ve2cuy/breadboard-PC/ROM.md

## Vue d'ensemble

Voici un schéma de principe des connexions :

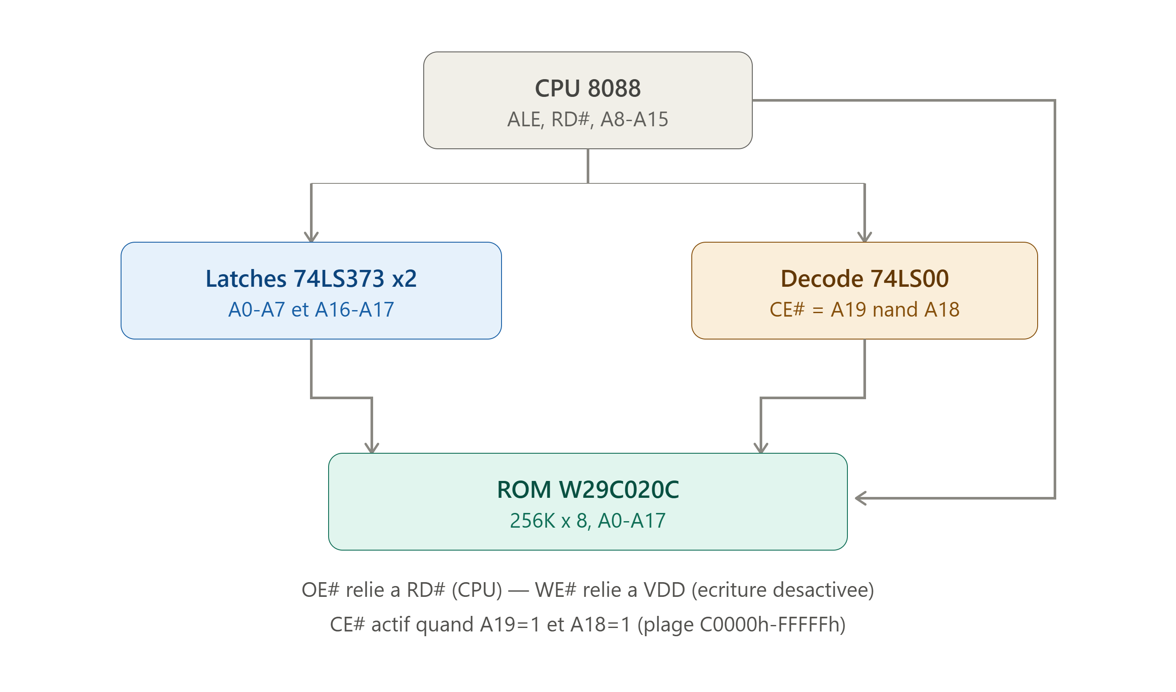
[picture p3: medias/interfacage_8088_w29c020c.png]
w29c020


Le 8088 multiplexe une partie de son bus d'adresses avec les données et les status, donc il faut du matériel de démultiplexage entre le CPU et la ROM.

## Détail du câblage

**Bus d'adresses multiplexé (AD0-AD7)**
Ces 8 broches du CPU (pins 9-16 en boîtier DIP) portent l'adresse en début de cycle bus, puis les données ensuite. Il faut les **latcher** avec un `74LS373` (ou `74LS573`) déclenché par **ALE** (Address Latch Enable, pin 25) pour récupérer A0-A7 de façon stable → connecté à **A0-A7 de la ROM** (pins 12, 11, 10, 9, 8, 7, 6, 5).

**Bus d'adresses/status multiplexé (A16-A19/S3-S6)**
Pareil : ces 4 broches (pins 35-38) sont multiplexées avec des bits de status en mode max. Un second `74LS373` latché par ALE isole **A16 et A17** → connectés à **A16 (pin 2) et A17 (pin 30) de la ROM**. (A18-A19 latchés servent uniquement au décodage, pas à la ROM qui n'a que 18 lignes d'adresse.)

**Bus d'adresses direct (A8-A15)**
Ces broches (pins 22-24, 17-21 en DIP) sont **déjà stables** pendant tout le cycle bus — pas besoin de latch. Connecter **directement** aux entrées **A8-A15 de la ROM** (pins 4, 27, 26, 23, 25, 28, 29, 3 — l'ordre n'est pas séquentiel sur le boîtier, vérifie bien le brochage).

**Décodage du CE# (Chip Enable)**
Ta ROM occupe C0000h-FFFFFh, soit le quart supérieur du méga-octet adressable : cela correspond exactement à **A19=1 ET A18=1**. Une simple porte **NAND 74LS00** (2 entrées : A19 latché, A18 latché) donne directement un signal actif bas quand les deux sont hauts → branche sa sortie sur **CE# (pin 22)** de la ROM.

**OE# et WE#**
- **OE#** (pin 24) ← **RD#** du CPU (pin 32 en min mode) : la ROM ne sort ses données que pendant une vraie lecture.
- **WE#** (pin 31) ← **VDD** (+5V) en permanence : désactive toute écriture accidentelle pendant le fonctionnement normal. Pour reprogrammer la puce, il faudra soit la retirer et utiliser un programmateur externe, soit prévoir un jumper qui reconnecte WE# au WR# du CPU en mode "programmation".

## Point de vigilance

Vérifie que **IO/M#** (pin 28 du 8088) ne doit **pas** activer la ROM pendant les cycles d'E/S — dans ce montage, comme le décodage se fait uniquement sur A18/A19 (qui n'existent pas dans l'espace I/O 16 bits séparé du 8088), il n'y a normalement pas de conflit. Mais si ton design utilise des cycles d'E/S 20 bits étendus ou une autre topologie de bus, ajoute **IO/M#** comme troisième entrée du NAND (via porte NAND 3 entrées type `74LS10`) pour garantir CE# actif uniquement en cycle mémoire.

---

Déboguage

```asm
0C0000 -> 11000000000000000000
080000 -> 10000000000000000000

Adresse   Code obj.      Ligne   Source
-------   ---------      -----   ------------------------------
                            1    ORG     0000h          ; = physique C0000h (début de la ROM)
                            2
                            3    START:
0000      B0 AA             4     MOV     AL, 0AAh       ; AL = 10101010b
0002      E6 10             5     OUT     10h, AL        ; envoie AL sur le port 10h
0004      BB 00             6     MOV     BX, 0000h      ; compteur de délai
                            7    DELAI1:
0007      4B                8     DEC     BX
0008      75 FD             9     JNZ     DELAI1
000A      B0 00            10     MOV     AL, 00h        ; AL = 00000000b
000C      E6 10            11     OUT     10h, AL
000E      BB 00            12     MOV     BX, 0000h
                           13    DELAI2:
0011      4B               14     DEC     BX
0012      75 FD            15     JNZ     DELAI2
0014      EB EA            16     JMP     START          ; boucle infinie

Taille totale du programme : 0016h (22) octets
```

---

# Calcul de la fréquence de clignotement

Compte tenu du programme précédent, avec une fréquence d'horloge du 8088 à 4,77mhz, à quelle fréquence clignote les LED sur le port 10h?

Pour cela, il faut calculer le nombre de cycles d'horloge (clocks) que prend chaque instruction sur un 8088, puis convertir en temps réel avec la fréquence de 4,77 MHz.

# Calcul du clignotement à 4,77 MHz

## Nombre total de cycles CPU par cycle complet (ON + OFF)

| Instruction | Cycles |
|---|---|
| MOV AL,0AAh | 4 |
| OUT 10h,AL | 10 |
| MOV BX,0000h | 4 |
| DELAI1 (boucle complète, 65536 itérations) | 1 179 636 |
| MOV AL,00h | 4 |
| OUT 10h,AL | 10 |
| MOV BX,0000h | 4 |
| DELAI2 (boucle complète) | 1 179 636 |
| JMP START (saut court) | 15 |
| **Total** | **2 359 323 cycles** |

## Fréquence d'horloge

$$T_{clock} = \frac{1}{4{,}77 \text{ MHz}} \approx 209{,}6 \text{ ns}$$

## Durée d'un cycle complet (période)

$$T = \frac{2\,359\,323}{4\,770\,000} \approx 0{,}49466 \text{ s} \approx 494{,}66 \text{ ms}$$

- LED allumée ≈ 247,33 ms
- LED éteinte ≈ 247,33 ms

## Fréquence de clignotement

$$f = \frac{1}{0{,}49466 \text{ s}} \approx \boxed{2{,}022 \text{ Hz}}$$

## Résumé comparatif complet

| Horloge | Période | Fréquence |
|---|---|---|
| 5,33 MHz | 442,6 ms | 2,26 Hz |
| **4,77 MHz** | **494,66 ms** | **2,022 Hz** |
| 10 kHz | ≈ 236 s | 0,00424 Hz |

**À 4,77 MHz, avec le programme original (boucle infinie), la LED clignote en continu à environ 2,02 Hz**, soit un peu plus de 2 fois par seconde — un rythme perceptible et régulier, typique de ce que produirait ce code sur un véritable PC IBM 5150/5160 d'époque.

---

A.B.
