ve2cuy/breadboard-PC/Solution-01/Directives.md

J'ai déplacé la solution-01.asm dans le dossier Solution-01

À partir du dossier Solution-01, voici les tâches à réaliser:

* Sortir les procédures d'affichage du LCD, de transmissions UART ainsi que toutes les procédures associées et les déplacer dans lcd.asm ou uart.asm et sauvegader dans le dossier ./lib
* Rédiger une lib pour delay_ms ainsi qu'une macro 'delay ms' pour son utilisation 
* Rédiger un Make file
* Avec le Make file, produire un fichier .bin pour chacune des procédures (LCD et UART), et enregister sous ./lib/bin.  Enregister delay_ms dans ./lib/utils.bin
* Enregister le fichier .bin du ROM sous Z:\Partage\Alain\rom.bin 

* Dans un nouveau fichier, programmer un accès I2C, en bit banging, sur PA5 et PA0, pour un LCD. L'adresse I2C du LCD est 0x27.
* Incorporer un test de cette nouvelle fonctionnalité dans l'application, par exemple, en affichant Hello World sur le LCD-I2C au démarrage. 

Suite à discussion avec Claude Code (session du 14 septembre 2026), voici les tâches demandées et réalisées:

* Vérifier l'accès local aux outils nécessaires au projet (nasm, make, git, python3) depuis le dossier Solution-01.
* Corriger le Makefile pour qu'il fonctionne correctement sous une session Bash (le check-modules écrivait vers /tmp de façon peu fiable quand make natif Windows invoque le shell MSYS de Git) - "Recadrage pour WSL Bash".
* Committer les changements en attente dans le dépôt (réorganisation du dossier breadboard: fichiers historiques déplacés vers etapes/, solution modularisée dans Solution-01/).
* Rédiger un Makefile.md qui explique le fonctionnement du Makefile (variables, cibles, prérequis/recettes).
* Au démarrage, afficher sur le LCD l'écran suivant pendant 3 secondes:

      Breadboard 8088
      Version 1.0
      --------------------
      (c) VE2CUY 2026

* Diminuer les délais des routines LCD (lcd_short_delai, lcd_delay, lcd_delay_long, lcd_powerup_delay), tout en gardant une légère marge de sécurité, pour un LCD qui répond le plus vite possible.
* Rédiger, dans le dossier Solution-01, un README.md qui explique l'ensemble du projet, décrit la structure des dossiers/fichiers, présente les fonctions d'accès au LCD et à l'UART, énumère les outils nécessaires à la production du .bin final, et explique qu'il faut ouvrir une session WSL sous VS Code pour travailler.
* Dessiner un diagramme de bloc du circuit électronique et l'ajouter au README.md. Note: ROM select sur A19, RAM select sur NOT A19, 8255 select sur A7+IO.
* Réaliser les tâches des lignes 11-12 (accès I2C bit banging au LCD-I2C 0x27, test "Hello World" au démarrage) - implémenté dans lib/lcd_i2c.asm, initialement avec SCL=PA6 (partagée avec E du LCD parallèle).
* Déplacer SCL de PA6 vers PA0 (partagée avec D4 du LCD parallèle plutôt qu'avec E) - élimine tout risque de corruption du LCD parallèle par le trafic I2C, puisque le HD44780 ne capture les lignes de données que sur un front descendant de E, jamais touchée par ce module. i2c_lcd_* est donc utilisable n'importe où dans le projet, sans devoir être suivi d'un lcd_init.
* Affichage sur le LCD-I2C rapporté comme très lent (chaque caractère visible apparaître un par un) - cause: l'implémentation initiale faisait 6 transactions I2C complètes (START+adresse+donnée+STOP) séparées par octet envoyé (une par état EN=0/1/0 de chaque quartet). Corrigé en regroupant les écritures PCF8574 dans une seule transaction par quartet (i2c_lcd_strobe) ou par octet complet (nouveau i2c_lcd_send_byte, utilisé par i2c_lcd_command/i2c_lcd_data) - l'overhead START/adresse/STOP n'est plus payé qu'une fois au lieu de 3x ou 6x.
* Test plus rigoureux du temps de réponse du LCD-I2C: afficher la valeur hex des 16 octets du dump ROM sur le LCD-I2C (4x20), une mise à jour complète par ligne du dump (257 au total). Compilé de façon conditionnelle via la directive `%define TEST_I2C_DUMP` (commentée par défaut) en haut de solution-01.asm - voir README.md.
* Testé sur le matériel réel avec TEST_I2C_DUMP actif: le dump des 16 octets (48 caractères/commandes envoyés au LCD-I2C) prenait au moins 2,5 secondes - beaucoup trop lent. Cause identifiée: ce n'était PAS les délais volontaires (i2c_delay), mais la surcharge d'appels de procédure - chaque bit passait par i2c_set, qui relisait la copie fantôme du Port A via porta_write (lecture-modification-écriture complète, 5 push/pop) à CHAQUE bit (~27 fois par octet PCF8574, ~189 fois par transaction). Corrigé: i2c_start/i2c_stop/i2c_write_byte lisent maintenant la copie fantôme une seule fois par appel (pas par bit) et écrivent directement sur le port (out) pour chaque transition SDA/SCL - i2c_set supprimé (devenu inutile). Vitesse d'horloge I2C (i2c_delay) inchangée.
* Confirmé sur le matériel réel: beaucoup plus rapide après le correctif ci-dessus.
* Publication d'une release GitHub v1.0 (checkpoint stable avant la modification suivante): https://github.com/ve2cuy/i86/releases/tag/v1.0
* Montage confirmé avec une vraie puce 8255A (pas un clone) - remplacer la copie fantôme RAM par une lecture matérielle directe IN AL,PORTA dans i2c_start/i2c_stop/i2c_write_byte (fiable sur un 8255A authentique: un port en sortie renvoie le contenu du verrou de sortie a la lecture). Elimine le passage par VAR_SEG/ES/DI dans ces 3 routines. Sans impact sur porta_write (LCD parallele/UART): aucun de leurs masques ne couvre PA0(SCL)/PA5(SDA), sauf le LCD parallele qui ecrit toujours explicitement son propre bit D4/PA0.
* Testé sur le matériel réel: fonctionne, mais gain non perceptible par rapport à la version précédente - attendu, ce changement n'économise que quelques instructions par APPEL (pas par bit), contrairement à l'optimisation precedente. Question posée: est-ce que la copie fantôme a aussi été éliminée du traitement LCD parallèle? Réponse: non, lcd.asm/uart.asm passent toujours par porta_write (copie fantôme inchangée) - volontairement pas touché, car porta_write est partagé avec l'UART dont le timing bit-à-bit a été calibré a la main (UART_BIT_COUNT, "ne pas modifier sans re-mesurer" dans uart.asm) - un changement de porta_write changerait son nombre de cycles et risquerait de decaler la periode de bit UART.
* Réduction de i2c_delay (bx=2 -> bx=1, ~44,4kHz -> ~88,5kHz) - reduit le plancher impose par les ~189 appels a i2c_delay par transaction, le facteur dominant restant une fois la surcharge d'appels eliminee. Marge sous le plafond I2C 100kHz ramenee de ~125% a ~13% - premier candidat a assouplir (revenir a bx=2) si le LCD I2C devient instable.
* Confirmé sur le matériel réel: les 4 lignes s'affichent presque instantanément, aucune instabilité malgré la marge plus serrée sur i2c_delay.
* Il reste de la place sur les lignes du LCD-I2C (11/20 colonnes utilisées par le hexa) - afficher aussi les caracteres ASCII du dump, comme pour le dump UART (caracteres non imprimables remplaces par '.'). Ajouté à i2c_dump_hex_line (TEST_I2C_DUMP): "XX XX XX XX ASCI" = 16/20 colonnes.
* Petite modification: afficher 8 caractères ASCII sur les lignes 1 et 3 (couvrant aussi les octets de leur ligne suivante), rien sur les lignes 2 et 4. i2c_dump_hex_line scindée en i2c_dump_hex_only_line (hexa seul, lignes 2/4) et i2c_dump_hex_ascii8_line (hexa + 8 ASCII, lignes 1/3 - "XX XX XX XX ASCIIIII" = 20/20 colonnes, pleine largeur).
* Éliminer les redondances du code en utilisant des macros (ex: lcd_goto LINE1 au lieu de la procédure lcd_line1 complète), optimiser tout le code du projet par des techniques de refactoring. Réalisé:
  - Nouveau include/lcd_macros.inc (inclus avant start:, comme delay.inc): macros lcd_goto/lcd_show/i2c_lcd_goto/i2c_lcd_show, remplacent les 16 procédures lcd_line1..4/lcd_show_line1..4/i2c_lcd_line1..4/i2c_lcd_show_line1..4 (lib/lcd.asm, lib/lcd_i2c.asm) - ~20 sites d'appel mis à jour dans solution-01.asm.
  - lib/common.asm: macros génératrices def_tx_hex_nibble/byte/word (remplacent 8 procédures dupliquées - LCD parallèle/UART/LCD-I2C, même logique, seule la procédure d'émission change) et def_busy_delay (remplacent 5 procédures dupliquées: lcd_short_delai/lcd_delay/lcd_delay_long/i2c_delay/uart_bit_delay, même motif dec bx/jnz).
  - solution-01.asm: macro lcd_text pour les ~15 blocs de texte LCD à largeur fixe (db+times+db 0), macro ascii_or_dot (logique dupliquée dump UART/i2c_dump_hex_ascii8_line), macro i2c_dump_hex4 (boucle hexa dupliquée entre i2c_dump_hex_only_line/i2c_dump_hex_ascii8_line, TEST_I2C_DUMP).
  - Aucun changement fonctionnel voulu: vérifié via listing d'assemblage (nasm -l) que les macros génératrices (def_tx_hex_*, def_busy_delay, lcd_text) produisent des octets identiques à l'original; les macros inline (lcd_goto/lcd_show, ascii_or_dot) remplacent un "call" partagé par du code répété à chaque site - légère augmentation du binaire (2983 octets sur 262144, marge de ~0x3F38C octets avant le vecteur de reset), sans risque de dépassement. make all/check/check-modules + build TEST_I2C_DUMP tous validés.
* Confirmé sur le matériel réel: le refactoring par macros fonctionne comme avant (UART et LCD, puis TEST_I2C_DUMP également confirmé).
* Ajouter un 8259 (PIC) au projet - discussion démarrée (décodage d'adresse type 8255, IVT à 0000h:0000h protégée par cli pendant test_ram, séquence ICW1-4, convention PC: IRQ->INT08h+). Mise de côté pour d'abord faire le clavier PS/2 (voir ci-dessous) - lien naturel: CLOCK du PS/2 sur une ligne IRQ serait un cas d'usage plus motivant qu'un bouton-poussoir artificiel pour valider le 8259. À reprendre plus tard.
* Ajouter un clavier PS/2 au projet. Approche retenue après discussion: polling pur pour un premier jalon (pas de 8259 pour l'instant - risque de bits perdus si le programme est occupé ailleurs plus d'une periode de bit, ~60-100us, ex. pendant test_ram - accepté pour ce jalon), Port B du 8255 confirmé libre (PB0=CLOCK, PB1=DATA). Réalisé:
  - Nouveau lib/ps2.asm: ps2_read_byte (lit une trame PS/2 complete - start/8 donnees LSB/parite impaire/stop - bloque jusqu'a reception, verifie la parite et le bit de stop, CF=1 si trame invalide) + ps2_wait_falling_edge (helper: attend un front descendant de CLOCK).
  - include/hardware.inc: MASQUE_PIO conditionnel a TEST_PS2 (Port B en entree seulement si actif - sinon comportement par defaut inchange, verifie octet pour octet: MASQUE_PIO reste 80h).
  - Nouvelle directive %define TEST_PS2 (commentee par defaut, meme convention que TEST_I2C_DUMP): remplace tout le POST par une boucle infinie qui affiche sur l'UART le scan code brut (Set 2) de chaque trame recue - sert a valider le cablage/protocole avant d'ecrire un vrai pilote (traduction scan code -> caractere, pas encore fait).
  - Verifié via listing d'assemblage (nasm -l): MASQUE_PIO=80h par defaut / 82h avec TEST_PS2, logique de ps2_read_byte (boucle de bits, parite, stop, CF) conforme a la conception. make all/check/check-modules + build TEST_PS2 (solution-01.asm ET lib/ps2.asm standalone) tous validés. Pas encore testé sur le matériel réel (nouveau périphérique, jamais branché).
* Confirmé sur le matériel réel: le clavier PS/2 fonctionne, les scan codes s'affichent sur l'UART (TEST_PS2).
* Ajout d'une note README.md sur le câblage USB->PS/2 (VBUS->+5V, D-->Data, D+->Clock, GND->GND) - pour un clavier/câble USB adapté en PS/2.
* Question: utiliser un clavier USB à la place du PS/2 natif? Confirmé fonctionnel avec un clavier USB à repli PS/2 (le clavier lui-même parle le vrai protocole PS/2 via l'adaptateur passif - aucun changement de code). Discussion sur le support USB "pur" (sans repli): pas faisable en bit-banging logiciel sur un 8088 (timing ~100x plus serré que le PS/2) - nécessiterait soit un contrôleur hôte USB dédié (MAX3421E, CH375/376, gros chantier comparable au 8259), soit un micro-contrôleur compagnon qui re-émet en PS/2 (aucun changement de code cote 8088). Mis de côté - clavier USB à repli PS/2 suffisant pour l'instant.
* Publication d'une release GitHub v2.0 (checkpoint stable avant le menu interactif): https://github.com/ve2cuy/i86/releases/tag/v2.0
* Ajouter un menu interactif au clavier PS/2, remplaçant le POST automatique comme comportement PAR DEFAUT (clavier PS/2 desormais requis), affiché sur UART ET LCD parallele. Menu principal (apres le splash): "1) Test RAM / 2) Dump memory / 3) LED Show on PC / 4) Edit RAM". Sous-menu Dump memory: "1) Dump ROM / 2) Dump first 4k RAM / 3) Edit RAM / 9) Home menu". Edit RAM: saisie "Address: 0x0000" puis "Value:   0x00" (hexadecimal, echo clavier), ecrit l'octet en RAM. Réalisé:
  - include/hardware.inc: MASQUE_PIO n'est plus conditionnel a TEST_PS2 - Port B TOUJOURS en entree desormais (le menu en depend des la sortie du splash).
  - lib/ps2.asm: ajout de ps2_keymap (table scan code Set 2 -> ASCII: chiffres 0-9, lettres A-F, Entree, Retour arriere, Echap) + ps2_scancode_to_char (recherche dans la table) + ps2_get_char (bloque jusqu'a une touche reconnue, gere correctement les prefixes 0F0h/relachement et 0E0h/etendue) + ps2_hex_digit_value (caractere -> valeur 0-15) + ps2_read_hex (lit N chiffres hexa avec echo UART+LCD, pas de retour arriere pour ce premier jalon). Le fichier inclut maintenant lib/lcd.asm et lib/uart.asm (reutilise uart_tx_hex_nibble/lcd_tx_hex_nibble pour l'echo) - verifie que ps2.asm reste assemblable seul (check-modules).
  - solution-01.asm: la boucle POST automatique .ici:/.temp: est retiree, remplacee par .main_menu:/.dump_menu: (dispatch sur ps2_get_char). Nouvelles procedures ram_dump_4k (reutilise dump_line telle quelle, pointee sur RAM segment 0000h au lieu de ROM) et edit_ram_action (2 appels a ps2_read_hex, ecrit l'octet en RAM). TEST_PS2 devient un diagnostic BAS NIVEAU optionnel (remplace le menu par l'echo de scan codes bruts) plutot que le seul moyen de tester le clavier, puisque MASQUE_PIO n'est plus conditionnel a cette directive.
  - Anciens textes LCD numerotes (lcd_txt_step1/2/3_l1/l2/l4, "1/3 - Test 8255" etc.) retires (n'avaient plus de sens hors sequence automatique) - remplaces par des textes de menu (lcd_txt_menu_main_l1-4, lcd_txt_menu_dump_l1-4) et des bandeaux "en cours" (lcd_txt_run_*) affiches avant chaque action lancee depuis un menu.
  - Limitation connue: pas de gestion du retour arriere pendant la saisie hexadecimale (ps2_read_hex) - en cas d'erreur, recommencer l'operation depuis le menu. La ligne 4 du LCD pendant "Dump first 4k RAM" affiche encore "/257" (denominateur du dump ROM a 257 lignes) meme si le dump RAM n'en a que 256 - cosmetique seulement, pas corrige.
  - Verifié via listing d'assemblage (nasm -l): dispatch des menus (cmp/jne/jmp), ps2_get_char (gestion E0/F0), ps2_hex_digit_value, ps2_read_hex, edit_ram_action - tout conforme a la conception, registres correctement preserves. make all/check/check-modules + build TEST_PS2 + build TEST_I2C_DUMP tous validés. Menu interactif pas encore testé sur le materiel reel (fonctionnalite neuve).
* Confirmé sur le matériel réel: menu interactif 100% fonctionnel - menu principal, sous-menu Dump memory, Test RAM, Dump ROM, Dump first 4k RAM, LED Show on PC, Edit RAM (saisie hexadecimale + ecriture en RAM), navigation clavier PS/2 - toutes les fonctionnalités testées avec succès.
* Pour l'édition de la RAM: afficher le plus d'octets possible a partir de l'adresse saisie et deplacement, avec les fleches du clavier, dans les octets pour edition. Possibilite de corriger les entrees au clavier. La valeur saisie est enregistree avec la touche Enter. L'edition est terminee lorsque la touche 'q'/'Q' est appuyee. Réalisé - edit_ram_action entierement refaite:
  - lib/ps2.asm: ps2_get_char reconnait maintenant les fleches (scan codes etendus 0E0h+75h/72h/6Bh/74h -> PS2_KEY_UP/DOWN/LEFT/RIGHT, nouvelle table ps2_ext_keymap + ps2_extended_to_char, factorises avec ps2_scancode_to_char via ps2_table_lookup). L'ancienne ps2_read_hex (sans retour arriere) est remplacee par ps2_read_hex_editable (retour arriere: efface visuellement UART ET LCD via repositionnement DDRAM) et un nouveau ps2_edit_byte_value (0-2 chiffres, termine sur Entree plutot qu'a largeur fixe, permet de ne taper qu'1 chiffre).
  - include/hardware.inc: 3 nouvelles variables d'etat dans VAR_SEG (EDIT_BASE_OFF mot + EDIT_ROW_OFF + EDIT_COL_OFF octets), meme zone que PORTA_SHADOW/compteurs du test RAM.
  - solution-01.asm: edit_ram_action affiche maintenant une grille de 24 octets (6 colonnes x 4 lignes - maximise ce qui tient sur le LCD 4x20) a partir de l'adresse saisie, sur UART ET LCD, avec le CURSEUR MATERIEL du LCD (actif, clignotant) indiquant la case selectionnee - plus fiable qu'une emulation logicielle. Nouvelles procedures: edit_ram_draw_grid (redessine tout a chaque deplacement/edition - simple et robuste, mais un peu "bruyant" sur l'UART, ameliorable plus tard), edit_ram_cell_ddram (calcule l'adresse DDRAM de la case courante), edit_ram_place_cursor, edit_ram_write_current, edit_ram_move_left/right/up/down (fixes aux bords de la grille - pas de defilement vers d'autres pages pour ce premier jalon).
  - Bug trouve et corrige AVANT deploiement (revue du listing d'assemblage): dans le dispatch, edit_ram_cell_ddram detruit AL (calcul interne) - la touche deja lue par ps2_get_char devait etre sauvegardee (DL) avant cet appel et restauree apres, sinon ps2_edit_byte_value recevait une valeur erronee comme "premier caractere".
  - Limitation connue: navigation aux fleches limitee a la grille de 24 octets initialement affichee (pas de defilement vers d'autres pages) - quitter avec Q et rouvrir Edit RAM avec une autre adresse pour editer ailleurs.
  - Verifié via listing d'assemblage (nasm -l), en detail, apres correction du bug ci-dessus: dispatch complet, edit_ram_cell_ddram/write_current/move_*, registres correctement preserves partout. make all/check/check-modules + build TEST_PS2 + build TEST_I2C_DUMP tous validés. Pas encore testé sur le materiel reel (fonctionnalite neuve).
* Bug rapporté sur le matériel réel: la touche 'q' ne fonctionne pas, impossible de quitter l'édition de la RAM. Cause: Q (scan code Set 2 015h) avait tout simplement été oublié dans ps2_keymap (lib/ps2.asm) - ps2_get_char l'ignorait silencieusement comme n'importe quelle touche non reconnue, donc edit_ram_action ne recevait jamais 'Q'. Corrigé: ajout de `db 015h, 'Q'` à ps2_keymap. make all/check/check-modules revalidés.
* Lors de l'édition, la touche Enter devrait passer à l'octet suivant et non pas revenir sur l'octet courant. Réalisé: nouvelle procédure edit_ram_advance (solution-01.asm) - déplace le curseur logique à la case suivante en ordre de lecture (gauche à droite, puis ligne suivante, fixe à la dernière case de la grille - pas de défilement), appelée après edit_ram_write_current dans le dispatch de edit_ram_action, uniquement quand Entrée a effectivement écrit une valeur (pas si Entrée est pressée sans saisie). Vérifié via listing d'assemblage. make all/check/check-modules revalidés.
* Pour le DUMP de mémoire, consolider RAM et ROM sous une seule option et au lieu de fixer la taille du bloc, il faut saisir l'adresse de départ, sous la forme 0x0000:0x0000, et l'adresse de fin. Réalisé:
  - solution-01.asm: rom_dump et ram_dump_4k sont retirées, remplacées par une seule dump_memory_action. Demande une adresse de DEPART puis une adresse de FIN, chacune saisie au clavier sous la forme SEGMENT:OFFSET (4+4 chiffres hexa, retour arrière via ps2_read_hex_editable, même mécanique que edit_ram_action) - "Start: 0xSSSS:0xOOOO" sur la ligne 1 du LCD, "End:   0xSSSS:0xOOOO" sur la ligne 2. Fonctionne indifféremment pour la ROM, la RAM ou n'importe quelle plage intermédiaire, y compris à cheval sur une frontière de segment (ex: 0000:FFF0 à 1000:0010) - le segment ES est avancé de 1000h chaque fois que l'offset DI déborde en ajoutant 16. Nouvelle procédure mem_calc_physical (segment:offset -> adresse physique 32 bits DX:AX) utilisée pour calculer le nombre total de lignes à afficher ET pour rejeter une plage invalide (fin < départ - message d'erreur UART, rien n'est dumpé).
  - include/hardware.inc: 5 nouvelles variables VAR_SEG (DUMP_START_SEG_OFF/DUMP_START_OFF_OFF/DUMP_END_SEG_OFF/DUMP_END_OFF_OFF pour les 4 valeurs saisies, DUMP_LINES_LEFT_OFF pour le compteur de lignes restantes).
  - Menu Dump memory renuméroté: "1) Dump memory / 2) Edit RAM / 9) Home menu" (retire "Dump ROM"/"Dump first 4k RAM" séparés).
  - dump_line: la ligne 4 du LCD affiche maintenant "Ligne: NNN" sans dénominateur ("/257" retiré - n'avait plus de sens pour une plage de taille variable). Limitation documentée: lcd_tx_dec3 n'affiche que 3 chiffres, incorrect au-delà de 999 lignes (cosmétique, le dump UART reste toujours exact).
  - Bug trouvé et corrigé AVANT déploiement (revue du listing d'assemblage): dump_line détruit CX en interne (boucles de prévisualisation LCD/hexa/ASCII, jamais préservé - son propre en-tête ne garantit que BX/ES/le fait que DI avance de 16). La première version de la boucle de dump_memory_action utilisait une instruction `loop` classique sur CX autour des appels à dump_line, ce qui aurait cassé le compteur dès la première ligne. Corrigé: le compteur de lignes restantes est maintenant stocké en RAM (DUMP_LINES_LEFT_OFF, VAR_SEG) et décrémenté explicitement après chaque appel, avec sauvegarde/restauration de ES (segment du dump en cours) autour du court aller-retour vers VAR_SEG.
  - Vérifié via listing d'assemblage (nasm -l), en détail: dispatch du menu, mem_calc_physical, comparaison/soustraction 32 bits, décompte du nombre de lignes, gestion du débordement de segment, registres correctement préservés partout. make all/check/check-modules + build TEST_PS2 + build TEST_I2C_DUMP tous validés. Pas encore testé sur le matériel réel (fonctionnalité neuve).
* La touche ESC doit permettre d'interrompre un DUMP et retourner au menu. Réalisé: dans la boucle de dump_memory_action, avant chaque ligne, une vérification NON BLOQUANTE ("IN AL,PORTB" - CLOCK/PB0 est haut au repos, voir lib/ps2.asm) détecte si une trame PS/2 est en cours; si oui, ps2_get_char la lit entièrement (bloquant, bref) et si le caractère est Echap (27, déjà mappé dans ps2_keymap), le dump s'arrête immédiatement (message UART "*** Dump interrompu (Echap) ***", jaune) et retourne au menu Dump memory - sans ralentir le dump quand aucune touche n'est pressée (cas normal). Bug trouvé et corrigé AVANT déploiement (revue du listing): ps2_get_char détruit BX (utilisé ici comme numéro de ligne courant, doit survivre) - ajout d'un push bx/pop bx autour de l'appel. Limitation documentée (best-effort, pas une garantie): une touche pressée et relâchée très brièvement pendant l'impression d'une ligne (plusieurs dizaines de ms sur l'UART logiciel à 9600 bauds) peut échapper à la vérification suivante. Vérifié via listing d'assemblage. make all/check/check-modules + build TEST_PS2 + build TEST_I2C_DUMP tous validés. Pas encore testé sur le matériel réel.
* Question: pour dumper les 16 derniers octets de la ROM, est-ce bien "FFFF:FFF0 à FFFF:FFFF"? Réponse: non - le 8088 n'a que 20 lignes d'adresse (pas de ligne A20), l'adresse physique réelle (segment×16+offset) boucle au-delà de FFFFFh, donc FFFF:FFF0 calcule 10FFE0h qui boucle à 0FFE0h (RAM basse, pas la ROM). La bonne plage est F000:FFF0 à F000:FFFF (F000h×16+FFF0h = FFFF0h, même segment que le vecteur de reset matériel). Aucun changement de code requis (dump_memory_action calcule déjà correctement les adresses physiques dans les 20 bits utiles pour tout segment/offset raisonnable - seul ce cas limite "wraparound" au sommet de l'espace d'adressage 8088 prête à confusion). Ajouté un exemple explicite dans README.md pour prévenir ce piège classique.
* 1) Retirer le Hello World du LCD_I2C, remplacé par la version de l'application et par les paramètres de la connexion UART. 2) Réduire le temps d'affichage de l'écran de démarrage à 1 seconde. Réalisé:
  - solution-01.asm (start:): l'ancien test i2c_lcd_init + "Hello World" (une seule ligne) est remplacé par 4 lignes sur le LCD I2C via i2c_lcd_show: lignes 1/2/4 réutilisent directement lcd_txt_splash_l1/l2/l4 ("Breadboard 8088" / "Version 1.0" / "(c) VE2CUY 2026" - déjà définis pour le splash du LCD parallèle, aucune duplication), ligne 3 = nouveau texte i2c_txt_uart_params ("UART: 9600 8N1", sans padding, même convention que l'ancien i2c_txt_hello).
  - delay_ms (3*SECONDE) -> delay_ms (1*SECONDE) pour l'écran de démarrage du LCD parallèle.
  - Ancien label i2c_txt_hello retiré (plus référencé nulle part - vérifié par grep avant suppression).
  - Vérifié: make all/check/check-modules + build TEST_PS2 + build TEST_I2C_DUMP tous validés. Pas encore testé sur le matériel réel.
* Confirmé sur le matériel réel: bonne disposition sur le LCD I2C, tout est parfait et fonctionnel (version app + paramètres UART sur les 4 lignes, splash à 1 seconde).
* Publication d'une release GitHub v3.0 (checkpoint stable avant l'ajout des interruptions logicielles type BIOS): https://github.com/ve2cuy/i86/releases/tag/v3.0
* Pour les routines d'affichage et de saisie via le clavier, implémenter l'utilisation d'interruptions logicielles en utilisant les standards du BIOS de l'IBM PC. Discussion: INT n/IRET sont purement logiciels sur le 8088 (contrairement au 8259/IRQ, toujours mis de côté) - aucun composant supplémentaire requis, seulement peupler l'IVT (segment 0000h, deja reserve/protege pendant test_ram). Portée retenue avec l'utilisateur: INT 10h AH=02h (Set cursor position: DH=Row, DL=Column) et AH=09h (Write character: AL=Character, BH=device number [1=LCD, 2=LCD_I2C], BL=Color [N/A pour l'instant, reserve UART], CX=nombre de repetitions); INT 16h AH=01h (Read Character non bloquant: AH=scan code, ZF=0 si touche pressee, AL=caractere ASCII, AX=0 si aucune touche). Réalisé:
  - lib/ps2.asm: ps2_get_char expose maintenant aussi BH = scan code PS/2 Set 2 brut de la touche reconnue (en plus de AL) - ps2_scancode_to_char/ps2_extended_to_char preservent BX (push/pop), donc le sauvegarder avant leur appel suffit. Aucun appelant existant affecte (BH etait deja "detruit", verifie par grep sur tous les sites d'appel).
  - include/hardware.inc: 2 nouvelles variables VAR_SEG (BIOS_CURSOR_ROW_OFF/BIOS_CURSOR_COL_OFF) pour le curseur logique partage entre les 2 afficheurs.
  - solution-01.asm: nouvelles procedures setup_bios_interrupts (peuple l'IVT segment 0000h pour INT 10h/16h, initialise le curseur a (0,0) - appelee une seule fois au demarrage, juste apres l'init de la copie fantome du port A), bios_cursor_ddram (DH=ligne/DL=colonne -> AH=adresse DDRAM, meme logique que edit_ram_cell_ddram), int10h_handler (dispatch AH=02h/09h, AH=09h remplit CX cellules consecutives sans deplacer le curseur logique - meme convention que le vrai BIOS), int16h_handler (AH=01h, non bloquant via la meme technique que l'interruption Echap de dump_memory_action: IN AL,PORTB puisque CLOCK/PB0 est haut au repos).
  - Point delicat verifie en detail via listing d'assemblage (nasm -l), octet par octet: IRET restitue les FLAGS TELS QU'EMPILES PAR L'INSTRUCTION INT (pas l'etat courant du CPU) - int16h_handler doit donc ecraser directement ce mot sur la pile pour que le ZF soit visible a l'appelant. Technique: mov bp,sp AVANT pushf (bp fige la position, insensible au deplacement de SP par pushf - le 8086 ne permet pas [SP+depl] directement), puis "pop word [bp+18]" ecrase le mot FLAGS original (18 = 14 octets deja empiles + 4 pour IP/CS empiles par INT avant FLAGS). Confirme dans le listing: "8F4612" = pop word [bp+12h] = [bp+18] exactement comme prevu. AX n'est PAS preserve dans int16h_handler (c'est la sortie voulue), contrairement a int10h_handler ou rien n'est documente comme sortie.
  - Verifié via listing d'assemblage en detail (setup_bios_interrupts: adresses IVT 0040h/0058h correctes, pointeurs FAR vers int10h_handler/int16h_handler confirmes octet pour octet; int10h_handler: push/pop symetriques, dispatch AH, boucle CX pour AH=09h). make all/check/check-modules + build TEST_PS2 + build TEST_I2C_DUMP tous validés. Pas encore testé sur le matériel réel (fonctionnalité neuve et delicate - manipulation manuelle de la pile).
* Question: as-tu fait des appels a ces INT dans le code? Réponse: non, aucun (verifie par grep) - seuls les gestionnaires etaient installes (IVT peuplee), rien ne les invoquait encore.
* Convertir l'écran de démarrage (pour utiliser INT 10h). Réalisé: nouvelle procedure splash_print_line (solution-01.asm) - affiche une ligne (jusqu'a 20 caracteres) caractere par caractere via INT 10h (AH=02h pour repositionner, puis AH=09h pour ecrire - AH=09h ne deplace pas le curseur logique, meme convention que le vrai BIOS, donc AH=02h doit etre repete avant CHAQUE caractere), cible le LCD PARALLELE (BH=1). Repose sur le fait qu'int10h_handler preserve integralement AX pour AH=02h/09h (aucune sortie documentee dans AX) - AL (le caractere) survit donc a l'appel AH=02h sans sauvegarde explicite. L'ecran de demarrage (start:, LCD parallele, 1 seconde) appelle maintenant splash_print_line x4 (une fois par ligne) au lieu de lcd_show directement - premier usage reel de l'interface "esprit BIOS". L'ecran LCD I2C (version app + parametres UART) et le reste du menu ne sont PAS touches (toujours des appels directs) - portee volontairement limitee a "l'ecran de demarrage" (terme deja utilise dans les commentaires du code pour designer specifiquement cet ecran). Vérifié via listing d'assemblage (nasm -l): les 2 "int 10h" (CD10) generes correctement, ordre setup_bios_interrupts (avant tout usage) / lcd_init (avant le premier appel) confirme. make all/check/check-modules + build TEST_PS2 + build TEST_I2C_DUMP tous validés. Pas encore testé sur le matériel réel.
* Questions de compréhension sur setup_bios_interrupts (pourquoi *4 dans "mov word [es:10h*4], int10h_handler", est-ce que le programme calcule une adresse physique pour la placer dans l'IVT). Réponses données puis ajoutées au README.md (nouvelle sous-section "Initialisation de l'IVT: calcul d'adresse", sous "Interruptions logicielles type BIOS"): chaque entree IVT fait 4 octets car c'est un pointeur FAR (2 octets offset + 2 octets segment, PAS une adresse 20 bits stockee d'un bloc) - 256 numeros d'interruption x 4 octets = 1024 octets = exactement le segment 0000h:0000h-0000h:03FFh deja reserve. L'offset (int10h_handler) est resolu par NASM A L'ASSEMBLAGE (constante connue d'avance, -f bin a plat, ORG 0000h) - PAS calcule par le programme a l'execution; le segment (cs) est lu a l'execution (vaut C000h, fixe par le vecteur de reset materiel). Le CPU combine les deux (segment*16+offset) seulement au moment d'executer INT 10h/16h - meme formule que le piege FFFF:FFF0.
* Confirmé sur le matériel réel: l'affichage via INT 10h fonctionne (écran de démarrage, splash_print_line - AH=02h/09h).
* Ajouter 2 macros pour l'affichage: 1) gotoxy ligne colonne device (constantes LCD/LCDI2C/UART), 2) print texte device (memes constantes) - remplacent les blocs "mov si,X / mov dh,N / call splash_print_line" et "mov si,X / i2c_lcd_show LCD_LINEn". 3) Remplacer tous les affichages de texte par la macro print. Affichage via INT 10h. Discussion (AskUserQuestion): ~71 sites trouves (37 UART, 19 LCD, 4 LCD-I2C, 11 lcd_print directs) - certains simples, d'autres composes (bandeaux avec valeurs hexa inserees entre plusieurs fragments). Portee choisie: "Tout sauf les bandeaux composés" - tous les affichages de chaine simple convertis (~40 sites), les bandeaux composes (dump_memory_action, dump_line, msg_bloc_progression lignes 2/4, msg_defaut_detail, effet1) gardent les appels directs. Réalisé:
  - include/hardware.inc: BIOS_CURSOR_ROW_OFF/COL_OFF renommes et dedoubles en BIOS_CURSOR_LCD_ROW_OFF/COL_OFF + BIOS_CURSOR_LCDI2C_ROW_OFF/COL_OFF - UN JEU DE CURSEUR PAR DEVICE desormais (auparavant partage entre LCD parallele et LCD I2C), pour que gotoxy+device soit reellement significatif et pas juste decoratif.
  - solution-01.asm (int10h_handler): AH=02h lit maintenant BH pour choisir quel curseur mettre a jour (1=LCD, 2=LCD I2C, UART/autre=no-op, pas de curseur pour un flux serie). AH=09h etendu: BH=3 (UART) transmet directement AL, CX fois, via uart_tx_byte en boucle (pas de positionnement DDRAM, juste une repetition comme le "remplissage" du vrai BIOS).
  - solution-01.asm: splash_print_line generalisee en int10h_print_string (BH=device en entree au lieu de BH=1 fige, relit le curseur DU DEVICE CONCERNE avant de boucler caractere par caractere pour LCD/LCD I2C, ou transmet directement pour UART sans aucun positionnement).
  - include/lcd_macros.inc: constantes LCD=1/LCDI2C=2/UART=3, macros gotoxy (3 parametres: ligne, colonne, device -> AH=02h) et print (2 parametres: texte, device -> appelle int10h_print_string). N'affectent aucun registre de l'appelant (tout est preserve en interne, meme discipline que lcd_goto/lcd_show deja existantes).
  - ~40 sites convertis dans tout le fichier: cls (macro), splash LCD+LCD-I2C, bandeau d'identification, menu principal + sous-actions (Test RAM/LED Show/Edit RAM), menu Dump memory, TEST_PS2 (attente/erreur/crlf - mais PAS le scan code brut, compose avec uart_tx_hex_byte), messages de fin (msg_dump_fin, msg_ram_ok, msg_ram_defectueuse, msg_banniere), messages d'erreur de dump_memory_action (interrompu/plage invalide - simples malgre leur emplacement dans une fonction par ailleurs composee), aide edit_ram_action (txt_edit_help), etat OK/DEFAUT de msg_bloc_progression (ligne 3 seule, contrairement aux lignes 2/4 qui restent composees).
  - Vérifié en detail via listing d'assemblage (nasm -l): int10h_handler (dispatch BH pour AH=02h ET AH=09h, boucle UART), int10h_print_string (push/pop symetriques, relecture du curseur par device), expansion des macros gotoxy/print (registres corrects, aucun octet superflu). make all/check/check-modules + build TEST_PS2 + build TEST_I2C_DUMP tous validés. Pas encore testé sur le matériel réel (changement de grande ampleur).
* Bug rapporté sur le matériel réel (test de Dump memory pour examiner l'IVT): 1) en saisissant "0000" pour le segment, "5000" est traité à la place. 2) la touche 'q' ne fonctionne plus dans le DUMP. Diagnostic du bug #1: régression introduite lors de l'ajout de INT 16h - ps2_get_char expose maintenant le scan code PS/2 brut via BH à CHAQUE appel (voir ce commit plus haut), ce qui corrompt tout accumulateur multi-chiffres logé dans BX à travers plusieurs appels. ps2_read_hex_editable ET ps2_edit_byte_value utilisaient justement BX comme accumulateur persistant. Trace confirmant exactement le symptôme: scan code Set 2 de '0' = 045h. Après le 1er '0', BX=0x4500 (BH=scan code, BL=0 du xor initial). Au 2e chiffre, "shl bx,4" donne 0x45000, tronqué à 16 bits = 0x5000 - correspond exactement à "0000" -> "5000" rapporté. Corrigé:
  - lib/ps2.asm: ps2_read_hex_editable ET ps2_edit_byte_value utilisent maintenant SI comme accumulateur interne (jamais touché par ps2_get_char - voir son en-tête "Jamais SI/DI/ES/BP") au lieu de BX. SI de l'appelant sauvegardé/restauré (push/pop) en entrée/sortie de chaque procédure - BX reste la sortie documentée (transféré depuis SI juste avant chaque retour réussi). Fusion d'un chiffre dans l'accumulateur adaptée: "shl si,cl" puis un ADD via DX temporairement mis à 0 en DH (puisque SI n'a pas de sous-registre 8 bits accessible comme BL, contrairement à BX - "or bl,dl" n'a pas d'équivalent direct "or si-bas,dl"; DH/DL sont sauvegardés ensemble via push/pop autour de ce court calcul pour ne pas perdre le compteur de chiffres DH).
  - Bug #2 ('q' dans le DUMP): pas encore reproduit/isolé avec certitude - clarification demandée à l'utilisateur (saisie d'adresse du dump? dump actif à interrompre? Edit RAM?) pour déterminer si c'était un symptôme du même bug #1 (maintenant corrigé) ou un problème distinct.
  - Vérifié en détail via listing d'assemblage (nasm -l) + trace manuelle des deux procédures corrigées (ex: "00AB" -> accumulation correcte 0x00AB). make all/check/check-modules + build TEST_PS2 + build TEST_I2C_DUMP tous validés. Correction déployée, pas encore reconfirmée sur le matériel réel.
* Pour le DUMP, pouvoir couvrir plus de 64K - ex: 0x0000:0000 à 0xf000:ffff devrait fonctionner. Analyse: l'implémentation existante précalculait un "nombre total de lignes" (32 bits: diff/16+1) puis le stockait dans un mot de 16 bits pour le décompte - MAIS pour la plage maximale de ce matériel (0000:0000 à F000:FFFF), ce total vaut EXACTEMENT 65536, qui ne tient pas dans un mot 16 bits (déborde silencieusement à 0). Trace: par coïncidence mathématique (arithmétique modulo 65536), le décompte fonctionnait quand même correctement pour CE cas précis (0 - 65536 décréments = 0 à nouveau) - mais c'était fragile et non robuste par conception, pas garanti pour d'autres cas limites. Redesign complet pour une correction PAR CONCEPTION plutôt que par coïncidence:
  - include/hardware.inc: DUMP_LINES_LEFT_OFF (compteur de lignes, mot 16 bits) retiré, remplacé par DUMP_END_PHYS_LO_OFF/DUMP_END_PHYS_HI_OFF (adresse physique de fin, 32 bits) - décalage des offsets BIOS_CURSOR_* qui suivaient.
  - solution-01.asm (dump_memory_action): au lieu de précalculer un total de lignes, l'adresse physique de fin (32 bits) est mémorisée une fois validée, puis COMPARÉE À L'ADRESSE PHYSIQUE COURANTE (recalculée via mem_calc_physical a partir de ES:DI) à CHAQUE ligne - continue tant que courante <= fin. Élimine complètement le risque de débordement 16 bits (les adresses physiques comparées tiennent confortablement dans les 20 bits utiles de ce matériel).
  - Cas limite additionnel identifié et corrigé AVANT déploiement (pas rapporté par l'utilisateur - trouvé en analysant le nouveau design): quand le DÉBORDEMENT DE SEGMENT lui-même déborde 16 bits (ES déjà à F000h-FFFFh, "add ax,1000h" donnerait 10000h), le segment reviendrait FAUSSEMENT à 0000h - la comparaison d'adresse physique suivante utiliserait alors une adresse ERRONÉE (physique 0 au lieu du "vrai" FFFFFh+1, un 21e bit que ce matériel ne peut pas représenter), concluant à tort qu'il faut continuer et provoquant une boucle infinie qui redump tout l'espace d'adressage en continu. Corrigé: le flag CF (retenue) de "add ax,1000h" est vérifié directement - s'il est posé, la plage maximale du matériel vient d'être entièrement couverte, le dump s'arrête immédiatement (avant même de faire le "mov es,ax" avec la valeur erronée).
  - Optimisation découverte en cours de route: BP peut adresser VAR_SEG DIRECTEMENT sans passer par ES, car SS = VAR_SEG (=STACK_SEG=1000h) EN PERMANENCE depuis l'initialisation de la pile au tout début de start: (jamais réassigné ensuite) - et l'adressage [BP+déplacement] utilise SS par défaut sur le 8086 (pas besoin de prefixe "ss:" explicite). Évite d'avoir à sauvegarder/restaurer ES (segment du dump en cours) autour de l'accès a la RAM partagée dans la boucle.
  - Vérifié en détail via listing d'assemblage (nasm -l), octet par octet: "add ax,1000h" + "jc" confirmé correct, "cmp dx,[bp]"/"cmp ax,[bp]" confirmés sans préfixe de segment (adressage SS implicite via BP). Trace manuelle complète du cas 0000:0000-F000:FFFF (65536 lignes, arrêt correct via le CF de l'avance de segment) ET d'un petit cas normal (0000:0000-0000:001F, 2 lignes, arrêt correct via la comparaison d'adresse physique). make all/check/check-modules + build TEST_PS2 + build TEST_I2C_DUMP tous validés. Pas encore testé sur le matériel réel.
* Confirmé sur le matériel réel: le bug "0000" -> "5000" est corrigé (accumulateur SI dans ps2_read_hex_editable/ps2_edit_byte_value), et l'IVT est correctement initialisé (INT 10h/16h aux bonnes entrées, reste de l'IVT en RAM résiduelle comme attendu). Bug #2 ('q' ne fonctionne plus dans le DUMP) toujours non clarifié/non reproduit - en attente de précisions de l'utilisateur.
* Il y a beaucoup de garbage dans la mémoire. Au démarrage: 1) initialiser toute la RAM à 0. 2) initialiser tous les vecteurs de l'IVT avec un appel à une fonction qui affiche sur l'UART que l'interruption n'est pas implémentée. 3) Après, vient l'initialisation de nos vecteurs (INT 10h/16h). Réalisé:
  - solution-01.asm (start:): nouveau bloc EN LIGNE (pas de CALL) juste après l'init de SS/SP - efface les 128K de RAM (segments 0000h et 1000h) via "rep stosw" (AX=0 comme valeur de remplissage tout du long, CX sert de registre de transfert pour charger ES du 2e segment sans toucher à AX). Doit être en ligne (pas une procédure appelée): le segment 1000h contient la pile déjà active (SS/SP), et un retour d'appel qui s'y trouverait serait effacé par erreur - sans risque ici puisque rien n'a encore été empilé à ce stade du démarrage.
  - Nouvelles procédures init_ivt_not_implemented (peuple les 256 entrées de l'IVT avec int_not_implemented) et int_not_implemented (affiche "*** Interruption non implementee ***" sur l'UART via un appel DIRECT à uart_tx_string - pas la macro "print", qui passe par INT 10h - pour rester indépendant de ce qui pourrait être en cause si une interruption inattendue survient - puis IRET).
  - Ordre au démarrage confirmé: efface RAM -> init_8255/copie fantôme port A -> init_ivt_not_implemented (256 entrées) -> setup_bios_interrupts (remplace ENSUITE seulement les entrées INT 10h/16h par nos gestionnaires reels).
  - Vérifié en détail via listing d'assemblage (nasm -l), octet par octet: "rep stosw" (F3AB) confirmé aux 2 bons endroits, AX jamais modifié entre les deux, boucle de 256 itérations (CX=100h) confirmée dans init_ivt_not_implemented, adresse de int_not_implemented (0AA6h) confirmée correcte dans le pointeur FAR ecrit a chaque entree. make all/check/check-modules + build TEST_PS2 + build TEST_I2C_DUMP tous validés.
* Confirmé sur le matériel réel: le Dump du premier 1 Ko (l'IVT) confirme la mise à zéro de la RAM (segment 0000h effacé avant d'être repeuplé) ainsi que la mise en place correcte de l'IVT (int_not_implemented partout sauf 0040h/0058h).
* Pour l'édition de la RAM: pouvoir spécifier une plage (taille en octets, discussion préalable via AskUserQuestion) et se déplacer avec les flèches haut/bas même si la plage déborde des 4 lignes d'affichage (défilement). Si Échap est appuyé, aucune modification n'est enregistrée; si 'q' est appuyé, les changements sont enregistrés. Limiter la taille de la plage à 1024 octets. Ne pas permettre de modifier l'IVT - proposer (en pratique: valider et rejeter, discussion préalable) une adresse de départ supérieure à l'IVT. Correction de l'adresse possible pendant la saisie (déjà le cas via ps2_read_hex_editable). Réalisé - refonte complète de edit_ram_action:
  - include/hardware.inc: zone réservée de VAR_SEG agrandie de 1 à 2 Ko pour loger un TAMPON DE TRAVAIL de 1024 octets (EDIT_BUFFER_OFF) - toute l'édition s'y fait, jamais directement en RAM réelle. Nouvel état: EDIT_SIZE_OFF (taille saisie), EDIT_CURSOR_OFF (position linéaire du curseur dans le tampon/la plage, remplace EDIT_ROW_OFF/EDIT_COL_OFF), EDIT_WINDOW_ROW_OFF (ligne logique affichée en haut, pour le défilement).
  - solution-01.asm (test_ram): nombre d'octets testés réduit de 130048 à 129024 (127→126 blocs) en conséquence de l'agrandissement de la zone réservée - tous les messages/textes concernés mis à jour (txt_ram_ok, txt_banniere2, lcd_txt_bloc_mid).
  - solution-01.asm (edit_ram_action): demande adresse de départ (rejetée si < 0x0400, message d'erreur) PUIS taille en octets (rejetée si 0, >1024, ou si depart+taille-1 déborde 0xFFFF) - reprend le pattern de validation déjà établi par dump_memory_action. edit_ram_load_buffer copie la plage réelle vers le tampon au démarrage; edit_ram_commit_buffer fait l'inverse, appelée UNIQUEMENT sur Q/q (jamais sur Échap - qui saute directement à la sortie sans rien recopier).
  - Nouvelles procédures: edit_ram_scroll_to_cursor (ajuste la fenêtre visible pour garder le curseur logique visible, réutilisée par move_up/move_down/advance), edit_ram_draw_grid (réécrite: lit le TAMPON au lieu de la RAM réelle, calcule la ligne logique de chaque ligne visible via fenêtre+déplacement, gère les lignes/colonnes au-delà de la plage réelle avec des espaces de remplissage), edit_ram_cell_ddram (réécrite: position DDRAM dérivée du curseur linéaire ramené à sa position VISIBLE via la fenêtre).
  - Astuce découverte: BP adresse VAR_SEG directement via SS (= VAR_SEG en PERMANENCE depuis l'init de la pile, jamais réassigné ensuite) - [BP] utilise SS par défaut sur le 8086, évite de jongler avec ES pour les nombreux accès aux nouvelles variables partagées.
  - DEUX bugs trouvés et corrigés AVANT déploiement par relecture attentive du listing ET trace manuelle (méthodologie renforcée pour cette fonctionnalité, la plus complexe de la session): 1) edit_ram_draw_grid réutilisait BX (fenêtre visible) ET CX (taille totale) d'une itération de ligne à l'autre SANS les relire depuis la RAM - BX se faisait écraser par le nombre de colonnes valides de la ligne précédente, corrompant le calcul de la ligne suivante. Corrigé: BX/CX sont relus depuis EDIT_WINDOW_ROW_OFF/EDIT_SIZE_OFF au début de CHAQUE ligne. 2) edit_ram_move_down, pour une plage tenant sur une seule ligne partielle (taille < 6), sautait du début à la fin de CETTE MÊME ligne au lieu de ne rien faire (aucune ligne existe en dessous) - corrigé en vérifiant D'ABORD qu'une ligne suivante existe réellement (même partielle) avant de calculer la nouvelle position.
  - Vérifié en détail via listing d'assemblage (nasm -l), octet par octet, PUIS trace manuelle complète de plusieurs scénarios (édition simple sans défilement, défilement vers le bas puis vers le haut à travers plusieurs lignes, dernière ligne partielle avec colonne dépassant sa largeur réelle - clampée correctement, plage d'un seul octet). make all/check/check-modules + build TEST_PS2 + build TEST_I2C_DUMP tous validés. Pas encore testé sur le matériel réel (fonctionnalité la plus ambitieuse et la plus à risque de la session).
* Bug rapporté sur le matériel réel: dans Edit RAM, lors du déplacement, le premier caractère de l'adresse des deux premières lignes n'est pas affiché. Diagnostic: chaque ligne du LCD affichait une étiquette d'adresse ("SSSS: ", 6 caractères, ajoutée lors de la refonte précédente pour aider à s'orienter pendant le défilement) + la grille compacte (6 cases "XX " = 18 caractères) = 24 caractères au total, DÉPASSANT LA LARGEUR DE 20 CARACTÈRES DU LCD DE 4. Sur cet afficheur 4x20 "type A", LCD_LINE1<->LCD_LINE3 et LCD_LINE2<->LCD_LINE4 partagent chacun un même bloc de 40 octets de DDRAM (l'auto-incrémentation boucle à l'intérieur de CE bloc) - le débordement de 4 caractères d'une ligne (ex: LCD_LINE1) se retrouve donc au DÉBUT de sa ligne pairée (LCD_LINE3), et puisque LCD_LINE3 est dessinée JUSTE APRÈS dans la boucle de edit_ram_draw_grid, SON PROPRE débordement de 4 caractères boucle à son tour et écrase le DÉBUT de LCD_LINE1 (l'étiquette d'adresse qu'on venait de dessiner correctement) - même mécanique pour LCD_LINE2/LCD_LINE4. Corrigé: l'étiquette d'adresse par ligne est retirée du LCD (gardée sur l'UART uniquement, où la largeur n'est pas contrainte) - la grille LCD retrouve son format compact d'origine (18 caractères, tient dans les 20 disponibles). edit_ram_cell_ddram (qui avait été modifiée en même temps pour tenir compte de cette étiquette, +6 au décalage colonne) est revenue à sa formule d'origine (col*3, sans décalage). Cette omission (compter la largeur totale d'une ligne LCD avant de l'écrire) est exactement le genre de vérification que le reste du projet fait déjà systématiquement (dump_line, msg_bloc_progression: toutes les lignes LCD sont délibérément complétées à EXACTEMENT 20 caractères, jamais plus) - à appliquer plus rigoureusement pour toute future modification touchant l'affichage LCD par ligne. Vérifié via listing d'assemblage. make all/check/check-modules + build TEST_PS2 + build TEST_I2C_DUMP tous validés.
* Confirmé sur le matériel réel: Edit RAM fonctionne correctement (adresse/taille, grille, défilement, édition, Q/Échap) - le correctif de l'étiquette d'adresse LCD est validé.
* Dans le sous-menu Dump memory, ajouter une option qui affiche le contenu des registres du 8088, sur le LCD et l'UART. Pour l'UART, produire un affichage ergonomique, incluant la valeur des Flags. La touche ESC permet de revenir au menu précédent. Réalisé - registers_dump_action (option 3 du menu Dump memory):
  - Capture immédiate à l'entrée (avant tout usage des registres généraux comme espace de travail): AX/BX/CX/DX/SI/DI empilés, plus CS/DS/ES/SS/FLAGS (empilés seulement pour lecture, jamais restaurés dans un registre - ils ne sont jamais modifiés par cette routine). BP fixé juste après "push bp"/"mov bp,sp" (même "prologue de trame de pile" qu'un compilateur C) - les valeurs empilées AVANT ce point (BP original, adresse de retour empilée par le CALL) restent à des décalages POSITIFS malgré tous les push qui suivent, puisque BP lui-même ne bouge plus. IP affiché = l'adresse de retour déjà empilée par le CALL qui a mené ici (équivalent exact de ce qu'un débogueur montrerait à un point d'arrêt juste après ce CALL). SP affiché = celui vu par l'appelant AVANT ce CALL (BP+4, simple calcul, jamais relu depuis la pile).
  - UART: tout d'un coup, format inspiré de DEBUG.COM (le débogueur DOS classique) - nouvelle macro uart_flag_bit (3 paramètres: masque, étiquette si bit=1, étiquette si bit=0) invoquée 8 fois pour décoder FLAGS en mnémoniques classiques (OV/NV DN/UP EI/DI NG/PL ZR/NZ AC/NA PE/PO CY/NC, ordre OF DF IF SF ZF AF PF CF) - le mnémonique "actif" (bit=1) coloré en jaune pour ressortir à l'oeil.
  - LCD: 14 valeurs à afficher, trop pour les 4x20 caractères disponibles d'un coup - PAGINE sur 2 écrans (Gauche/Droite pour basculer, comme edit_ram_action). Page 1: AX/BX/CX/DX/SI/DI/SP/BP. Page 2: CS/IP/DS/ES/SS/FL, puis ligne 4 = les 8 FLAGS décodés en UNE LETTRE chacun (O D I S Z A P C), MAJUSCULE si le bit est actif, minuscule sinon (+20h, motif standard ASCII maj->min) - complétée à exactement 20 caractères (5 espaces de remplissage) pour écraser tout résidu de la page précédente. Numéro de page vivant dans SI (jamais touché par gotoxy/print/lcd_tx_hex_word/lcd_data/ps2_get_char, tous le préservent - la valeur ORIGINALE de SI, elle, a déjà été affichée via UART et relue depuis la pile avant que SI ne serve de numéro de page).
  - Chaque ligne du LCD (page 1 ET 2) vérifiée pour NE PAS dépasser 20 caractères (leçon retenue du bug d'Edit RAM: étiquette d'adresse qui débordait et corrompait la ligne pairée) - ex. ligne1 page1: "AX=XXXX" (0-6) + "BX=XXXX" (9-15) + "1/2" (17-19) = exactement 20, aucun débordement.
  - Menu Dump memory renuméroté: "1) Dump memory / 2) Edit RAM / 3) Registres CPU / 9) Home menu".
  - Vérifié en détail via listing d'assemblage (nasm -l), octet par octet: tous les décalages [bp-N]/[bp+N] confirmés corrects (ex: "8B46F4" = mov ax,[bp-12]), séquence de restauration finale confirmée (pop di/si/dx/cx/bx/ax puis "add sp,10" pour libérer FLAGS/SS/ES/DS/CS SANS les repop-er dans un registre, puis pop bp, ret). make all/check/check-modules + build TEST_PS2 + build TEST_I2C_DUMP tous validés. Pas encore testé sur le matériel réel.
* Question: quelle touche pour changer de page LCD dans Registres CPU? Réponse: Flèche gauche OU droite (les deux basculent, peu importe la direction) - voir registers_dump_action, .toggle_page.
* Pour l'affichage des registres sur UART, afficher aussi les valeurs en binaire et afficher les flags sur une ligne individuelle. Réalisé:
  - lib/uart.asm: nouvelle procédure uart_tx_bin_word (affiche AX en binaire, 16 caractères '0'/'1', MSB en premier - même discipline de préservation de registres que uart_tx_hex_*).
  - solution-01.asm: nouvelle procédure print_reg_hex_bin_uart (affiche AX en hexa PUIS en binaire, séparés par 2 espaces - le libellé "AX=" etc. est affiché séparément par l'appelant via la macro "print", avant l'appel).
  - registers_dump_action (section UART) entièrement réorganisée: 2 registres par ligne (AX/BX, CX/DX, SI/DI, SP/BP, DS/ES, SS/CS, IP seul), chacun en hexa+binaire, au lieu de l'ancien format "tout sur 2 lignes, hexa seulement". FLAGS déplacé sur SA PROPRE ligne (après une ligne vide de séparation), avec hexa+binaire+mnémoniques (au lieu d'être accolé à la fin de la ligne IP/segments comme avant). Textes txt_reg_* simplifiés (retrait des espaces de tête qui géraient l'ancien alignement sur 1 ligne, remplacés par un nouveau séparateur explicite txt_reg_pair_sep entre les 2 registres d'une même ligne).
  - Vérifié via listing d'assemblage (nasm -l), octet par octet (uart_tx_bin_word, print_reg_hex_bin_uart). make all/check/check-modules + build TEST_PS2 + build TEST_I2C_DUMP tous validés. Pas encore testé sur le matériel réel.* Dans le menu Dump memory, ajouter une option qui permet d'éditer la RAM à partir du deuxième bloc de 64K (1000:0000) et d'exécuter, via la touche 'r', le code qui y a été saisi (routine se terminant par RET/RETF), affichant les registres sur l'UART après exécution. Remplacer l'option "9) Home menu" par un simple appui sur Échap (non affichée à l'écran). Réalisé - edit_run_action (option 4 du menu Dump memory):
  - Réutilise TOUT l'appareil de edit_ram_action (edit_ram_draw_grid/cell_ddram/place_cursor/write_current/scroll_to_cursor/move_left/right/up/down/advance) sans aucune modification: ces routines sont agnostiques du segment, elles ne touchent jamais à la "vraie" RAM, seulement au tampon EDIT_BUFFER_OFF partagé. Seules deux nouvelles routines, edit_run_load_buffer/edit_run_commit_buffer, sont des copies strictement identiques de edit_ram_load_buffer/commit_buffer sauf que le côté "RAM réelle" vise le segment 1000h (VAR_SEG) au lieu de 0000h.
  - Pas de saisie d'adresse (contrairement à Edit RAM): l'adresse de départ est TOUJOURS 0000h (donc 1000:0000), fixée directement dans EDIT_BASE_OFF - seule la taille est demandée (1-1024 octets, mêmes limites qu'Edit RAM via EDIT_MAX_SIZE), largement sous la zone réservée (0F800h-0FFFFh) et sous la pile active (SS=1000h), donc sans risque de chevauchement.
  - Touches: Échap annule (comme Edit RAM); Q/q enregistre le tampon dans la RAM réelle SANS exécuter; R/r enregistre PUIS exécute (edit_run_execute_and_show) et affiche les registres.
  - edit_run_execute_and_show: exécute le code injecté via un CALL FAR IMMÉDIAT ("call 1000h:0000h", opcode 9A encodé directement par NASM) - le code injecté DOIT se terminer par RETF (jamais un RET proche, qui laisserait CS empilé et planterait la carte au retour, puisqu'un CALL FAR empile IP ET CS). CALL/RETF ne modifient jamais un registre général ni FLAGS: immédiatement après le retour, chaque registre empilé (AVANT tout autre usage) reflète exactement ce que le code injecté a laissé - même technique de capture par trame de pile que registers_dump_action ("push bp"/"mov bp,sp" puis pushf/push ss/es/ds/cs/ax/bx/cx/dx/si/di, relecture via [bp±N]), mais avec un seul mot de décalage avant l'ancrage (pas de "CALL qui a mené ici" à comptabiliser ici, contrairement à registers_dump_action): SP tel que laissé par le code injecté = bp+2 (au lieu de bp+4). Affichage UNIQUEMENT sur l'UART (demande explicite - pas de LCD), même format hexa+binaire+FLAGS sur sa propre ligne que registers_dump_action (réutilise print_reg_hex_bin_uart/txt_reg_*/uart_flag_bit). IP non affiché (aucune signification utile ici).
  - Risque documenté (comme la commande "G" de DEBUG.COM): si le code injecté modifie SS sans le restaurer, l'affichage des registres qui suit ciblerait une pile invalide - inhérent à l'exécution de code arbitraire, non protégeable côté firmware.
  - Menu Dump memory: "9) Home menu" retiré (LCD ET UART) - Échap fait maintenant office de retour au menu principal sans être affiché à l'écran. Nouvelle option "4) Edit+Run RAM" affichée à sa place.
  - Vérifié en détail via listing d'assemblage (nasm -l), octet par octet: "call 1000h:0000h" confirmé encodé en CALL FAR immédiat (9A 0000 0010), tous les décalages [bp±N] de edit_run_execute_and_show confirmés corrects (ex: "8B46F4" = mov ax,[bp-12], "83C002" = add ax,2 pour SP), edit_run_load_buffer/commit_buffer confirmées identiques aux originales sauf ES=VAR_SEG au lieu de 0, dispatch .dump_4/.dump_esc confirmé. make all/check/check-modules + build TEST_PS2 + build TEST_I2C_DUMP tous validés. Pas encore testé sur le matériel réel.
* Pour Edit+Run RAM: 1) pouvoir appuyer sur 'r' PENDANT la saisie d'un octet (pas seulement entre deux cases); 2) éliminer la nécessité d'appuyer sur Entrée pour valider la saisie d'un octet; 3) ne plus demander le nombre d'octets à saisir, fixer à 255. Réalisé:
  - Diagnostic du point 1: ps2_edit_byte_value (lib/ps2.asm, PARTAGÉE avec edit_ram_action - inchangée) boucle INTERNEMENT sur ps2_get_char jusqu'à Entrée, touche par touche, sans jamais rendre la main à l'appelant avant - ce qui avalait silencieusement 'r'/'R' s'il était tapé APRÈS un premier chiffre (la boucle .wait_key extérieure d'edit_run_action, qui le reconnaît, elle, n'était jamais re-atteinte).
  - Nouvelle procédure edit_run_byte_value (solution-01.asm, DÉDIÉE à edit_run_action - ps2_edit_byte_value n'est pas touchée, edit_ram_action garde son comportement inchangé): même structure que ps2_edit_byte_value, avec deux ajouts - 'r'/'R' vérifiée EN PREMIER à chaque touche lue (retour immédiat via une 3e valeur de sortie DL=1, chiffre(s) partiel(s) ABANDONNÉS - rien n'est écrit pour la case en cours), et validation AUTOMATIQUE dès le 2e chiffre hexa (Entrée reste disponible pour valider un octet d'UN SEUL chiffre, mais n'est plus nécessaire pour un octet complet).
  - edit_run_action (.not_down): appelle edit_run_byte_value au lieu de ps2_edit_byte_value, teste DL=1 EN PREMIER (avant le test CF de "rien tapé") pour aiguiller vers .commit_and_run si 'r'/'R' a interrompu la saisie.
  - Point 3: suppression complète du prompt "Size:" (ps2_read_hex_editable, lcd_show, validation/rejet) - EDIT_SIZE_OFF fixé directement à EDIT_RUN_SIZE (255, nouvelle constante) en même temps que EDIT_BASE_OFF=0, sans aucune saisie: la grille s'affiche immédiatement après lcd_init. Le texte LCD "Run: 1000:0000" (devenu inutile, la grille prenant l'écran immédiatement) et son étiquette lcd_txt_run_addr ont été retirés (code mort).
  - Vérifié en détail via listing d'assemblage (nasm -l), octet par octet: la nouvelle procédure edit_run_byte_value confirmée byte-à-byte fidèle à ps2_edit_byte_value sauf les deux ajouts documentés, ordre des tests DL=1 puis CF dans edit_run_action confirmé correct, "mov word [es:di], EDIT_RUN_SIZE" confirmé écrire 255 (FF 00). make all/check/check-modules + build TEST_PS2 + build TEST_I2C_DUMP tous validés. Pas encore testé sur le matériel réel.
* Bug rapporté sur le matériel réel: dans Edit+Run RAM, en tapant "B8" à l'adresse de départ, le 'B' s'affiche mais dès que '8' est tapé, l'écran se réinitialise et l'octet reste à 00. Diagnostic: dans edit_run_action (.not_down), la séquence "call edit_run_byte_value / cmp dl,1 / je .commit_and_run / jc .redraw" testait CF (jc) APRÈS avoir exécuté "cmp dl,1" - qui ÉCRASE le carry flag que edit_run_byte_value venait de positionner comme signal de sortie ("CF=0" = valeur prête). Puisque DL=0 dans ce cas (valeur composée avec succès), "cmp dl,1" calcule 0-1 (emprunt), mettant CF=1 par accident - donc "jc .redraw" se déclenchait à tort, jetant systématiquement la valeur composée dès le 2e chiffre auto-validé, sans jamais écrire le tampon. Corrigé: le test "jc .redraw" est déplacé AVANT "cmp dl,1" (l'ordre inverse ne pose pas ce problème, puisqu'on n'a plus besoin du CF original une fois qu'on a décidé de ne PAS aller à .redraw). Vérifié via listing d'assemblage (nasm -l): jc .redraw confirmé immédiatement après le call, avant cmp dl,1. make all/check/check-modules + build TEST_PS2 + build TEST_I2C_DUMP tous validés.
* Ajout demandé: afficher l'adresse en tête de chaque ligne de la grille d'édition (Edit RAM ET Edit+Run RAM, code de rendu partagé) pour ne pas se perdre en défilant. Réalisé - EDIT_COLS réduit de 6 à 5 (nouvelle constante EDIT_ADDR_LABEL_WIDTH=5) pour degager EXACTEMENT la place d'une étiquette "SSSS:" (5 caractères, sans espace) en tête de chaque ligne LCD sans dépasser les 20 caractères disponibles (5 + 5 colonnes × 3 caractères "XX " = 20 EXACTEMENT) - reprend la leçon du bug précédent (ancien format 6 colonnes + étiquette = 24 caractères, débordait dans la ligne DDRAM pairée):
  - edit_ram_draw_grid: le calcul de décalage de ligne logique utilise maintenant EDIT_COLS (au lieu du littéral 6); l'adresse réelle de chaque ligne (déjà calculée pour l'UART) est maintenant AUSSI affichée sur le LCD (lcd_tx_hex_word + ':' via lcd_data) AVANT l'affichage UART - AX préservé entre les deux via push/pop, puisque les deux détruisent AX.
  - edit_ram_cell_ddram: le diviseur (ligne logique/colonne) utilise EDIT_COLS au lieu de 6; le calcul final de l'adresse DDRAM ajoute maintenant EDIT_ADDR_LABEL_WIDTH (5) en plus du décalage de colonne, pour pointer la case après l'étiquette.
  - Toutes les autres routines partagées (place_cursor, write_current, move_left/right/up/down, advance, ps2_edit_byte_value, edit_run_byte_value) restent INCHANGÉES - elles utilisent déjà EDIT_COLS symboliquement ou l'adresse DDRAM absolue (AH) sans jamais recalculer la largeur elles-mêmes.
  - Vérifié en détail via listing d'assemblage (nasm -l), octet par octet: EDIT_COLS=5 confirmé partout (B90500/BA0500 = mov cx/dx,5), "add al, EDIT_ADDR_LABEL_WIDTH" confirmé (0405 = add al,5), séquence push ax/lcd_tx_hex_word/lcd_data(':')/pop ax/uart_tx_hex_word confirmée avant le calcul des colonnes valides. make all/check/check-modules + build TEST_PS2 + build TEST_I2C_DUMP tous validés. Pas encore testé sur le matériel réel.
* Bug rapporté sur le matériel réel: après le correctif précédent (édition confirmée fonctionnelle), la touche 'R'/'r' pour exécuter (edit_run_action) ne faisait toujours rien. Diagnostic: ps2_keymap (lib/ps2.asm) est une LISTE BLANCHE de scan codes reconnus (chiffres, A-F, Q, Entrée, Retour arrière, Échap) - toute touche absente de cette table est silencieusement ignorée par ps2_get_char (ps2_scancode_to_char retourne CF=1, .loop reboucle) AVANT même d'atteindre le code qui teste 'r'/'R' dans solution-01.asm. La touche R (scan code Set 2 = 02Dh) n'y avait jamais été ajoutée, en dépit de toutes les vérifications "cmp al,'r'/'R'" ajoutées côté solution-01.asm - celles-ci ne pouvaient donc jamais se déclencher. Corrigé: ajout de "db 02Dh, 'R'" à ps2_keymap (comme 'Q'). Vérifié via listing d'assemblage (nasm -l): "2D 52" confirmé dans la table. make all/check/check-modules + build TEST_PS2 + build TEST_I2C_DUMP tous validés.
* A l'entree dans "4) Edit+Run RAM", initialiser 1000:0000 avec B8 34 12 CB (mov ax,1234h / retf) - UNIQUEMENT a l'appel de l'option, pas a chaque retour de RETF. Realise: nouvelle table edit_run_default_code (4 octets, ROM) copiee dans la RAM reelle a 1000:0000 tout au debut d'edit_run_action (avant edit_run_load_buffer, pour que la grille affiche ces octets des l'entree) - place explicitement AVANT .redraw et jamais rejouee par le chemin .commit_and_run (qui saute directement a .redraw apres l'execution, sans repasser par ce bloc), donc les modifications de l'utilisateur survivent a chaque 'r'. Vérifié via listing d'assemblage (nasm -l): boucle de 4 iterations (edit_run_default_code_len=4) confirmee, octets B8 34 12 CB confirmes en ROM. make all/check/check-modules + build TEST_PS2 + build TEST_I2C_DUMP tous valides.
* Remplacer le texte "Dump memory" par "Memory functions" et supprimer l'option "Edit RAM" du menu principal (deja disponible via l'option "2" du sous-menu). Realise:
  - Menu principal: "2) Dump memory" -> "2) Memory functions" (UART+LCD); "4) Edit RAM" retiree completement (texte ET dispatch .main_4) - le menu principal n'offre plus que 3 options (1,2,3), toute autre touche redessine le menu.
  - Sous-menu (banniere): "--- Menu Dump memory ---" -> "--- Menu Memory functions ---" - son PREMIER item reste "1) Dump memory" (nom de l'action specifique, distinct du nom du sous-menu qui l'englobe).
  - Tous les commentaires de code faisant reference au "sous-menu Dump memory" mis a jour en "sous-menu Memory functions" pour rester coherents (registers_dump_action, edit_run_action, dump_memory_action, etc.) - les commentaires parlant de l'ACTION "Dump memory" elle-meme (pas du sous-menu) sont restes inchanges.
  - Vérifié via listing d'assemblage (nasm -l): dispatch .main_4 confirme disparu, .main_3 redessine correctement le menu sur toute touche non '3'. make all/check/check-modules + build TEST_PS2 + build TEST_I2C_DUMP tous valides.
* Bug rapporte: en testant "add ax,2 / retf" a repetition (touche R), AX reste toujours a la meme valeur au lieu de s'incrementer. Diagnostic (explique a l'utilisateur, pas un bug d'assemblage): AX/BX/CX/DX/SI/DI ne sont PAS preserves entre deux appuis sur 'r' - le code de menu/clavier qui s'execute entre-temps (ps2_get_char pour lire 'r' lui-meme, edit_ram_draw_grid, etc.) les ecrase, donc chaque execution repart d'une valeur fixe (deterministe, pas la precedente). Ajout demande et confirme par l'utilisateur: rendre ces 6 registres PERSISTANTS d'une execution a l'autre. Realise:
  - include/hardware.inc: 6 nouveaux mots reserves (RUN_REG_AX/BX/CX/DX/SI/DI_OFF, 0FC1Bh-0FC26h) dans la zone VAR_SEG deja reservee.
  - edit_run_action: remet ces 6 mots a 0 UNE SEULE FOIS, a l'entree dans une NOUVELLE session d'edition (juste apres EDIT_BASE_OFF/EDIT_SIZE_OFF) - pas a chaque execution.
  - edit_run_execute_and_show: restaure AX/BX/CX/DX/SI/DI depuis RUN_REG_*_OFF JUSTE AVANT "call 1000h:0000h" (BP libre a ce moment, [bp] adresse SS=VAR_SEG par defaut), puis les RE-persiste JUSTE APRES le retour (dans les push AX..DI, avant tout usage d'AX comme registre de travail d'affichage) via "[ss:bx]" (prefixe de segment explicite: BX seul adresse DS par defaut sur le 8086, pas SS - le prefixe force SS sans sacrifier BP, qui reste l'ancre de la trame de pile pour le reste de la routine). BX lui-meme est repersiste en dernier, relu depuis la pile ([bp-14]) puisqu'il vient de servir de pointeur pour les 5 autres.
  - Vérifié en détail via listing d'assemblage (nasm -l), octet par octet: prefixe 36h (override SS) confirme sur chaque "mov [ss:bx],reg", tous les offsets RUN_REG_*_OFF confirmes corrects, "mov ax,[bp-14]" confirme pour relire BX avant sa propre persistance. make all/check/check-modules + build TEST_PS2 + build TEST_I2C_DUMP tous valides. Pas encore testé sur le matériel réel.
* Avant d'implémenter le 8259 (discussion architecture: 8259 réel + Arduino pour UART/clavier, dans l'optique d'un vrai MS-DOS), déplacer TOUT l'affichage LCD du parallèle vers le LCD I2C - libère les broches PA1-PA4/PA6 du 8255 pour une réaffectation matérielle. Réalisé:
  - lib/lcd_i2c.asm: ajout de i2c_lcd_tx_hex_word (def_tx_hex_word, manquait) et i2c_lcd_tx_dec3 (copie exacte de lcd_tx_dec3/lib/lcd.asm, seule i2c_lcd_data change) - complète la bibliothèque I2C pour qu'elle offre TOUS les equivalents utilisés par solution-01.asm.
  - Renommage global (sed, protégé contre le double-préfixage des "i2c_lcd_" déjà présents): tous les appels directs lcd_init/command/data/print/tx_dec3/tx_hex_word/tx_hex_byte/tx_hex_nibble/goto/show -> i2c_lcd_*, et tous les usages ", LCD" (device des macros gotoxy/print) -> ", LCDI2C" (~92 appels directs + 68 usages macro) - vérifié précisément (grep) qu'aucun des deux motifs n'apparaissait dans un commentaire/texte français avant de lancer le remplacement, et qu'aucun double-préfixe (i2c_i2c_lcd_) n'a été introduit après.
  - dump_line: l'ancien format LCD parallèle (3 lignes: adresse/aperçu 7 octets/numéro de ligne) est retiré; le format I2C détaillé (16 octets complets, 4/ligne, ASCII sur les lignes 1/3), auparavant conditionnel derrière TEST_I2C_DUMP (test de stress du LCD I2C), devient l'affichage PERMANENT et UNIQUE - la directive TEST_I2C_DUMP (et ses %ifdef/%endif dans i2c_dump_hex4/i2c_dump_hex_only_line/i2c_dump_hex_ascii8_line) est retirée entièrement. Textes devenus inutiles (lcd_txt_dump_pad, lcd_txt_ligne_prefix/suffix) supprimés.
  - Écran de démarrage: le renommage créait DEUX blocs consécutifs écrivant sur le MÊME LCD I2C (l'un préexistant, version+paramètres UART; l'autre, ex-parallèle, splash officiel avec tirets) - le second écrasait immédiatement le premier avant même le délai d'affichage, rendant le premier bloc invisible depuis toujours après le renommage. Le premier bloc (et sa donnée i2c_txt_uart_params, devenue inutilisée) a été retiré - AUCUN changement de comportement visible (son contenu n'était déjà jamais vu).
  - README.md mis à jour (intro, Menu interactif, Dump memory, section TEST_I2C_DUMP réécrite comme comportement permanent, activation TEST_PS2 réécrite sans référencer TEST_I2C_DUMP comme exemple).
  - lib/lcd.asm N'EST PAS supprimé: ses délais (lcd_powerup_delay/lcd_delay/lcd_delay_long) restent réutilisés par lib/lcd_i2c.asm. Le dispatch générique d'int10h_handler (BH=1 pour LCD parallèle) reste aussi en place (infrastructure inoffensive, plus jamais invoquée avec BH=1 par le firmware).
  - Vérifié en détail via listing d'assemblage (nasm -l) + relecture ciblée (edit_ram_draw_grid, registers_dump_action, edit_run_byte_value, écran de démarrage) confirmant l'absence totale d'appel lcd_* parallèle résiduel. make all/check/check-modules + build TEST_PS2 (TEST_I2C_DUMP n'existe plus) tous validés. Pas encore testé sur le matériel réel (changement de grande ampleur, ~160 sites modifiés).
* Le 8259 est cablé (CS# via IO.A6./A7, ports 20h/21h comme le PC/XT reel) et un interrupteur (bouton-poussoir) est branché sur IR0. Première interruption MATÉRIELLE réelle du projet (jusqu'ici, seulement des interruptions LOGICIELLES "esprit BIOS" - INT 10h/16h, qui n'ont jamais eu besoin du 8259). Réalisé:
  - include/hardware.inc: PIC_CMD/PIC_DATA (20h/21h, même style que PORTA/PORTB/PORTC/PIO pour le 8255).
  - solution-01.asm: nouvelle procédure init_8259 - séquence ICW standard PC/XT (ICW1=13h: déclenchement par front, 8259 unique donc ICW3 omise; ICW2=08h: IR0-IR7 -> INT 08h-0Fh; ICW4=01h: mode 8086/8088, EOI MANUEL - pas d'auto-EOI, plus fiable si plusieurs IRQ en attente), puis OCW1=FEh (démasque IR0 SEULEMENT - IR1-IR7 pas encore câblées, potentiellement flottantes). Installe aussi irq0_test_handler au vecteur INT 08h (IVT), même motif que setup_bios_interrupts pour INT 10h/16h.
  - Nouvelle procédure irq0_test_handler: affiche un message UART (appel DIRECT à uart_tx_string, comme int_not_implemented - indépendant de toute cause potentielle de dysfonctionnement), envoie un EOI NON SPÉCIFIQUE (OCW2=20h au port de commande - obligatoire en EOI manuel, sinon le 8259 ne représente plus jamais IR0 ni les priorités inférieures), puis IRET (restaure FLAGS/IF automatiquement, pas de STI explicite nécessaire). Pas de anti-rebond volontairement: plusieurs interruptions par appui sont attendues et confirment même que le mécanisme réagit à chaque front.
  - start:: appelle init_8259 juste après setup_bios_interrupts, PUIS "sti" explicite (première fois qu'IF compte réellement pour ce projet) - une fois le 8259 configuré ET le vecteur installé.
  - Limitation connue documentée (pas encore résolue): les protocoles bit-bangés existants (lecture PS/2, UART logiciel, I2C LCD) sont sensibles au timing - si IR0 se déclenche PENDANT une de ces sections critiques, l'ISR pourrait perturber l'échantillonnage. Acceptable pour ce premier test (bouton pressé délibérément, rarement en même temps qu'une opération bit-bangée) - à reconsidérer sérieusement une fois l'UART/clavier réellement déplacés vers l'Arduino.
  - Vérifié en détail via listing d'assemblage (nasm -l), octet par octet: ICW1=13h/ICW2=08h/ICW4=01h/OCW1=FEh confirmés (B013/B008/B001/B0FE avant chaque "out"), vecteur INT 08h confirmé pointer vers irq0_test_handler, EOI (B020/E620) et IRET (CF) confirmés en fin de gestionnaire. make all/check/check-modules + build TEST_PS2 tous validés. Pas encore testé sur le matériel réel (fonctionnalité neuve et delicate - première vraie interruption matérielle).
* Confirmé sur le matériel réel: le message "*** IRQ0 declenchee (bouton-poussoir, 8259) ***" s'affiche correctement sur l'UART à l'appui du bouton-poussoir - première interruption MATÉRIELLE réelle du projet validée de bout en bout (décodage CS# du 8259, séquence ICW1-4, vecteur IR0->INT 08h installé dans l'IVT, IF activé au bon moment, EOI permettant au 8259 de re-signaler IR0 sans se bloquer).
* Bug rapporté sur le matériel réel: après le passage complet du LCD au I2C et l'ajout du 8259, toutes les fonctions du menu sont OK SAUF Dump memory - impossible de saisir une adresse complète (et donc impossible de voir le contenu de l'IVT). Diagnostic: le renommage global lcd_*->i2c_lcd_* (voir plus haut, migration LCD parallele->I2C) n'avait porté que sur solution-01.asm - lib/ps2.asm avait été OUBLIÉ. Ses deux routines de saisie clavier avec echo LCD, ps2_read_hex_editable (utilisée par dump_memory_action ET par le prompt adresse/taille de edit_ram_action/edit_run_action) et ps2_edit_byte_value (edit_ram_action, saisie d'un octet), appelaient donc toujours lcd_tx_hex_nibble/lcd_command/lcd_data - les fonctions PARALLÈLES. Comme PA0 est partagé entre D4 (LCD parallèle) ET SCL (LCD I2C), chaque frappe déclenchait un cycle du protocole PARALLÈLE sur une broche que le protocole I2C considère comme son horloge - de quoi dérégler le bus I2C et corrompre l'affichage à chaque caractère tapé, donnant l'impression que la saisie ne fonctionne pas. Corrigé: lib/ps2.asm inclut maintenant lib/lcd_i2c.asm (au lieu de lib/lcd.asm directement - toujours inclus transitivement pour les délais) et les 8 appels concernés (lcd_tx_hex_nibble x2, lcd_command x4, lcd_data x2) sont renommés vers leurs équivalents i2c_lcd_*. En profité pour mettre à jour l'en-tête du fichier (mention périmée "le projet n'utilise pas encore les interruptions" - documente maintenant le risque théorique d'un IRQ survenant pendant une trame PS/2, laissé pour plus tard avec le passage réel de l'UART/clavier vers l'Arduino). Vérifié via listing d'assemblage (nasm -l, solution-01.asm ET lib/ps2.asm séparément): tous les appels confirmés i2c_lcd_*. make all/check/check-modules + build TEST_PS2 tous validés. Pas encore reconfirmé sur le matériel réel.
* Ajouter au menu une option affichant le contenu de l'IVT, avec description du handler (ex: "INT 10h -> C000:1234 : int10h_handler -> Gestion de l'affichage"), les vecteurs implémentés en vert. Réalisé - ivt_dump_action (option "5) IVT" du sous-menu Memory functions, non affichée sur le LCD - seulement 4 lignes disponibles, meme convention que l'ancien "9) Home menu"):
  - UART: TOUTE la table (256 vecteurs) d'un coup, une seule fois à l'entrée - "INT xxh -> SSSS:OOOO : nom -> description" par ligne. Identification implémenté/pas: compare l'OFFSET lu dans chaque entrée de l'IVT (le segment n'est pas vérifié séparément - tous les gestionnaires vivent dans la même ROM=CS) aux adresses des 3 gestionnaires réels connus (int10h_handler/int16h_handler/irq0_test_handler, comparaison directe contre l'adresse assemblée de chaque label) - implémentés affichés en VERT, tout le reste (en pratique toujours int_not_implemented) sans couleur.
  - LCD I2C: grille DÉFILANTE (256 vecteurs, 4 visibles à la fois), "xxh  SSSS:OOOO" par ligne (14 caractères) - un seul vecteur par ligne (pas de colonnes, vue seule sans édition) - même principe de fenêtre défilante que edit_ram_draw_grid (nouvelle IVT_WINDOW_OFF, include/hardware.inc), fleches HAUT/BAS pour défiler d'un vecteur, Echap pour revenir au menu.
  - Registres CX (segment)/DX (offset) tenus à travers les appels i2c_lcd_goto/i2c_lcd_tx_hex_byte/i2c_lcd_data/i2c_lcd_tx_hex_word - vérifié au préalable (lecture de i2c_lcd_send_byte) qu'aucun ne touche CX/DX (seuls AX/BX détruits, comme la convention établie ailleurs dans le projet).
  - Vérifié en détail via listing d'assemblage (nasm -l), octet par octet: les 3 comparaisons "cmp dx,int10h_handler/int16h_handler/irq0_test_handler" confirmées cibler les bonnes adresses assemblées, "cmp bx,256"/"cmp ax,252" confirmés corrects pour les bornes de la table/fenêtre. make all/check/check-modules + build TEST_PS2 tous validés. Pas encore testé sur le matériel réel.
* Deux ajustements demandés: 1) l'option "5) IVT" n'était pas visible sur le LCD (seulement 4 lignes, "5" restait un raccourci non affiché comme l'ancien "9) Home menu") - revoir l'organisation du sous-menu; 2) limiter l'affichage de l'IVT aux 40 premières entrées. Réalisés:
  - .dump_menu (Memory functions): PAGINE sur 2 écrans LCD depuis l'ajout de "5) IVT" - Gauche/Droite pour basculer, réutilise DIRECTEMENT txt_lcd_page1/page2 (déjà génériques, utilisées par registers_dump_action). Page 1 = options 1-4 (inchangée), page 2 = option 5 seule. SI = page courante, remise à 0 à CHAQUE (ré)entrée dans .dump_menu (pas de persistance entre deux passages - plus simple/prévisible qu'un état qui "survivrait" à une action). L'UART affiche TOUJOURS les 5 options d'un coup, imprimé UNE SEULE FOIS à l'entrée (pas à chaque bascule de page LCD, pour ne pas spammer). Touche non reconnue: reste sur la même page (redessine via .dump_redraw) au lieu de tout réinitialiser comme avant.
  - ivt_dump_action: nouvelle constante IVT_DUMP_COUNT=40 (et IVT_WINDOW_MAX=36=40-4, dernière fenêtre LCD valide) remplacent les bornes 256/252 codées en dur - limite volontaire aux vecteurs 00h-27h (les seuls avec un intérêt dans ce projet: 00h-1Fh réservés Intel, 08h IR0/8259, 10h/16h "esprit BIOS" - le reste jusqu'à FFh n'étant que des répétitions de int_not_implemented). Bannière UART mise à jour ("INT 00h-27h").
  - Vérifié en détail via listing d'assemblage (nasm -l): pagination .dump_menu confirmée octet par octet (page1/page2/toggle_page/wait_key), "cmp bx,IVT_DUMP_COUNT"=83FB28 (40) et "cmp ax,IVT_WINDOW_MAX"=83F824 (36) confirmés. make all/check/check-modules + build TEST_PS2 tous validés. Pas encore testé sur le matériel réel.
* Pendant le dump UART de ivt_dump_action (40 lignes), le LCD reste vide (i2c_lcd_init efface l'ecran avant le dump UART, la grille reelle ne s'affiche qu'apres, via .redraw) - risque de laisser croire que la carte est figee. Ajouté: message "Chargement IVT..." affiché sur le LCD (ligne 2) dès l'entrée dans l'action, effacé automatiquement par le premier .redraw une fois le dump UART terminé. make all/check/check-modules + build TEST_PS2 tous validés.
* Passons a la version avec Arduino UNO R3 (UART/clavier). Decisions prises pour demarrer: interface de donnees = nouveau port 8255 dedie (a implementer plus tard); lignes IRQ = IRQ1 clavier + IRQ4 UART (convention PC/XT, coherent avec l'objectif MS-DOS); premiere etape = test de branchement minimal (comme IRQ0), AVANT le vrai protocole de donnees. Realise:
  - init_8259: demasque maintenant IR0 (inchange)/IR1/IR4 (PIC_MASK_TEST=0xEC, remplace PIC_MASK_ONLY_IR0) - IR2/IR3/IR5/IR6/IR7 restent masquees (non cablees). Installe irq1_test_handler (INT 09h) et irq4_test_handler (INT 0Ch), memes principes qu'irq0_test_handler (message UART direct, EOI non specifique, IRET, pas d'anti-rebond volontairement).
  - ivt_dump_action: le tableau de gestionnaires connus (affiches en vert) inclut maintenant irq1_test_handler/irq4_test_handler en plus des 3 precedents.
  - Nouveau croquis Arduino (arduino/irq_test/irq_test.ino, racine du depot, hors Solution-01): 2 boutons-poussoirs cotes Arduino (anti-rebond logiciel simple) pulsent chacun une broche de sortie reliee a IR1/IR4 du 8259 - teste la chaine complete bouton->Arduino->8259->8088 SANS encore le port de donnees 8255 (qui viendra avec le vrai protocole clavier/UART). Hypothese de polarite documentee dans le croquis (idle bas, impulsion haute, a ajuster si le cablage reel de IR0 est different) - PAS verifiable par moi (pas d'arduino-cli disponible sur ce poste pour compiler).
  - Vérifié en détail via listing d'assemblage (nasm -l), octet par octet: PIC_MASK_TEST=0xEC confirme, vecteurs INT 09h/0Ch installes aux bonnes adresses (irq1/irq4_test_handler), chaine de comparaison ivt_dump_action mise a jour et verifiee. make all/check/check-modules + build TEST_PS2 tous valides (cote 8088). Croquis Arduino NON verifie (pas d'outil de compilation disponible) - a tester par l'utilisateur, tant au niveau compilation Arduino IDE que cablage/polarite reelle.
* arduino-cli installe (sous WSL, via snap - /snap/bin/arduino-cli, version 1.3.0) - le croquis arduino/irq_test/irq_test.ino a ete compile avec succes pour l'Arduino Uno (arduino:avr:uno, coeur AVR 1.8.8 installe): 2672 octets programme (8%), 218 octets memoire globale (10%). Aucune erreur de compilation - reste a verifier le cablage/polarite reel sur le materiel.
* Bug rapporté sur le matériel réel: les messages IRQ1/IRQ4 apparaissent en continu sans appuyer sur les boutons - ceux-ci sont câblés en pull-down externe vers GND (repos=BAS, appui=HAUT), mais le croquis irq_test.ino configurait les broches en INPUT_PULLUP (pull-up interne Arduino) et vérifiait "== LOW" pour détecter un appui - l'inverse du câblage réel. Le pull-up interne se battait avec le pull-down externe, bloquant la broche à un niveau erroné (lu comme "bouton pressé en continu"). Corrigé: pinMode(...) en INPUT simple (pas INPUT_PULLUP - le pull-down est déjà externe), détection d'appui via "== HIGH" au lieu de "== LOW". Polarité des lignes IRn elle-même (repos bas, impulsion haute) CONFIRMÉE correcte sur le matériel réel - aucun changement de ce côté. Recompilé avec succès (arduino-cli, arduino:avr:uno) - à retester sur le matériel réel.
* Objectif exprimé: reproduire l'architecture clavier/UART de l'IBM PC/XT avec l'Arduino, en réaffectant le 8255 existant (pas de second 8255). Décisions prises: Port A = ENTRÉE (octet Arduino->8088, clavier OU UART reçu, IR1/IR4 selon la source choisie par l'Arduino lui-même - pas de 8255 mode 1: l'Arduino sait déjà quelle ligne pulser); Port B = SORTIE (LCD I2C, déplacé du Port A + PB_RX_ACK/PB_TX_STROBE, poignée de main logicielle); Port C = SORTIE (octet 8088->Arduino à transmettre, remplace le chenillard). Aucun contrôle de flux dans le sens 8088->Arduino pour l'instant (même limitation que l'ancien UART bit-bangé). Réalisé - changement majeur touchant le cœur du firmware:
  - include/hardware.inc: MASQUE_PIO inversé (10010000b: Port A entrée, B/C sortie). Nouveaux PB_SCL/PB_SDA/PB_RX_ACK/PB_TX_STROBE. Nouvelles zones VAR_SEG: PORTB_SHADOW_OFF (copie fantôme Port B) + deux tampons circulaires 16 octets (PS2_RX_*/UART_RX_*, tête=queue->vide).
  - lib/common.asm: nouvelle portb_write (même principe que porta_write) - PROTÉGÉE par pushf/cli/.../popf (pas juste cli/sti): sa séquence lecture-modification-écriture n'est PAS atomique face à une IRQ qui l'interromprait pile entre lecture et écriture (le Port B est maintenant partagé entre la boucle principale - I2C, TX strobe - ET les ISR - RX ack), risque de "lost update" classique. popf (pas sti inconditionnel) pour ne jamais réactiver IF prématurément si appelée depuis l'intérieur d'une ISR. Nouvelle portb_pulse (met un bit à 1 puis 0).
  - lib/lcd_i2c.asm: SDA/SCL déplacés du Port A (PA5/PA0) au Port B (PB_SDA/PB_SCL) - la lecture matérielle directe "IN AL,PORTx" (optimisation de performance déjà en place) reste utilisée, mais i2c_lcd_send_byte encadre maintenant TOUTE la transaction (START..STOP) d'un cli/sti: sans ça, une IRQ1/IRQ4 pourrait s'intercaler entre deux écritures Port B de la transaction et faire perdre/décaler des bits SCL/SDA en vol.
  - lib/uart.asm: REMPLACE entièrement (pas juste déplacé) - uart_tx_byte pose l'octet sur le Port C puis pulse PB_TX_STROBE (uart_tx_pulse_delay, PLACEHOLDER non calibré) au lieu du bit-bang PA7 9600 8N1 (UART_MASK/UART_BIT_COUNT retirés, obsolètes). Nouvelle capacité RX: uart_rx_push (appelée par irq4_uart_rx_handler)/uart_rx_available/uart_rx_byte (tampon circulaire, rien ne la consomme encore ailleurs).
  - lib/ps2.asm: ps2_wait_falling_edge/le bit-bang CLOCK/DATA du Port B sont RETIRÉS - ps2_read_byte garde EXACTEMENT le même contrat (AL=octet, CF=erreur, toujours 0 maintenant) mais pioche dans PS2_RX_BUF_OFF (rempli par irq1_ps2_handler) au lieu de bit-banger - ps2_get_char et tout ce qui en dépend (ps2_read_hex_editable, ps2_edit_byte_value, etc.) INCHANGÉS. Nouvelle ps2_rx_available (non bloquante) remplace les "IN AL,PORTB/TEST AL,PS2_CLOCK" de dump_memory_action et int16h_handler (vérification Échap/AH=01h non bloquante - Port B n'est plus le clavier direct).
  - solution-01.asm: irq1_test_handler/irq4_test_handler renommés et transformés en irq1_ps2_handler/irq4_uart_rx_handler (lisent Port A, enfilent dans le tampon, pulsent PB_RX_ACK, EOI, IRET - PLUS de message UART de test: appeler uart_tx_string depuis l'ISR risquerait de corrompre une transmission Port C déjà en cours ailleurs). BX explicitement sauvegardé/restauré dans ces ISR (utilisé directement pour PB_RX_ACK, pas via un appel auto-préservant). init_8259 installe les 3 vecteurs réels. ivt_dump_action reconnaît les 2 nouveaux gestionnaires (verts). Retiré: effet1/clear_8255A/proc1/delay2 (chenillard, incompatible avec le nouvel usage du Port C) et l'option "3) LED Show on PC" du menu principal (2 options restantes). Retiré aussi l'init au démarrage de PORTA_SHADOW_OFF/UART_MASK (Port A n'est plus piloté par le 8088).
  - Bug trouvé et corrigé AVANT tout essai (make all): deux symboles indéfinis (UART_MASK, PS2_CLOCK) oubliés dans du code non touché directement par le renommage (init au démarrage, dump_memory_action, int16h_handler) - causaient une cascade de ~150 avertissements "label changed during code generation" (NASM tente plusieurs passes avec une valeur indéfinie instable) avant même d'atteindre l'erreur reelle. Corrigés en adaptant ce code au nouveau mécanisme (ps2_rx_available notamment, nouvelle fonction non bloquante).
  - Vérifié en détail via listing d'assemblage (nasm -l): irq1_ps2_handler/irq4_uart_rx_handler confirmés byte-à-byte (E480=IN AL,PORTA; B304=PB_RX_ACK), portb_write confirmée avec pushf(9C)/cli(FA)/.../popf(9D), i2c_lcd_send_byte confirmée avec cli(FA)/.../sti(FB) autour de toute la transaction, i2c_start/stop/write_byte confirmés utiliser PORTB (E481/E681) au lieu de PORTA. make all/check/check-modules + build TEST_PS2 tous validés. AUCUN test sur le matériel réel pour l'instant (changement le plus large et le plus risqué du projet à ce jour - touche le clavier, l'UART, le LCD I2C ET la logique 8259 simultanément) - le câblage matériel (Arduino réel décodant PS/2 + relayant son UART, protocole exact des octets envoyés) reste aussi à faire/valider du côté Arduino, qui n'implémente pas encore ce protocole (le croquis irq_test.ino ne fait toujours QUE le test de branchement IR1/IR4 brut).
* Nouvelle simplification demandée: le décodage I2C passera par l'Arduino (pas par le 8255) - le 8255 se limite à donner à l'Arduino l'octet clavier (Port A) ainsi qu'un canal générique de sortie (Port C) que l'Arduino relaie soit à l'UART matériel, soit au LCD via SON PROPRE bus I2C matériel (ex: broches A4/A5 câblées directement au module LCD, hors 8255). Décisions prises pour distinguer les 2 usages du Port C: deux bits de strobe séparés (PB_LCD_STROBE pour un octet LCD, PB_TX_STROBE pour un octet UART, inchangé) plutôt qu'un octet de type devant chaque transaction; le UART RX (IR4) reste comme avant, partagé avec le clavier (IR1) sur le Port A. Réalisé:
  - include/hardware.inc: PB_SCL/PB_SDA renommés/repositionnés en PB_LCD_STROBE (bit0, impulsion "octet LCD prêt sur le Port C")/PB_LCD_RS (bit1, niveau "commande ou donnée", positionné AVANT le strobe) - mêmes valeurs de bits qu'avant (0000_0001b/0000_0010b), seule leur SÉMANTIQUE change (ce ne sont plus des lignes I2C physiques). PB_RX_ACK/PB_TX_STROBE inchangés (bits 2/3). En-têtes de MASQUE_PIO et du bloc Port B réécrits.
  - lib/lcd_i2c.asm: RÉÉCRIT EN GRANDE PARTIE - tout le bit-bang I2C (i2c_start/i2c_stop/i2c_write_byte/i2c_lcd_strobe/i2c_delay/I2C_SDA/I2C_SCL/I2C_MASK/I2C_BASE_MASK/I2C_LCD_ADDR/I2C_LCD_RW/I2C_LCD_EN/I2C_LCD_BL) est RETIRÉ - i2c_lcd_send_byte se limite maintenant à poser l'octet sur le Port C, positionner PB_LCD_RS (0=commande/1=donnée) puis pulser PB_LCD_STROBE (3 écritures de port au lieu d'une transaction I2C complète de plusieurs centaines de µs) - AUCUN cli/sti requis (uart_tx_byte et i2c_lcd_send_byte sont tous deux du code de premier plan, jamais appelés depuis une ISR, donc jamais imbriqués). i2c_lcd_init n'exécute plus la séquence de démarrage 4 bits du HD44780 (déplacée dans le setup() de l'Arduino, qui possède maintenant tout le protocole PCF8574/I2C via une bibliothèque standard) - se contente de renvoyer Function Set/Display ON/Entry Mode/Clear par le nouveau canal, au cas où l'Arduino voudrait resynchroniser son état. API PUBLIQUE (i2c_lcd_command/i2c_lcd_data/i2c_lcd_print/i2c_lcd_tx_hex_*/i2c_lcd_tx_dec3/i2c_lcd_init) INCHANGÉE - aucun des ~90 sites d'appel dans solution-01.asm n'a eu besoin d'être modifié.
  - lib/common.asm: commentaire de portb_write/portb_pulse mis à jour (ne mentionne plus SCL/SDA).
  - Vérifié via listing d'assemblage (nasm -l): i2c_lcd_send_byte confirmée byte-à-byte (F6C301=test bl,I2C_LCD_RS; B002/B302=PB_LCD_RS; E682=OUT PORTC; B301=PB_LCD_STROBE). make all/check/check-modules + build TEST_PS2 tous validés. Pas encore testé sur le matériel réel - le croquis Arduino réel (décodage PS/2, relais UART matériel, pilotage LCD via I2C natif, protocole Port A/B/C complet) reste entièrement à écrire (irq_test.ino ne fait toujours que le test de branchement IR1/IR4 brut). Câblage à revoir en conséquence: le LCD I2C n'a plus besoin de passer par le 8255 (2 broches Port B libérées de leur ancien rôle SCL/SDA, mais l'Arduino a maintenant besoin de ses propres broches I2C matérielles - pas un gain net de broches Arduino, plutôt un déplacement du bus I2C du 8255 vers l'Arduino).
* Contrainte: aucune puce supplementaire (pas de registres a decalage) sur l'Arduino UNO (18 broches libres D2-D13/A0-A5, D0/D1 reserves a l'USB). Decision: implementer la solution "8255 en MODE 2" sur 18 broches - un SEUL bus de 8 bits (Port A) bidirectionnel, poignee de main materielle du 8255 sur le Port C, INTR du 8255 cable sur IR1. Realise (8088 + croquis Arduino reel):
  - include/hardware.inc: MASQUE_PIO = 11000001b (Port A mode 2, Port B mode 0 sortie, PC0-PC2 entrees), mots bit set/reset PIO_INTE2_SET (PC4=1, INTR sur octet recu) / PIO_INTE1_RESET (PC6=0), bits d'etat PC_OBF_N/PC_IBF/PC_TAG_UART, canaux Port B PB_CHAN_UART/LCD_CMD/LCD_DATA (0/1/2), etats ARD_UNKNOWN/ALIVE/ABSENT. Retires: PB_LCD_STROBE/PB_LCD_RS/PB_RX_ACK/PB_TX_STROBE (la poignee de main est maintenant materielle), PORTB_SHADOW_OFF (remplace par ARD_TX_STATE_OFF, meme adresse).
  - lib/common.asm: portb_write/portb_pulse REMPLACES par arduino_send (AL=octet, BL=canal): pose le canal sur le Port B puis ecrit le Port A (OBF# passe a 0). CONTROLE DE FLUX materiel gratuit: attend OBF#=1 avant d'ecrire (l'ancien "uart_tx_pulse_delay" placeholder disparait). Ne bloque jamais le boot sans Arduino: ARD_UNKNOWN attend jusqu'a ~3 s (l'UNO met 1-2 s a demarrer), ARD_ALIVE ~0,5 s puis declare ARD_ABSENT (n'attend plus, ecrase) jusqu'a revoir OBF#=1. Les 2 OUT sont sous pushf/cli/popf (arduino_send peut etre appelee depuis irq0_test_handler/int_not_implemented via uart_tx_string).
  - lib/uart.asm: uart_tx_byte = arduino_send canal UART. lib/lcd_i2c.asm: i2c_lcd_send_byte = arduino_send canal LCD_CMD/LCD_DATA; SUPPRIME tous les delais cote 8088 (lcd_delay/lcd_delay_long/lcd_powerup_delay) - l'Arduino gere les temps HD44780 et OBF# retient le 8088 s'il prend du retard. API publique inchangee.
  - solution-01.asm: init_8255 (mode 2, PB=0, INTE1=0, INTE2=1; SANS OUT PORTA - en mode 2 il placerait un octet parasite dans le tampon de sortie). irq1_ps2_handler/irq4_uart_rx_handler FUSIONNES en irq1_arduino_handler: lit Port C (IBF pour ignorer une interruption parasite, PC0 = etiquette: 0 scan code -> ps2_rx_push, 1 UART -> uart_rx_push), lit Port A (efface IBF/INTR), EOI, IRET. IR4 n'est plus cablee: PIC_MASK_TEST = 11111100b (IR0+IR1), vecteur INT 0Ch retire; ivt_dump_action/textes mis a jour. Lecture "in al,PORTA" juste avant le sti de start: INTR reste a 1 tant que le Port A n'est pas lu et le 8259 est declenche par FRONT - un octet arrive avant l'init du 8259 bloquerait sinon toute interruption future.
  - BUG LATENT corrige au passage (introduit avec le tampon circulaire de la version precedente): ps2_rx_push/ps2_read_byte/uart_rx_push/uart_rx_byte utilisaient BX comme index (add bp,bx) SANS mettre BH a 0 - dans une ISR, BH est arbitraire, l'octet aurait ete ecrit/lu a une adresse aleatoire. Ajout de "xor bh,bh" dans les 4 routines.
  - NOUVEAU croquis breadboard/arduino/ve2cuy_bridge/ve2cuy_bridge.ino (irq_test.ino, ancien test de branchement IR1/IR4 par boutons, est obsolete): decodage PS/2 par interruption INT0 (start/8 bits/parite impaire/stop verifies, resynchronisation apres 2 ms sans front), Serial materiel 9600 8N1 (UART_BAUD), LCD PCF8574 sur Wire (init 4 bits complete, 1 transaction de 4 octets par octet HD44780, attente 2 ms pour Clear/Home), file 8088->peripheriques de 255 entrees (retient le 8088 via OBF# quand pleine), espace minimal de 500 us entre deux octets Arduino->8088 (pas de broche pour IBF). Compile sans erreur/avertissement pour arduino:avr:uno (5192 octets, 972 octets de RAM).
  - Cablage (18 broches): D2 CLK PS/2, D3 DATA PS/2, D4 ACK#(PC6), D5 STB#(PC4), D6 OBF#(PC7), D7 TAG(PC0), D8/D9 CH0/CH1 (PB0/PB1), D10-D13+A0-A3 = PA0-PA7, A4/A5 = SDA/SCL du LCD; INTR (PC3) -> IR1 du 8259. Pull-up 10k conseille sur STB#/ACK# (flottants pendant le demarrage de l'Arduino). Ouvrir le moniteur serie reinitialise l'UNO (DTR): la sortie 8088 se perd ~2 s pendant ce redemarrage.
  - Verifie: make all/check/check-modules + build TEST_PS2, listing nasm -l octet par octet (arduino_send, irq1_arduino_handler, init_8255: C1/0C/09, i2c_lcd_send_byte). AUCUN test sur le materiel reel - hypotheses 8255 mode 2 a valider (etat initial OBF#=1 apres le mot de mode; INTR efface par la lecture du Port A; 8255 pilotant le bus uniquement pendant ACK# bas). README non mis a jour (toujours decrit l'ancien UART/PS2 bit-bangues).
* Confirmé sur le matériel réel: l'architecture Arduino + 8255 en mode 2 (18 broches) fonctionne de bout en bout. Premier essai: sortie UART corrompue (bits 5/6 et 4/7 permutés) - cause: A0..A3 câblées sur PA7..PA4 (les broches du 8255 sont numérotées 4,3,2,1 puis 40,39,38,37 pour PA0..PA7), pas un problème de timing ni de protocole. Corrigé côté croquis (ve2cuy_bridge.ino: BUS[4..7] = A3,A2,A1,A0) - clavier et UART OK ensuite. Hypothèses 8255 mode 2 (OBF# initial, INTR effacé par la lecture du Port A, bus piloté seulement pendant ACK# bas) validées par ce test.
* Bug rapporté sur le matériel réel: LCD incohérent - après un reset du 8088 seul le menu principal n'apparaît pas, et après un dump des registres l'affichage est "brisé". UART et clavier OK. Causes retenues (raisonnées d'après la doc du 8255, PAS encore confirmées sur le matériel), toutes côté croquis Arduino - aucun changement 8088:
  - COURSE SUR LE BUS: en mode 2 le 8255 remet OBF# à 1 dès que ACK# DESCEND (pas quand il remonte). takeFrom8088 lisait le canal puis les 8 broches du bus une par une (digitalRead, ~30 µs) avec ACK# bas: le 8088 voyait OBF# libre et écrivait l'octet suivant (~15 µs plus tard) pendant cette lecture, mélangeant deux octets. Un Function Set (28h) corrompu suffit à passer le HD44780 en mode 8 bits, d'où un LCD "brisé" persistant. Corrigé: après ACK# bas, un seul instantané PINB/PINC/PIND (< 1 µs) donne canal ET octet, ACK# remonte aussitôt, décodage ensuite (snapPorts/snapBit).
  - PAS DE REPRISE: un simple 28h ne récupère pas un LCD resté en mode 8 bits ou à mi-quartet (typiquement après un reset du 8088 seul - l'Arduino, lui, n'est pas réinitialisé). Corrigé: à chaque commande 28h reçue du 8088 (début de i2c_lcd_init), le croquis rejoue l'initialisation "par instruction" (30h x3 puis 20h, lcdResync) avant d'envoyer 28h, ce qui ramène le LCD en 4 bits depuis n'importe quel état (~6 ms par appel).
  - Compile sans erreur pour arduino:avr:uno (5286 octets). NB: struct Snap remplacée par un uint32_t (le préprocesseur Arduino insère les prototypes avant les types du croquis).
* Bug rapporté sur le matériel réel: le clavier ne répond pas toujours, il faut parfois appuyer plusieurs fois. Cause (raisonnée, pas encore confirmée sur le matériel): l'instruction INT met IF à 0 et ni int10h_handler ni int16h_handler ne le remettaient à 1 - donc AUCUNE IRQ1 n'était servie pendant tout l'affichage (UART/LCD). Depuis le pont Arduino, chaque octet envoyé par arduino_send peut attendre OBF# ~0,6 ms (LCD, I2C) à ~1 ms (UART 9600 baud) quand la file de l'Arduino est pleine, alors que le 8255 ne retient qu'UN octet reçu (IBF) et que l'Arduino en envoie un toutes les 500 µs (GAP_US): un octet clavier - typiquement le 0F0h d'un relâchement de touche, qui arrive PENDANT le rafraîchissement déclenché par l'appui - était écrasé avant lecture. ps2_get_char perdait alors son préfixe (touche suivante avalée ou dupliquée). Corrigé: "sti" au début de int10h_handler (sans danger: aucune ISR n'appelle INT 10h; arduino_send protège ses 2 OUT par pushf/cli/popf, POPF remet IF à 1) et de int16h_handler (AH=01h) - dans ce dernier, ps2_get_char attend l'octet qui suit un préfixe 0F0h/0E0h, que SEULE l'IRQ1 peut fournir: avec IF=0 c'était un blocage définitif possible. Vérifié via listing (FB en tête des deux gestionnaires); make all/check/check-modules + build TEST_PS2 validés. Si des touches se perdent encore: réduire l'intervalle n'aide pas - regarder plutôt la réception PS/2 côté Arduino (parité/parasites sur CLK/DATA).
* Touches encore perdues (ex: "Dump registres" puis Echap répété, il faut parfois appuyer plusieurs fois sur Echap) malgré le STI dans INT 10h/16h. Cause NON identifiée à ce stade. Analyse: côté 8088 la chaîne IRQ1 -> ps2_rx_push -> ps2_get_char est cohérente (relu en détail); les pertes les plus vraisemblables sont en amont - octet écrasé dans le verrou d'entrée du 8255 (un seul octet, l'Arduino en envoie un toutes les 500 µs sans voir IBF), trame PS/2 rejetée par l'Arduino (parité/parasites sur CLK/DATA), ou fil D7->PC0 (étiquette) intermittent (un scan code étiqueté "UART" part dans uart_rx_push et disparaît). Perte typique qui donne ce symptôme: si l'octet APRES un préfixe 0F0h est perdu, ps2_get_char avale la touche suivante (Echap) comme s'il s'agissait du code de relâchement. Réalisé:
  - BUG RÉEL trouvé au passage (pas la cause du symptôme ci-dessus): test_ram faisait un CLI sans jamais remettre IF - après le premier "Test RAM", IF restait à 0 dans le code appelant: plus aucune IRQ1 servie, donc clavier mort dans le menu (bloqué dans ps2_get_char). Corrigé par PUSHF au début / POPF avant chacun des 2 RET.
  - Croquis: DEBUG_PS2 (0 par défaut, 1 = trace sur le terminal, entrelacée avec la sortie du 8088): {76} octet décodé, {>76} octet envoyé au 8088, {P76}/{S76} erreur de parité/stop, {G} start parasite, {Rn} resynchronisation à n bits, {O} anneau plein. Permet de dire si un Echap perdu l'est avant l'Arduino, dans la réception PS/2, ou après (8255/8088). Complément côté 8088: %define TEST_PS2 (solution-01.asm) affiche chaque scan code reçu par le 8088.
* Constat sur le matériel: avec DEBUG_PS2=1 le clavier semble fonctionner correctement (la trace ralentit la boucle de l'Arduino et décale les envois) - la perte de touches est donc SENSIBLE AU TIMING, pas un défaut de logique 8088. Essai en cours: GAP_US 500 -> 2000 µs (trace désactivée). Si les pertes disparaissent: octet clavier écrasé dans le verrou d'entrée du 8255 avant lecture (l'Arduino ne voit pas IBF) - garder la valeur, et envisager un vrai contrôle de flux (accusé de réception via un canal 8088->Arduino). Si elles persistent: piste "coïncidence" entre une impulsion STB# de l'Arduino et une écriture du Port A par le 8088 (sortie ACTIVE de l'octet), ou bruit sur STB#/ACK#/CLK/DATA - prochain essai: n'envoyer un octet clavier que juste avant d'acquitter un octet du 8088 (OBF# bas), pour que le 8088 soit forcément à l'arrêt pendant l'impulsion.
* Cause trouvée grâce à la trace DEBUG_PS2 (séquences relevées sur le matériel: {F0}{>F0}{2E}{>2E}{76}{>76} = normal; {F0}{>F0}{S76}{G} = la trame 76 arrive avec une erreur de stop suivie d'un front parasite): le clavier envoie 0F0h puis le code de la touche COUP SUR COUP, et l'Arduino envoyait 0F0h au 8088 (impulsion STB#, bus de données, étiquette) PENDANT que la trame suivante arrivait sur CLK/DATA (D2/D3, tirées seulement par les pull-ups internes, voisines de D4/D5) - diaphonie -> trame rejetée. Le code de relâchement perdu, ps2_get_char (qui a déjà lu 0F0h) avale la touche suivante (Echap) : symptôme "appuyer plusieurs fois". Explique aussi pourquoi la perte dépendait du timing (la trace décale les envois). Corrigé côté croquis: ps2Quiet(): on n'envoie un octet clavier au 8088 qu'après KBD_QUIET_US=3000 µs sans front CLK (fin de la rafale), et on n'acquitte un octet du 8088 (ACK#) / n'envoie un octet UART reçu qu'après BUS_QUIET_US=400 µs de silence CLK; GAP_US 1000. Le 8088 est simplement retenu (OBF#) pendant les ~1 ms d'une trame. À confirmer sur le matériel; sinon compléter par des résistances de tirage 4,7 kΩ vers +5 V sur CLK et DATA et écarter ces fils de D4/D5.
* Trace après le correctif "silence CLK" (touche 3 pressée plusieurs fois): {F0}{76}{>F0}{>76} normal, puis {S26}{G}{F0}{S46}{G}{>F0}{26}{>26}{PE0}{G}{SCE}{R2}{S26}{G}{PE0}{G}{26}{>26} - trames abîmées. Le gel des accès au bus (ps2Quiet) fonctionne (F0/76 décodés AVANT tout envoi) mais ne couvre pas le bruit produit par l'Arduino LUI-MÊME pendant la trame: sortie série (D1/TX, voisine de D2/CLK) et I2C du LCD, très actifs quand le 8088 redessine le menu, plus la trace elle-même. Un front CLK parasite compté comme un bit décale la trame: {S26}{G} = parasite pris pour le bit de stop puis vrai stop pris pour un start invalide; 26 -> 46 = bit décalé. Corrigé côté croquis (ps2Isr): filtre anti-parasite (CLK doit rester basse PS2_GLITCH_US=10 µs après le front, un vrai front reste bas >= 30 µs; parasite compté {g} en trace), DATA par vote majoritaire de 3 lectures (PIND direct), et resynchronisation par silence (PS2_FRAME_GAP_US=250 µs sans front valide = nouvelle trame; avant: 2 ms, ce qui laissait une trame abîmée décaler les suivantes). ps2Act (tout front, valide ou pas) sert au gel de bus. Matériel conseillé si des erreurs subsistent: résistances 4,7 kΩ vers +5 V sur CLK et DATA, fils PS/2 éloignés de D0/D1/D4/D5/A4/A5, condensateur 100 pF de CLK et de DATA vers la masse.
* Confirmé sur le matériel réel: le clavier fonctionne correctement avec le filtre anti-parasite/vote majoritaire/resynchronisation par trame (ps2Isr) et le gel des accès au bus pendant une trame PS/2 (ps2Quiet). Trace DEBUG_PS2 remise à 0 par défaut (elle ajoute du trafic sur D1, voisine de CLK).
* Confirmé sur le matériel réel: LCD fonctionnel (correctifs OBF#/instantané du bus, resynchronisation par Function Set, STI dans INT 10h/16h).
* Prochaine étape demandée: pouvoir saisir des touches depuis le terminal UART (PC). Le chemin Arduino -> 8088 existait déjà (Serial.available -> étiquette PC0=1 -> irq1_arduino_handler -> uart_rx_push) mais rien ne consommait le tampon UART. Réalisé (8088 seulement, le croquis Arduino est inchangé):
  - lib/ps2.asm: ps2_get_char consulte MAINTENANT les deux tampons (PS/2 d'abord, puis UART) - donc TOUT ce qui en dépend (menus, saisie hexa, éditeur RAM, dump, registres, IVT) accepte indifféremment clavier PS/2 et terminal, sans autre changement. Nouvelle uart_get_key: mêmes résultats que la touche PS/2 équivalente (liste blanche = valeurs de ps2_keymap, minuscules mises en majuscules, DEL 7Fh = Retour arrière, LF ignoré, CR = Entrée, BH = 0). FLÈCHES par séquences ANSI ESC [ A/B/C/D (ou ESC O A/B/C/D) -> PS2_KEY_UP/DOWN/RIGHT/LEFT; autres séquences (ESC [ ... ~) consommées en entier et ignorées; un ESC seul (rien pendant ~50 ms, UART_ESC_TIMEOUT=2000 tours de uart_wait_byte, estimation à 4,77 MHz) = Echap. Nouvelle ps2_key_available (PS/2 OU UART, non bloquante) utilisée par dump_memory_action (Echap pendant un dump) et int16h_handler (AH=01h); ps2_read_byte, elle, reste sur le seul tampon PS/2.
  - lib/uart.asm: uart_rx_byte préserve maintenant BP (ps2_get_char, qui l'appelle, ne doit jamais toucher BP).
  - Terminal PC: désactiver l'écho local (c'est le 8088 qui écho), Entrée = CR. Débit maximal en réception ~1000 octets/s (GAP_US côté Arduino) - suffisant pour de la frappe, pas pour un collage massif.
  - Vérifié via listing (nasm -l) de ps2_key_available/ps2_get_char/uart_get_key; make all/check/check-modules + build TEST_PS2 validés. Pas encore testé sur le matériel réel.
* Confirmé sur le matériel réel: clavier via UART solide à 57600 bauds (UART_BAUD=57600 dans ve2cuy_bridge.ino, réglable - le 8088 n a aucune temporisation liée au débit).
* Demande: pouvoir éditer la RAM depuis le terminal - le bloc s'affichait sur l'UART sans possibilité d'édition (chaque redessin ajoutait 4 lignes au fil de l'eau, sans repère de la case courante). Les touches (flèches ANSI, chiffres hexa, Entrée, Q, R, Echap) fonctionnaient déjà depuis le terminal (ps2_get_char lit l'UART), il manquait l'affichage plein écran. Réalisé (8088 seulement) avec des séquences ANSI, pour edit_ram_action ET edit_run_action (elles partagent edit_ram_draw_grid):
  - Nouvelle vue TERMINAL edit_ram_draw_terminal (appelée par edit_ram_draw_grid, qui n'écrit PLUS sur l'UART - le LCD garde sa fenêtre de 4 lignes): titre (ligne 1), TERM_ROWS=8 lignes "SSSS: XX XX XX XX XX" (adresse réelle + contenu du TAMPON, lignes 3-10), aide (ligne 12), puis curseur du terminal placé SUR LA CASE COURANTE (ESC[l;cH) - les chiffres tapés (echo de ps2_edit_byte_value/edit_run_byte_value) s'affichent donc exactement sur la case. Chaque ligne est repositionnée en absolu et terminée par ESC[K: dessin EN PLACE, l'écran n'est efface (ESC[2J ESC[H) qu'UNE FOIS à l'entrée dans l'édition et une fois à la sortie (Echap/Q), pour que le menu reparte en haut.
  - Grille découpée en PAGES de 8 lignes logiques de 5 octets (40 octets): la page se déduit de la position du curseur (edit_ram_term_geometry, sans état supplémentaire) - la navigation (flèches, +-5 par ligne) est celle du LCD, inchangée.
  - edit_run_action: après 'r', les registres sont affichés SOUS la grille (ligne TERM_REGS_ROW=14, ESC[J efface l'ancien affichage) - le redessin qui suit ne les efface pas (dessin en place). Le tout tient dans 24 lignes de terminal (11 lignes de registres, de 14 à 24).
  - lib/uart.asm: nouvelles uart_tx_dec8 (décimal sans zéros de tête) et uart_ansi_goto (DH=ligne, DL=colonne, 1-based). hardware.inc: EDIT_TERM_TITLE_OFF/EDIT_TERM_HELP_OFF (pointeurs titre/aide fixés par chaque action). Le terminal doit interpréter l'ANSI (PuTTY, Tera Term, minicom...) et faire au moins 24 lignes x 80 colonnes.
  - Vérifié via listing (nasm -l) de edit_ram_draw_terminal; make all/check/check-modules + build TEST_PS2 validés. Pas encore testé sur le matériel réel.
* Confirmé sur le matériel réel: l'éditeur RAM plein écran sur le terminal (ANSI) fonctionne à 100% (édition par plage et Edit+Run, registres sous la grille).
* README.md mis à jour pour l'architecture Arduino: intro, matériel et tableau de câblage (18 broches), schéma bloc (8259, Arduino), nouvelle section "Pont Arduino (8255 en mode 2)" (protocole, canaux, contrôle de flux OBF#, réglages et trace du croquis, compilation arduino-cli), section "Interruptions matérielles (8259)", structure du dossier, fonctions UART/LCD I2C/PS2 réécrites (LCD parallèle marqué historique), saisie depuis le terminal (flèches ANSI, ESC), éditeur RAM plein écran ANSI, menu principal à 2 options.
* Nouvelle tâche: ajouter un interpréteur BASIC à la ROM, adapté aux E/S du projet, interactif par le terminal UART, option "3) Tiny Basic" du menu principal, dans son propre fichier (pas dans solution-01.asm). Base: PATB86 (Amand Tihon, 2019, https://codeberg.org/alrj/patb86, licence MIT - avis conservés dans l'en-tête du fichier), lui-même dérivé du Tiny BASIC 8080 de Li-Chen Wang. Réalisé:
  - NOUVEAU lib/tiny_basic.asm (~1600 lignes, ~2,5 Ko assemblés): cœur de PATB86 conservé avec ses commentaires (analyse, expressions, FOR/NEXT, GOSUB, INPUT, PRINT, LIST...), tous les noms préfixés "tb_" (conflits évités: macro "print", labels list/run/stop/error/size...). Adaptations: (1) le .COM DOS (DS=ES=SS=CS) devient un programme à DS=ES=SS=VAR_SEG (1000h) le temps de l'exécution - tiny_basic sauve tous les registres/segments et SP, installe une pile privée (F000h-F410h), restaure tout à la sortie (BYE, Ctrl-X); tables de commandes en ROM lues par [cs:bx]; messages copiés en RAM à l'entrée. Disposition: texte BASIC 0100h-7DFFh (32000 octets, comme l'original: SIZE reste positif en entier signé), tampon/variables/état à partir de 7E00h (4 octets de garde: @(0) tombait sur le tampon de ligne dans l'original), zone du firmware F800h-FFFFh et code Edit+Run 0000h-00FFh NON touchés. (2) E/S = terminal UART seulement (le PS/2 n'a pas lettres/symboles): tb_outch -> uart_tx_byte (CR suivi de LF), tb_chkio -> uart_rx_available/uart_rx_byte (Ctrl-C = retour à Ok, Ctrl-X = menu), tb_getln avec écho, BS/DEL, LF et caractères de contrôle ignorés, séquences ANSI (ESC [ ... / ESC O x) avalées en entier. (3) PAS de HLT dans la saisie (l'original attendait le tick BIOS; ici un octet déjà reçu ne réveillerait jamais un HLT): scrutation, dont le temps d'attente sert de graine à RND (pas d'horloge). (4) commande directe BYE; comparaison de pile non signée (SP dans la moitié haute du segment).
  - solution-01.asm: menu principal à 3 options (UART + LCD, lcd_txt_menu_main_l3), .main_3 affiche 3 lignes LCD puis "call tiny_basic". irq0_test_handler et int_not_implemented remettent DS=CS (push ds/push cs/pop ds) - leurs messages sont en ROM et ces interruptions peuvent survenir pendant Tiny BASIC (DS=1000h). Makefile: TB_BIN, dépendance de la ROM, check-modules, clean, cible "test".
  - BANC D'ESSAI (aucun matériel disponible pour valider l'interpréteur): tests/tb_test.asm + tests/tb_test.py exécutent tiny_basic sous l'émulateur Unicorn (pip install unicorn, "make test"): 56 vérifications - expressions/opérateurs, FOR/NEXT (imbriqués, pas négatif), GOSUB, IF, INPUT, RND, LIST/NEW/remplacement/suppression de lignes, erreurs What?/How?, Ctrl-C, saisie (BS, DEL, ANSI), retour au menu par BYE/Ctrl-X (registres, DS=CS et SP restaurés) et AUCUNE écriture hors des zones prévues du segment 1000h. Deuxième série avec les VRAIES routines uart_* (arduino_send, tampon circulaire; 8255 et remplissage du tampon émulés). Les entrées sont livrées ligne par ligne, seulement quand l'interpréteur attend - sinon le test Ctrl-C de chaque instruction (chkio, comme dans l'original) avale les octets d'avance. Tous passent; bugs trouvés par les tests: séquences ANSI de flèches insérées dans la ligne (corrigé: tb_escst).
  - Vérifié: make all/check/check-modules + build TEST_PS2 + make test. PAS encore testé sur le matériel réel (Arduino, terminal, LCD).
* Confirmé sur le matériel réel: Tiny BASIC (option 3 du menu principal) fonctionne, piloté par le terminal UART.
* README: exemple Tiny BASIC de la suite de Fibonacci (sortie réelle vérifiée sous émulateur). Le programme se termine sur une erreur How? à la ligne 110 (17711+28657 dépasse 32767; le test B<=32000 de la ligne 130 ne peut pas l'éviter, il est évalué après l'addition); variante sûre documentée: 130 IF B<=17711 GOTO 100. Les deux cas ont été ajoutés à tests/tb_test.py.
* Nouvelle demande: un BASIC plus riche que Tiny BASIC, « inspiré » de GW-BASIC (github.com/microsoft/GW-BASIC, MIT) SANS accès disque, imprimante, etc., avec fonctions de chaînes, RND/RANDOMIZE, PEEK/POKE, nombres flottants; ajouté au menu principal (option 4). Réimplémentation ORIGINALE (le code source de M6502/GW-BASIC n'est pas réutilisable tel quel): mêmes mots-clés, messages/numéros d'erreur, règles de types et de priorité, format d'affichage des nombres que GW-BASIC; avis de licence MIT conservé dans lib/basic.asm.
  - NOUVEAUX lib/basic.asm (cœur: RAM, entrée/sortie du menu, saisie, erreurs, tokeniseur), basic_tokens.inc (liste UNIQUE des mots-clés, développée 3 fois par macro: jetons, textes, gestionnaires), basic_float.asm + basic_fmath.asm (flottants IEEE-754 binary32 LOGICIELS: + - * / comparaison, conversions, INT/FIX, conversion décimale 7 chiffres, SQR EXP LOG SIN COS TAN ATN et ^ par polynômes/séries), basic_eval.asm (évaluateur à montée en priorité, pile de valeurs, variables, tableaux), basic_str.asm (tas de chaînes, RAMASSE-MIETTES par compactage, concaténation, comparaison, mise en forme des nombres), basic_stmt.asm (programme tokenisé, boucle d'exécution, toutes les instructions), basic_func.asm (fonctions), basic_data.asm (tables et messages en ROM). CPU 8086 strict (pas de PUSH immédiat, décalages par CL...).
  - Fonctionnalités: entiers 16 bits, simple précision (7 chiffres), chaînes 0-255 (DEFINT/DEFSNG/DEFDBL/DEFSTR), tableaux jusqu'à 8 dimensions, opérateurs ^ * / \ MOD + - comparaisons NOT AND OR XOR EQV IMP, &H/&O, PRINT (TAB, SPC, zones de 14), INPUT/LINE INPUT (?Redo from start), IF/THEN/ELSE imbriqués, FOR/NEXT, WHILE/WEND, GOSUB/RETURN, ON GOTO/GOSUB, DATA/READ/RESTORE, DEF FN (plusieurs paramètres, chaînes), SWAP, ERASE, MID$ en instruction, RND/RANDOMIZE, PEEK/POKE/DEF SEG/INP/OUT/WAIT/CALL, LIST/DELETE/NEW/RUN/CLEAR/CONT/TRON/TROFF, CLS/LOCATE/COLOR/BEEP (ANSI), Ctrl-C = Break (les cadres FOR/GOSUB restent sur la pile: CONT reprend), Ctrl-X/SYSTEM/BYE = menu. Non implémentés: fichiers, LPRINT, graphiques, SOUND/PLAY, ON ERROR, PRINT USING, TIMER/DATE$/TIME$ (pas d'horloge; RANDOMIZE/RANDOMIZE TIMER brassent la graine avec le temps d'attente de la frappe), double précision (= simple).
  - Choix de conception: DS=ES=SS=VAR_SEG (1000h) avec pile privée comme Tiny BASIC (programme dès 0C00h, chaînes jusqu'à DFF0h, pile E000h-F3F0h, F800h+ non touché); cadres FOR/GOSUB/WHILE sur la pile du 8088; une file de 15 touches (bas_chkbrk) alimente INKEY$/INPUT$ pendant qu'un programme tourne sans jamais masquer Ctrl-C; l'affectation évalue le membre droit AVANT la cible (les tableaux se déplacent quand une variable simple est créée); POKE refuse les écritures dans l'IVT, l'espace de travail du BASIC et les variables du firmware (Illegal function call).
  - solution-01.asm: menu principal à 4 options (UART + LCD, lcd_txt_menu_main_l4, .main_4 -> basic_run, lcd_txt_bas_l1..3). Makefile: BAS_BIN/BAS_SRC, check-modules, dépendances de la ROM, `make test` lance aussi tests/fl_test.py et tests/basic_test.py. README: nouvelle section « BASIC », menu, arborescence, outils.
  - BANCS D'ESSAI (aucun matériel utilisé): tests/fl_test.py (bibliothèque flottante vs numpy.float32: arrondi exact de + - * /, quelques ulp pour les fonctions), tests/basic_test.py + basic_harness.py + basic_test.asm (Unicorn: 175 vérifications dont ramasse-miettes, erreurs, CONT, Ctrl-C, gardes POKE, retour au menu registres/DS/SP restaurés, aucune écriture hors zones; mode réel avec les vraies routines uart_*). Essais aléatoires hors dépôt: lignes aléatoires (aucun plantage, aucune écriture hors zones), programmes structurés (chaînes/GC), expressions numériques comparées à un oracle Python (0 écart sur ~1000 expressions). Le harnais ne livre une ligne saisie que lorsque l'interpréteur ATTEND (comme un utilisateur).
  - Bugs trouvés et corrigés pendant les essais: fl_ftoa détruit DI (mise en forme), COS(0) donnait 0.99999988 (|x| < 2^-12: cos = 1, sin = x), ELSE/apostrophe en fin d'instruction, AX écrasé par le marqueur de cadre (GOSUB), FAC écrasé par les indices de la cible d'une affectation, Ctrl-C masqué par une touche en attente (file de touches), Ctrl-C ignoré dans INPUT$, récursion de DEF FN sans borne (STKCHK).
  - Vérifié: make all/check/check-modules + build TEST_PS2 + make test. PAS encore testé sur le matériel réel (Arduino, terminal, LCD).
* Demande: commande HELP dans le BASIC (sommaire des commandes disponibles). Nouveau jeton HELP (basic_tokens.inc) -> st_help (basic_stmt.asm) qui affiche msg_help (basic_data.asm, 15 lignes sous 80 colonnes, ASCII); la banniere mentionne HELP. Tests: 2 verifications ajoutees a tests/basic_test.py (177 au total); README mis a jour. Bug trouve par les tests: st_help ecrasait SI (le programme s arretait apres HELP).
* Confirmé sur le matériel réel (début du test): le BASIC « GW-BASIC-like » (option 4 du menu principal) fonctionne correctement, piloté par le terminal UART.
* Aide en ligne du BASIC (HELP): messages traduits en anglais, titre '--- VE2CUY 8086 BASIC: command summary (HELP) ---' (demande), ligne 'Memory' ajoutée (FRE(0) = free bytes, FRE("") = after cleanup, POS(0)). Tests mis à jour (177 vérifications).
* Demande: pouvoir éditer les lignes de code du BASIC depuis le terminal. Nouvelle commande EDIT n | EDIT . (jeton EDIT -> st_edit, basic_stmt.asm): la ligne est détokenisée dans B_IBUF (detok_line) puis éditée par bas_editbuf (flèches gauche/droite, Début/Fin, Suppr, retour arrière, Ctrl-A/E/K, insertion, séquences ANSI [D [C [H [F [n~ et O-x; Entrée valide, Ctrl-C annule, Ctrl-X = menu), redessin par CR + texte + ESC[K + ESC[nC; la ligne validée passe par bas_gotline (comme une ligne saisie). b_lastln = dernière ligne entrée/éditée/listée/en erreur (EDIT .). Nouveau message 23 "Line buffer overflow" (ligne développée > 240 caractères). Limite connue: pas de gestion du retour à la ligne du terminal (lignes > ~80 colonnes) ni d'Échap seul (séquences seulement; Ctrl-C annule).
  - Correctif lié: LIST (et EDIT) ajoutent un espace entre un mot-clé et un identifiant/nombre qui le suit sans espace (?A -> "PRINT A", GOTO100 -> "GOTO 100"), sinon la relecture ne retrouvait plus le mot-clé; FNx est exclu.
  - Tests: 17 vérifications ajoutées à tests/basic_test.py (194 au total); HELP mentionne EDIT. Bug trouvé par les tests: bas_error écrasait AL (code d erreur) en mémorisant b_lastln (CONT cassé).
* Étude/portage du pont Arduino UNO -> WeAct Black Pill V3.1 (STM32F411CEU6): plus rapide, USB natif (plus de reset DTR), RTC, plus de broches, tolérance 5 V, flash SPI pour un futur disque. Avis donné (points à vérifier: tolérance 5 V par broche FT, niveaux 3,3 V vs entrées TTL/HC, PB2/BOOT1, alimentation USB/5 V, la flash de la carte est en SPI simple - le F411 n'a pas de QUADSPI). Plan en 4 étapes: 1 portage à l'identique (fait), 2 IBF + tampons + capture PS/2 par timer, 3 RTC + canal de commandes (TIMER/TIME$/DATE$ dans le BASIC), 4 disque FAT.
  - Cœur STM32 installé sous WSL (arduino-cli 1.3.0, snap: configuration sous ~/snap/arduino-cli/62/.arduino15, URL STM32duino ajoutée): STMicroelectronics:stm32 2.4.0. FQBN de la Black Pill: STMicroelectronics:stm32:GenF4:pnum=BLACKPILL_F411CE,usb=CDCgen,xserial=generic (la carte est dans « Generic STM32F4 series », pas de FQBN BlackPill). arduino-cli (snap) ne lit pas /tmp.
  - NOUVEAU breadboard/arduino/ve2cuy_bridge_stm32/ (ve2cuy_bridge_stm32.ino + README.md): même protocole 8255 mode 2 que la version UNO (firmware 8088 inchangé). Broches: bus PB0-PB7 (ordre direct D0=PA0), ACK# PB12 et STB# PB13 en DRAIN OUVERT (+10 kohm vers 5 V, pull-up interne de secours), OBF# PB14, TAG PB15, canal PA8/PA9, IBF PA10 (facultatif, USE_IBF), TAG1/TAG2 PA3/PB10 (futur), PS/2 CLK PA1 (EXTI1)/DATA PA2, LCD I2C PB8/PB9, USB PA11/PA12. Accès au bus par registres GPIO (MODER/BSRR/IDR, instantané des deux ports), PB3/PB4 rendues au GPIO, octets jetés après TX_STALL_MS si le port USB n'est pas lu, LED PC13 en heartbeat. Compile (33 Ko de flash sur 512, aussi avec USE_IBF=1 et DEBUG_PS2=1). NON testé sur le matériel.
* Vérification de la tolérance 5 V dans medias/stm32f411.pdf (DS10314 Rev 8, tableau 8, UFQFPN48): toutes les broches prévues sont FT (5 V) SAUF PA0 et PB5 (TC, 3,3 V). CORRECTION du brochage du pont STM32 (PB5 faisait partie du bus PB0-PB7 annoncé plus haut): bus en deux quartets sur GPIOB (D0-D3 = PB12-PB15, D4-D7 = PB6-PB9, busFromIdr/busDrive, masques MODER 0xFF0FF000/0x55055000 vérifiés), ACK# PB0 et STB# PB1 (drain ouvert), OBF# PA8, canal PA9/PA10, TAG PB4, IBF PA15, TAG1 PB5 (sortie seulement), TAG2 PA3, PS/2 PA1/PA2, I2C2 PB10 (SCL, AF4) / PB3 (SDA, AF9) — confirmé dans le tableau des fonctions alternées et dans PeripheralPins.c du cœur. PB2 (BOOT1) à ne pas utiliser: un signal haut au repos y empêcherait le mode DFU. Croquis recompilé (33 Ko, aussi avec USE_IBF=1/DEBUG_PS2=1); README du dossier ve2cuy_bridge_stm32 mis à jour. Toujours NON testé sur le matériel.
* Le portage du pont STM32 est désormais un projet PlatformIO: dossier breadboard/arduino/8088_bridge_stm32/ (déplacé/renommé par l'utilisateur depuis ve2cuy_bridge_stm32/; platformio.ini avec platform ststm32, board blackpill_f411ce, framework arduino et build_flags -D PIO_FRAMEWORK_ARDUINO_ENABLE_CDC -D USBCON -D HAL_PCD_MODULE_ENABLED pour que Serial soit le port USB). Le croquis est dans src/main.cpp (#include <Arduino.h> ajouté; l'ancien .ino de la racine est supprimé car PlatformIO ne compile que src/). Compilation: C:\Users\alin_\.platformio\penv\Scripts\platformio.exe run -> SUCCESS (33 664 octets de flash, 5 748 de RAM; cœur framework-arduinoststm32 2.7.1, toolchain GCC ARM 12.3.1). README du dossier mis à jour (commandes PlatformIO). Toujours NON testé sur le matériel.

* Confirmé sur le matériel: le téléversement du pont STM32 en mode DFU (BOOT0 + NRST, upload_protocol = dfu, désormais activé dans platformio.ini) fonctionne avec platformio run -t upload. Le fonctionnement du pont avec le 8088 (bus, PS/2, LCD) reste à valider.
* Premier essai du pont STM32 avec le 8088 (essais préalables sur le matériel: LED PC13 à 1 Hz, LCD I2C effacé, clavier PS/2 décodé sans erreur, {g} presque supprimés par des pull-ups 4,7-10 kohm sur CLK/DATA): le terminal reçoit le menu avec des caractères faux. Diagnostic sur le texte reçu (espace 0x20 -> 0x40, '-' 0x2D -> 'M' 0x4D, 'p' 0x70 -> octet >= 0x80, quartet bas correct): le QUARTET HAUT du bus est inversé (D4<->D7, D5<->D6), comme sur l'UNO (PA4-PA7 du 8255 câblées à l'envers). Correctif logiciel dans src/main.cpp: BUS_HIGH_NIBBLE_REVERSED 1 (fixHighNibble, involution appliquée à la lecture busFromIdr et à l'écriture busDrive); la simulation reproduit exactement les valeurs observées. Compile (platformio run). À valider sur le matériel après téléversement.

* Confirmé sur le matériel réel: le pont STM32 (WeAct Black Pill V3.1, projet PlatformIO 8088_bridge_stm32, BUS_HIGH_NIBBLE_REVERSED 1) fonctionne avec le 8088: toutes les fonctions du menu essayées par le clavier PS/2 et par le terminal UART (USB), LCD I2C inclus. Étape 1 du portage (protocole identique à la version UNO) validée; étapes suivantes possibles: IBF + tampons + capture PS/2 par timer, RTC (TIMER/TIME$/DATE$), disque.
* Demande: faire 1 (RTC), puis 2 (IBF + tampons + capture PS/2 par timer), puis 3 (disque), dans cet ordre. ÉTAPE 1 - horloge temps réelle (TIMER, TIME$, DATE$ dans le BASIC), sans câbler de nouveau signal autre que TAG1:
  - Protocole: canal 3 du Port B (PB_CHAN_CMD) = commandes pour le pont; réponses du pont étiquetées PC1 = 1 (PC_TAG_REPLY, prioritaire dans irq1_arduino_handler) -> tampon circulaire BRIDGE_RX_HEAD/TAIL/BUF (0FC52h-0FC63h, hardware.inc). Commandes: 00h PING (B1h, version 1, capacités), 01h LIRE (8 octets: année lo/hi, mois, jour, h, min, s, centièmes), 02h + 7 octets RÉGLER (2000-2099).
  - NOUVEAU lib/bridge.asm: bridge_rx_push (ISR), bridge_rx_flush, bridge_rx_get (délai BR_TIMEOUT ~0,5 s), bridge_tx, rtc_get (ES:DI, 8 octets, CF=1 si pas de réponse), rtc_set (DS:SI, 7 octets). Inclus par solution-01.asm et lib/basic.asm (le banc d'essai fournit des simulacres).
  - BASIC: nouveaux jetons TIMER, TIME$, DATE$ (fonctions; T_DATES = dernier jeton de fonction) et les instructions TIME$="h[:m[:s]]" et DATE$="m-d-yy[yy]" (séparateurs - ou /, années 2000-2099, validation des jours/bissextile, Illegal function call sinon); TIMER = secondes depuis minuit en simple précision (centièmes). Erreur 24 "Device Timeout" si le pont ne répond pas. RANDOMIZE TIMER utilise maintenant l'horloge (l'ancien contournement est supprimé). HELP a une ligne Clock.
  - Pont STM32 (8088_bridge_stm32/src/main.cpp): bibliothèque STM32duino RTC 1.8.0 (la 1.9/2.0 exigent un cœur plus récent que celui de PlatformIO 17.4.0), init sur le quartz LSE (RTC_USE_LSE), lecture cohérente par registres SSR/TR/DR (centièmes = (PREDIV_S-SSR)/(PREDIV_S+1)*100), automate de commandes (canal 3, abandon après CMD_TIMEOUT_MS), file de réponses de 64 octets envoyées en priorité avec l'étiquette 2 (TAG = PB4 bit 0, TAG1 = PB5 bit 1). Compile (39,4 Ko de flash).
  - MATÉRIEL À AJOUTER AVANT DE TÉLÉVERSER LA NOUVELLE ROM: fil PB5 (TAG1) -> PC1 du 8255 (broche 15) + 10 kohm de PC1 à la masse (sinon les octets clavier/UART sont pris pour des réponses). Pile CR2032 sur VB conseillée. Pas de RTC sur l'UNO: Device Timeout.
  - Tests: 22 vérifications ajoutées à tests/basic_test.py (simulacre de l'horloge fake_clock/fake_fail dans tests/basic_test.asm, run(..., poke=...) dans le harnais): heure/date/TIMER, réglages, validations, pont muet. NON testé sur le matériel.
  - DURCISSEMENT (avant tout téléversement de la ROM): l'ISR ne classe un octet comme réponse (PC1 = 1) que si BRIDGE_EXPECT_OFF (0FC64h) est à 1, mis par rtc_get pendant la commande (~10 ms) puis remis à 0; hors de cet intervalle une PC1 non câblée/flottante ne perturbe plus le clavier ni l'UART. Le fil PB5 -> PC1 (+ 10 kohm à la masse) reste nécessaire pour un TIMER/TIME$/DATE$ fiable.
  - NOUVEAU tests/bridge_test.asm + bridge_test.py (13 vérifications, dans make test): vraies routines arduino_send/bridge_rx_get/rtc_get/rtc_set sous émulateur avec le 8255 émulé; le script joue le pont et l'ISR (réponses rangées dans BRIDGE_RX_* seulement si BRIDGE_EXPECT = 1): commandes 01h/02h+7 octets sur le canal 3, réponse de 8 octets, flush des réponses périmées, enroulement du tampon, pont muet -> CF = 1 et BRIDGE_EXPECT remis à 0, aucune écriture hors zones. make test: 216 (BASIC) + 13 (pont) vérifications. L'ISR elle-même (solution-01.asm) n'est vérifiée que par relecture et assemblage.

* Confirmé sur le matériel réel: TIME$ et DATE$ (lecture et réglage) fonctionnent dans le BASIC avec la RTC du pont STM32 (canal 3, réponses PC1). TIMER et RANDOMIZE TIMER: à confirmer.
* Confirmé sur le matériel: PRINT TIMER (deux appels successifs) fonctionne; IBF (PC5 du 8255) est câblée sur PA15 du pont (prérequis de l'étape 2).
* Demande: pouvoir utiliser '?' pour PRINT en mode direct et pas seulement sur une ligne numérotée. Constat: '?' était déjà accepté en mode direct (le tokeniseur le convertit en jeton PRINT avant l'exécution; vérifié: ? 1+1, A=5:?A, IF..THEN ?5, FOR..:?I:NEXT, ?TAB(3)...), mais la transformation n'était visible que par LIST/EDIT. Ajout: b_qflag (mis par le tokeniseur), echo_rewrite (basic_stmt.asm): après Entrée, la ligne est réaffichée une ligne plus haut avec PRINT (ESC[A, CR, texte, ESC[K, CRLF), en direct comme en numéroté (numéro de ligne compris), sauf ligne saisie >= 70 caractères ou développée >= 78. detok_line est scindée en detok_text (réutilisée). Tests: 4 vérifications ajoutées/adaptées.
* Bug rapporté (collage d'un programme BASIC dans le terminal): lignes perdues ou tronquées (ex: "100 PRINT B" et "110 " disparus, "130" devenu "0"). Diagnostic mesuré sous émulateur: le 8088 mettait 3 800 à 10 300 instructions (~ 13 à 35 ms à 4,77 MHz) pour tokeniser/insérer UNE ligne (kw_lookup balayait toute la table des mots-cles pour chaque mot, et les identifiants - jamais trouvés - la parcouraient en entier), alors que le pont envoyait 1 octet/ms dans un tampon UART de 16 octets: dès qu'une ligne prenait plus de ~15 ms, les octets les plus anciens étaient écrasés (16 octets perdus = exactement "100 PRINT B", CR et "110 "). IBF seul n'aurait rien changé (l'ISR vide le 8255 immédiatement dans ce tampon) et aurait aggravé le cas en accélérant l'envoi.
  - Correctifs: (1) kw_lookup par SEAUX construits à l'assemblage (basic_data.asm: kw_idx par lettre, kw_ptr, labels kwt_*, modes 3/4 de la macro KW): 700 à 1 400 instructions par ligne au lieu de 3 800-10 300 (5 à 8 fois plus rapide); (2) tampon UART du 8088 porté de 16 à 256 octets (UART_RX_BUF_OFF = 0FD00h, indices d'un octet, uart.asm); (3) pont: IBF activée par défaut (USE_IBF 1: aucun octet écrasé; réponses RTC dès que IBF retombe) et LINE_DELAY_MS = 15 ms après chaque CR du PC.
  - Tests: banc à débit fixe (basic_harness paced=N: 1 octet toutes les N instructions, comme le pont; le tampon déborde en écrasant le plus ancien): le programme de 7 lignes est collé sans perte à N=300 (et jusqu'à N=60); collage de 60 lignes (2,2 Ko) sans perte à N=300 (des pertes apparaissent seulement à N <= 200, d'où LINE_DELAY_MS).

* Confirmé sur le matériel réel: le collage du programme BASIC de 7 lignes (Fibonacci) fonctionne après les correctifs (tokeniseur par seaux, tampon UART 256 octets, IBF active, LINE_DELAY_MS = 15 ms). Étape 2 du plan (IBF + tampons + capture PS/2 par timer): IBF FAITE (USE_IBF 1); tampons: le tampon UART du 8088 (16 -> 256 octets) est FAIT, les tampons du pont n'ont pas été agrandis (l'USB est déjà contrôlé de flux; la file 8088 -> PC de 256 entrées suffit); capture PS/2 par timer NON faite (le PS/2 fonctionne bien avec les pull-ups; à reprendre seulement si des touches se perdent). Prochaine étape demandée: 3 (disque).
* Confirmé sur le matériel réel: la flash du Black Pill est soudée, 128 Mbit (W25Q128, 16 Mo), en SPI (le STM32F411 n'a pas de QUADSPI). Étape 3 demandée: DISQUE. Choix (le PC en lecteur USB, question restée sans réponse, n'est PAS fait): volume FAT16 (MBR + partition) sur la flash, géré par le PONT avec les bibliothèques Adafruit SPIFlash + SdFat (fork Adafruit), fichiers à la racine, noms 8.3; le 8088 y accède par des commandes du canal 3 (10h-19h: statut, formater, ouvrir, lire, écrire, fermer, répertoire début/suivant, supprimer, espace libre; protocole détaillé dans lib/bridge.asm et le README du pont). Choix d'architecture: niveau FICHIERS (pour le BASIC); un accès par secteurs (DOS) pourra s'ajouter plus tard sur le même canal.
  - 8088: lib/bridge.asm étendu (fs_open/read/write/close/dir_first/dir_next/delete/format/free/status, délais FS_WAIT (~2,8 s) et FS_WAIT_FMT (~37 s), bridge_rx_get_t); tampon des réponses porté de 16 à 64 octets (BRIDGE_RX_BUF_OFF = 0FC70h, hardware.inc). BASIC (lib/basic_disk.asm, nouveaux jetons): SAVE "f" (texte ASCII CR LF, une ligne par ligne, via detok_line), LOAD "f", MERGE "f" (chaque ligne du fichier passe par bas_tokenize + prog_edit, comme une ligne saisie; mode direct seulement), RUN "f", FILES (noms, tailles, espace libre; Ctrl-C l'interrompt), KILL "f" (nom exact), FORMAT "YES". Noms: majuscules, 1-12 caractères, ".BAS" ajouté s'il n'y a pas de point (sauf KILL). Table des messages d'erreur refaite en entrées [numéro][texte][0] (numérotation GW-BASIC 53, 54, 55, 57, 58, 61, 64, 66, 71 ajoutées); erreurs disque: File not found, Bad file name, Disk full, Disk not Ready, Disk I/O error, Direct statement in file, Device Timeout (pont muet). Un OPEN ferme le fichier précédent (pas de fichier bloqué ouvert après une erreur BASIC).
  - Pont STM32 (8088_bridge_stm32/src/main.cpp): flash SPI1 (PA4 CS, PA5-PA7), FatVolume/File32, formatage AUTOMATIQUE seulement si la flash est neuve (premier secteur tout FFh ou tout 0) - jamais sur un disque utilisé; flash.syncBlocks() à chaque fermeture/suppression/formatage; automate de commandes généralisé (cmdBuf/cmdNeed). Compile (54 Ko de flash, 8,7 Ko de RAM).
  - Tests: BridgeModel (tests/basic_harness.py): modèle Python du pont (horloge + fichiers en dictionnaire + pont muet / disque non prêt) branché sur les VRAIS ports du 8255 pour les deux modes du banc; plus aucun simulacre de rtc_get/rtc_set (le banc utilise les vraies routines de lib/bridge.asm). 24 vérifications horloge + disque (SAVE/LOAD/MERGE/RUN/FILES/KILL/FORMAT, fichier de plusieurs blocs de 32 octets, 40 lignes aller-retour, erreurs, disque plein, pont muet, disque non prêt). NON testé sur le matériel: la flash, le formatage et les commandes du pont.
  - MATÉRIEL: rien à ajouter (la flash est sur la carte). Téléverser le pont d'abord, puis la ROM; au premier démarrage la flash neuve est formatée (quelques secondes), puis SAVE/LOAD/FILES fonctionnent depuis le BASIC.

  - Schéma de la Black Pill (medias/STM32F411CE-Black-Pill-Board-Schematic-Diagram.webp, ajouté par l'utilisateur) consulté: la flash W25Qxx est bien câblée F_CS = PA4, SCK = PA5, MISO = PA6, MOSI = PA7 (SPI1); quartz 32,768 kHz (Y1) et 25 MHz présents; VB (pile) alimente VBAT par une diode (BAT54C) sans charge.
* Matériel: après le téléversement de la version « disque », `FILES` donne `Device Timeout` et `PRINT TIME$` ne fonctionne plus (LED du pont qui clignote). Cause non trouvée par lecture du code (les broches SPI par défaut du variant Black Pill sont bien PA5/PA6/PA7, pas de conflit avec SDA/TAG/TAG1). Ajout d'un diagnostic dans le pont (`DEBUG_FS 1`, main.cpp): chaque commande du canal 3 reçue est signalée sur le port série USB (`[br] op=0x.. n=..`) et, à la première, l'état de la flash (`[fs] flash JEDEC=.. taille=.. flashOk=.. fsOk=..`). À remettre à 0 une fois le problème résolu.
* Matériel: `PRINT TIME$` donne `Device Timeout` alors que le pont envoie bien les 8 octets (trace `[tx]`) et que la flash est détectée (W25Q64, 8 Mo: JEDEC EF4017, pas 16 Mo). Lecture de la RAM du 8088 (PEEK): le tampon de réponses reçoit des octets, mais pas les 8 attendus (octets manquants/altérés). Cause probable: le chemin rapide des réponses (`USE_IBF`, sans espace GAP_US) suppose que PA15 (IBF) reflète l'état du 8255; s'il ne le fait pas, les octets se succèdent plus vite que l'ISR du 8088 et s'écrasent dans le 8255. Chemin rapide RETIRÉ (les réponses repassent par `canSend()`: IBF + GAP_US, comme avant l'IBF, ce qui fonctionnait sur le matériel); la trace `[tx]` affiche maintenant l'état d'IBF (PA15) juste après l'envoi (doit valoir 1).
* Matériel: CONFIRMÉ avec le pont "GAP_US" (sans chemin rapide): `PRINT TIME$` (18:31:11) et `FILES` (FIB.BAS 105, 8 256 512 octets libres) fonctionnent. Le volume est donc bien monté et un SAVE antérieur a été écrit. La puce est une W25Q64 (8 Mo), les docs sont corrigées (elles disaient 16 Mo). La trace `[tx]` montrait `ibf=0` après chaque envoi (échantillonné après une impression, donc peu probant): l'échantillon est maintenant pris 2 µs après STB# dans sendTo8088 (doit valoir 1 si PC5 → PA15 est bon). DEBUG_FS reste à 1 le temps de ce test.
* Matériel: la trace montre `ibf=0` 2 µs après STB# pour chaque octet envoyé: l'entrée PA15 ne voit JAMAIS IBF à 1, alors que l'ISR du 8088 lit bien PC5 (PORTC) à 1. Le fil PC5 → PA15 est donc mal branché (mauvais contact, mauvaise broche du 8255 ou de la carte). Sans effet fonctionnel (IBF vaut 0 = « libre »; l'espace GAP_US protège), mais le contrôle de flux par IBF n'agit pas. DEBUG_FS remis à 0.
* Matériel: le fil PC5 → PA15 n'était PAS branché jusqu'ici (le confirme l'utilisateur, qui vient de le faire): `ibf=1` après chaque envoi. Conséquence: tous les essais précédents (collage de code, RTC, disque) ont tourné avec IBF « libre » en permanence, protégés seulement par GAP_US et LINE_DELAY_MS. À revalider avec IBF réellement actif (collage du listing Fibonacci, TIME$, FILES, SAVE/LOAD).
* Matériel: CONFIRMÉ avec le pont sans traces (DEBUG_FS 0) et IBF branché: collage de code, TIME$/DATE$/TIMER, SAVE/LOAD/FILES/KILL fonctionnent (FIB.BAS 105 octets, 8 256 512 octets libres sur la W25Q64). Étape 3 (disque) terminée. GAP_US (1 ms) conservé pour tous les octets pont -> 8088.
* Demande: trois chantiers, dans l'ordre choisi par l'utilisateur: (1) fichiers de données BASIC, (2) accès par secteurs (base d'un DOS), (3) lecteur USB (partage PC/8088 par une commande BASIC `USB ON`/`USB OFF`). Chantier 1 fait ici.
  - Fichiers de données (lib/basic_disk.asm, nouveaux jetons OPEN, CLOSE, WRITE, EOF): `OPEN "f" FOR INPUT|OUTPUT|APPEND AS [#]1` ou `OPEN "I"|"O"|"A",#1,"f"`, `PRINT #1,...`, `WRITE #1,...`, `INPUT #1,v...`, `LINE INPUT #1,a$`, `EOF(1)`, `CLOSE [#1]`. UN SEUL fichier (numéro 1: le pont n'en ouvre qu'un à la fois), donc SAVE/LOAD/MERGE/RUN "f"/KILL/FORMAT donnent `File already open` tant qu'il est ouvert. Fermeture automatique: END, fin de programme, RUN, NEW, CLEAR, SYSTEM (pas STOP, comme GW-BASIC).
  - Mécanisme: `bas_putc` écrit dans un tampon de 32 octets (b_wbuf) quand `b_fout` = 1 (pendant PRINT#/WRITE#; la colonne est échangée pour que TAB( et les zones suivent le fichier; `bas_error` ramène la sortie à la console); vidage vers le pont (`fs_write`) quand il est plein et à la fermeture, l'erreur d'écriture est différée (b_ferr) et signalée à la fin de l'instruction ou à CLOSE. Lecture par blocs de 32 octets (b_rbuf); INPUT# lit une LIGNE du fichier (CR, LF ou CR LF) dans B_IBUF et réutilise inp_field/text_store de INPUT; s'il manque des champs il passe à la ligne suivante. WRITE# écrit les chaînes entre guillemets et les nombres sans espace, séparés par des virgules. Le tokeniseur ne prend plus '#' pour un suffixe de type quand il suit un mot-clé (PRINT#1, INPUT#1, CLOSE#1).
  - Les mots AS, OUTPUT, APPEND ne sont PAS des jetons (comparés en texte): il reste de la place dans les 128 jetons (114 utilisés). Nouvelles erreurs: Bad file number (52), Input past end (62). Variables de l'interpréteur: 87 octets de plus (817 -> 904 sur 1024).
  - Tests (basic_test.py): 30 vérifications de plus (277 en tout), 0 échec. Nouveau: HELP (ligne Files), README (tableau des instructions). Non testé sur le matériel.
  - Chantier 2 (accès par secteurs) fait: commandes du pont 20h-24h (nombre de secteurs, lire un secteur dans un tampon de 512 octets du pont, obtenir / déposer un bloc de 32 octets, écrire le tampon), PING v3 (capacités 07h). Le pont voit toute la flash comme des secteurs de 512 octets (LBA 32 bits, MBR compris; 16384 secteurs pour la W25Q64); il ferme le fichier ouvert avant un accès secteur et remonte le volume FAT (`fsStale`) à la prochaine commande fichier après une écriture, pour que les caches de SdFat ne soient pas périmés. 8088: `fs_sec_info`, `fs_sec_read` (vers ES:DI), `fs_sec_write` (depuis ES:SI) dans lib/bridge.asm; `fs_free` refait sur `fs_cmd4`. BASIC: `DSKREAD lba, adresse` / `DSKWRITE lba, adresse` (nouveaux jetons, 116 sur 128) lisent/écrivent 512 octets à DEF SEG:adresse (LBA 0-65535; DSKREAD protégé comme POKE; interdits si un fichier de données est ouvert). Sert d'outil de mise au point (DSKREAD 0,&HF400 puis PEEK des octets 55h AAh du MBR) et de base à un chargeur / futur DOS.
  - PAS d'INT 13h pour l'instant: tout le micrologiciel (ISR de l'IRQ1, tampons du pont, routines fs_*) suppose SS = VAR_SEG (adressage par BP); un DOS avec sa propre pile devrait d'abord faire adresser ces tampons par un segment explicite. À traiter avec le DOS.
  - BridgeModel (tests) étendu aux secteurs (dictionnaire lba -> 512 octets); 11 vérifications de plus (288 en tout), 0 échec. Non testé sur le matériel.
  - Chantier 3 (lecteur USB) fait, NON VALIDÉ sur le matériel. Choix de l'utilisateur: partage PC/8088 par une commande BASIC. `USB ON` (commande 25h du pont) offre la flash (MBR + volume FAT16, 16384 secteurs) au PC comme lecteur de masse; `USB OFF` (26h) la rend au 8088 (le pont remonte le volume). Tant que USB ON est actif, toutes les commandes disque du 8088 reçoivent « disque non prêt » (Disk not Ready), avec des réponses de la bonne taille (diskBusy). Nouvelles erreurs: état 9 (pile USB sans lecteur de masse) -> Device unavailable (68). Nouveau jeton USB (117/128).
  - Pile USB: le cœur STM32 n'a pas de lecteur de masse composite avec le CDC (seulement HID). Choix: bibliothèque Adafruit TinyUSB (CDC + MSC), dans un ENVIRONNEMENT PlatformIO SÉPARÉ (`blackpill_f411ce_usbdrive`, `-D USE_TINYUSB`); l'environnement par défaut (`blackpill_f411ce`, `default_envs`) reste la pile du cœur, inchangé et éprouvé. Particularités trouvées à la compilation: avec TinyUSB le nom `Serial` est inutilisable (deux macros croisées, `Serial` -> `SerialTinyUSB` -> `Serial`), le croquis passe donc par `UsbSerial` (= `SerialTinyUSB`, sinon `Serial`); `Serial` reste défini (= `Serial1`) pour les messages de SdFat; `yield()` (redéfini par le port TinyUSB pour appeler tud_task) est appelé à chaque tour de loop(); le lecteur de masse est déclaré avant `UsbSerial.begin()` (donc fsMount() passe avant dans setup()). Le port STM32F4 de TinyUSB est récent (le port COM peut changer de numéro).
  - PING v3: capacités 07h (RTC + disque + secteurs), 0Fh avec TinyUSB. Tests: 10 vérifications de plus (298 en tout), 0 échec. Les deux environnements compilent. À valider sur le matériel: énumération (CDC + lecteur), montage du volume sur le PC, USB ON/OFF, écriture depuis le PC puis FILES/LOAD au 8088.
  - Essai matériel de l'environnement usbdrive: le téléversement passe mais ni le port série ni le lecteur n'apparaissent. Cause trouvée en lisant la bibliothèque: `Adafruit_USBD_Device::begin()` (qui démarre le contrôleur USB, `tusb_init`) n'est appelé par personne sur ce cœur (`TinyUSB_Device_Init` n'est pas appelé par le cœur STM32); `Serial.begin()` ne fait qu'ajouter l'interface. Correction: `TinyUSBDevice.begin(0)` explicite dans setup() (avant l'ajout du lecteur de masse, car begin() efface la configuration), puis re-énumération (detach/attach) si le PC a déjà énuméré. À revalider.
* Matériel: CONFIRMÉ (environnement blackpill_f411ce_usbdrive, après la correction `TinyUSBDevice.begin(0)`): le port série et le lecteur « 8088 Disk » apparaissent; `USB ON` -> OK, copie d'un nouveau fichier .bas sur le lecteur depuis le PC -> fonctionnelle, `USB OFF` -> OK, `FILES` au BASIC liste le nouveau fichier. Chantier 3 (lecteur USB) terminé. Non encore validés sur le matériel: fichiers de données (OPEN/PRINT#/INPUT#) et DSKREAD/DSKWRITE.
* Matériel: CONFIRMÉ: fichiers de données (OPEN/PRINT#/WRITE#/LINE INPUT#/EOF/CLOSE: "bonjour 42" et "a,b",5 relus correctement) et DSKREAD 0 (55AA à la fin du MBR). Constat: collé d'un coup, un bloc de 4 lignes avec des instructions disque n'a pas passé (collage en 2 fois nécessaire), et un ':' a été perdu dans une ligne collée (Syntax error). Hypothèse: pendant qu'une ligne exécute des commandes disque (des dizaines de ms), le 8088 ne vide pas son tampon de réception UART (256 octets, sans test de plein: en débordant, la queue rattrape la tête et TOUT le tampon paraît vide) alors que le pont continue d'envoyer le collage à 1 octet/ms. Correction côté pont (les deux environnements): après chaque commande reçue du 8088, envoi des octets UART suspendu 250 ms (`CMD_HOLD_MS`), en plus de la pause de 15 ms après chaque CR. Le ':' perdu seul n'est pas expliqué. À revalider (recoller les 4 lignes d'un coup).
* Matériel: CONFIRMÉ (« fonctionnel »): le collage des 4 lignes d'un coup passe avec CMD_HOLD_MS (250 ms de pause de l'UART après chaque commande du 8088 au pont).
* Demande: rappeler la dernière commande avec la flèche haut, curseur à la fin. Fait (lib/basic.asm): au prompt seulement (`b_hist` = 1 autour de l'appel de `bas_getline` dans `bas_prompt`, donc sans effet dans INPUT), la séquence ESC [ A (ou ESC O A) appelle `hist_recall`: efface à l'écran la saisie en cours (BS, espace, BS) puis affiche la commande mémorisée et range DI à sa fin. `hist_save` mémorise la ligne après chaque saisie au prompt; une ligne vide (Ctrl-C compris) ou de plus de 191 caractères ne remplace pas la précédente. Une seule commande (pas d'historique): `B_HIST` = 0B40h, 192 octets libres entre la pile de valeurs (B_VSTKE) et le programme (B_TXT). HELP: « Up: last cmd ». 9 vérifications de plus (307 en tout), 0 échec. À valider sur le matériel (le terminal doit envoyer ESC [ A pour la flèche haut).
* Demande: `blackpill_f411ce_usbdrive` devient l'environnement PlatformIO PAR DÉFAUT (`default_envs`, platformio.ini); `blackpill_f411ce` (pile du cœur, sans USB ON) reste comme secours. README et ENV.md du pont mis à jour.
* Demande: plan (MAP) de la ROM et espace disponible: `rom_map.py` (aussi `make map`) assemble avec un listing, relit le décalage de chaque module et affiche les zones (adresse physique, taille, %), le détail du BASIC, l'espace libre et un histogramme. Constat (v4.1 + rappel de commande): 39 851 octets utilisés (15,2 %), 222 277 octets (217,1 Ko) libres de C9BABh à FFFEFh, sur 256 Ko; le BASIC occupe 27 875 octets (27,2 Ko).
* Demande: éditer la commande rappelée par la flèche haut (flèches g/d, Inser, Suppr), et ajouter un espace après `?` s'il est omis (?rnd -> ? rnd). Fait (lib/basic.asm, lib/basic_stmt.asm): la flèche haut appelle maintenant `hist_edit`, qui copie B_HIST dans B_IBUF (b_el = b_ec = longueur: curseur à la fin) et saute dans le correcteur de ligne de EDIT (`bas_editbuf`, qui redessine la ligne depuis la colonne 0 avec ESC [ K, donc efface la saisie en cours); son RET rend la main à l'appelant de `bas_getline`. Entrée valide (la ligne éditée est mémorisée par `hist_save`), Ctrl-C annule. Touche Inser (ESC [ 2 ~): nouveau mode écrasement (`b_ovr`, remis à 0 à chaque édition) - disponible aussi dans EDIT n. `?`: le tokeniseur ajoute un espace après le jeton PRINT si le caractère suivant est une lettre (avant, `?rnd` donnait `PRINTRND`, qui ne se relit plus); les guillemets, chiffres et parenthèses restent collés comme avant. 14 vérifications de plus (321 en tout), 0 échec. À valider sur le matériel.
* Demande: « Maintenant, passons à DOS ». Choix de l'utilisateur: un VRAI DOS existant (MS-DOS 2.x ou noyau FreeDOS), en commençant par la COUCHE BIOS + secteur de démarrage. Fait cette étape (NON validé sur le matériel):
  - `lib/isr.asm` (nouveau): `irq1_arduino_handler` sortie de solution-01.asm; elle sauve DS, le charge avec VAR_SEG, et les routines `ps2_rx_push`/`uart_rx_push`/`bridge_rx_push` adressent maintenant les tampons par DS (avant: par SS via BP). L'ISR ne dépend donc plus de la pile ni des segments du programme interrompu (un DOS a les siens).
  - `lib/bios.asm` (nouveau, ~2,5 Ko): INT 13h (CHS 00h/01h/02h/03h/04h/08h/15h + accès étendu 41h/42h/43h/44h/48h; disque 80h = la flash, géométrie 255x63 comme le BPB de SdFat, 2 cylindres pour 8 Mo; DL<80h = 80h, DL>80h = 01h; 04h secteur introuvable/hors disque, 80h pont muet, 0AAh USB ON), INT 19h (MBR -> partition active ou première FAT (types 01/04/06/0B/0C/0E) -> VBR en 0000:7C00, DL=80h, SS:SP=0000:7C00; secteur 0 avec saut EB/E9 = amorce lui-même; retour CF=1 + message sinon), INT 16h STANDARD (UART brut, ESC [ ... = touches étendues; remplace l'ancien INT 16h « esprit BIOS » que personne n'utilisait; PS/2 non géré), INT 1Ah (ticks = centièmes*91/500, heure/date BCD, réglage), INT 11h (0220h), INT 12h (126 Ko), INT 15h (88h), INT 14h/17h (absents), fonctions standard de INT 10h (0Eh, 0Fh, 02h/03h page 0, 06h/07h, 08h, 09h/0Ah; BH=1/2/3 garde l'interface LCD/UART), zone de données 0040:0000, `bios_init` appelée par `setup_bios_interrupts`.
  - Piles: chaque service qui utilise les routines du pont bascule sur une pile privée 1000:FE00-FEFF (`BIOS_ENTER`: sauve DS sur la pile du programme, DS=VAR_SEG, mémorise SS:SP, SS=VAR_SEG), sauve tous les registres dans un cadre (`BIOS_FRAME`), écrit ses résultats dans le cadre, remet CF/ZF dans les indicateurs empilés (`bios_return`). Variables du BIOS en 1000:FCB0-FCCC (hardware.inc).
  - BASIC: `BOOT` (nouveau jeton, 118/128): ferme le fichier de données puis INT 19h; si l'amorce ne démarre pas: `Disk not Ready` (la cause est affichée par INT 19h).
  - Tests: `tests/bios_test.asm`/`.py` (65 vérifications, dans `make test`): interprète de cas exécutés comme un DOS (SS=3000h, DS=2000h, jamais VAR_SEG) sous Unicorn avec l'aiguillage INT du mode réel émulé (Unicorn ne le fait pas: crochet UC_HOOK_INTR), BridgeModel pour le disque/l'horloge; vérifie les registres, la pile intacte, CHS -> LBA, DAP, erreurs, pont muet, USB ON, horloge, clavier, INT 10h/15h, ISR (UART/PS2/réponse/parasite avec une autre pile) et l'amorçage (partition active, première FAT, sans signature, superfloppy, pont muet). basic_test: 2 vérifications de plus (BOOT), 323 en tout. `make map` distingue isr.asm et bios.asm.
  - À venir (pas fait): préparer un volume de démarrage DOS (secteur d'amorce + fichiers système) sur le PC et l'écrire dans la flash par le lecteur USB; choisir MS-DOS 2.x ou FreeDOS; vitesse du disque (~1 Ko/s: réduire l'espace de 1 ms sur les réponses maintenant qu'IBF est câblé); clavier PS/2 complet; minuterie (IRQ0) si le DOS en exige une.
* Matériel: CONFIRMÉ après la couche BIOS et l'ISR indépendante de la pile (DS = VAR_SEG): clavier, BASIC et USB ON/OFF fonctionnent comme avant. Non essayés sur le matériel: BOOT (sur un disque sans amorce: message « no boot signature » puis Disk not Ready) et les INT 13h/16h/1Ah appelés par un vrai DOS.
* Demande: l'utilisateur a copié l'image `pcdos2_1.img` (PC-DOS 2.1, disquette de 180 Ko: 40 cylindres, 1 tête, 9 secteurs; aussi dans le dépôt: breadboard/PC-DOS/pcdos2_1.img) sur le lecteur USB et veut la CHARGER À PARTIR DU MENU. Fait (NON validé sur le matériel), en rendant l'image DISQUETTE A: du DOS:
  - Pont (main.cpp, les 2 environnements; PING capacités 17h, 1Fh avec USB): commandes 27h MONTER (nom -> état + taille), 28h DÉMONTER, 29h LIRE le secteur lba de l'image dans secBuf, 2Ah ÉCRIRE; `imgFile` (File32 O_RDWR, seekSet) indépendant de curFile; fermé avant formatage, écriture directe de secteur, USB ON et remontage du volume; USB ON répond « disque non prêt ».
  - bridge.asm: `fs_img_mount` (DX:CX = taille), `fs_img_umount`, `fs_img_read`/`fs_img_write` (`fs_sec_*` refaits sur `fs_blk_read`/`fs_blk_write`, code d'opération dans BH).
  - bios.asm: INT 13h `DL = 0` = image montée (géométrie d'après la taille: 160/180/320/360/720 Ko, 1,2/1,44 Mo; AH=00/01/02/03/04/05/08/15h/16h; ES:DI = table de paramètres en ROM), fonctions propres AH=F0h MONTER (DS:SI nom; CX:DX taille; erreurs 0E0h+état du pont, 0EFh taille non reconnue) et F1h DÉMONTER; `bios_chs_lba` paramétré (BIOS_GH/GS, contrôle secteur/tête/cylindre); INT 11h dynamique (0221h avec image); INT 19h amorce l'IMAGE (secteur 0, DL=0, sans exiger 55AA) quand une image est montée; vecteur INT 1Eh; `dos_menu`: liste les .IMG de la racine (9 au plus), touche 1-9 / Échap, monte puis INT 19h.
  - Menu principal: option 5 « DOS (boot a disk image) » (LCD: « 4) BASIC  5) DOS »). BASIC: `BOOT "IMAGE.IMG"` (monte puis amorce A:), `BOOT` seul = INT 19h.
  - VALIDATION À L'ÉMULATEUR avec la VRAIE image: PC-DOS 2.1 s'amorce sur cette couche BIOS (IBMBIO/IBMDOS chargées par INT 13h, INT 1Eh de son secteur d'amorce, INT 11h), demande la date puis l'heure (12:34 = la RTC du pont par INT 1Ah), affiche « The IBM Personal Computer DOS Version 2.10 » et `A>`, exécute `VER` et `DIR` (COMMAND COM 17792 octets, etc.). Test dans bios_test.py (90 vérifications; le test PC-DOS n'est exécuté que si l'image existe). Vitesse à prévoir: ~30 Ko de noyau à ~1 Ko/s.
  - Le bandeau BASIC modifié par l'utilisateur (« VE2CUY 86 BASIC Version 1.0 ... UP arrow ») a cassé le filtre du banc (basic_harness.py, basic_test.py): adaptés au nouveau texte. 323 vérifications BASIC, 0 échec.
* Matériel: CONFIRMÉ: PC-DOS 2.1 se charge depuis l'image (`A>ver` -> « IBM Personal Computer DOS Version 2.10 »). Demande: accélérer le chargement. Cause: chaque secteur = 16 blocs de 32 octets de réponse envoyés avec l'espace GAP_US de 1 ms entre octets (~ 0,5 s par secteur). Correction (pont seulement, pas de nouvelle ROM): les RÉPONSES repartent à IBF seul (`REPLY_GAP_US` 20 µs) - IBF est câblé depuis l'étape « pas de collage » - donc au rythme de l'interruption du 8088 (~ 3 à 6 Ko/s attendus, 3 à 6 fois plus vite). Le clavier et l'UART gardent GAP_US. Sans IBF (USE_IBF 0) les réponses gardent 1 ms. À mesurer sur le matériel; si ce n'est pas assez: lecture par scrutation (sans interruption) pendant un secteur, ou blocs plus grands (tampon de réponses du 8088 de 64 octets).
* Demande: quitter le DOS et revenir au menu sans reset. Fait (ROM, NON validé sur le matériel): l'octet UART Ctrl-\ (1Ch, `WARM_RESET_KEY`) est intercepté par `irq1_arduino_handler` (lib/isr.asm): EOI puis `jmp 0C000h:0000h` (même saut que le vecteur de reset FFFF0h): redémarrage complet (start: efface la RAM, réinitialise 8255/8259), menu principal, quoi que fasse le 8088 (DOS, programme bloqué...). Non transmis aux programmes; l'IRQ1 ne doit pas être masquée par le programme (PC-DOS 2.1 n'y touche pas). Les messages d'amorçage (INT 19h) rappellent « Ctrl-\ = back to the menu ». bios_test.py: 93 vérifications (octets ordinaires rangés, Ctrl-\ redémarre sans ranger l'octet, 1Ch du clavier PS/2 = scan code ordinaire). Crochet de code sur 0C000h:0000h ajouté au banc.
* Demande: sous DOS l'heure vient de la RTC mais pas la date (PC-DOS 2.1 propose 1-01-1980: pas d'horloge, il demande la date puis l'heure au démarrage). Fait (ROM, NON validé sur le matériel): `bios_mkdate` (INT 19h) lit la RTC et prépare "MM-JJ-AAAA" CR (BIOS_DATESTR) et CR (BIOS_TIMESTR); `bios_prompt_watch` (appelée par INT 10h AH=0Eh, pour chaque caractère du DOS) détecte « new date » … « : » et « new time » … « : » (détecteurs d'états BIOS_MSTATE/BIOS_TSTATE) et arme BIOS_INJ_PTR; `bios_trykey`/`bios_key` (INT 16h) livrent les touches injectées AVANT une touche déjà en attente (BIOS_KSRC distingue la source: on avance dans la chaîne au lieu de vider BIOS_KEYF_OFF). L'heure est acceptée par Entrée (elle vient déjà de la RTC par INT 1Ah). INT 1Ah AH=00h: indicateur de minuit (ticks plus petits que la lecture précédente -> AL = 1). Vérifié à l'émulateur avec la vraie image: aucune touche tapée, puis `DATE` affiche « Current date is Sun  9-20-2026 » (RTC du modèle). bios_test.py: 105 vérifications. (Correction de doc: un remplacement du README avait supprimé le paragraphe « Amorcer un DOS depuis une image »; rétabli.)
* Demande: obtenir le numéro de l'interruption dans « *** Interruption non implementee *** » (messages vus avec certaines commandes de DOS 2.1 et avec l'image de DOS 3.3). Cause: un SEUL gestionnaire générique était installé sur les 256 vecteurs, sans moyen de savoir lequel l'avait appelé. Fait (ROM): chaque vecteur a SON petit gestionnaire (`int_stubs` dans lib/bios.asm: `push ax / mov al, n / jmp near int_not_implemented`, 6 octets, 1,5 Ko) et le message devient « *** Interruption non implementee: INT 15h, AH=86h, appelee depuis 0070:1A2B *** » (numéro, fonction AH de l'appelant, adresse de l'appelant); retour par IRET, registres/pile/segments intacts. `init_ivt_not_implemented` et `int_not_implemented` déplacées de solution-01.asm vers lib/bios.asm. Menu IVT (Memory functions): les vecteurs du BIOS ne sont plus étiquetés « non implementee » (« gestionnaire installe (BIOS / DOS) »). Piste probable pour DOS 2.1: BASIC.COM/BASICA.COM appellent le BASIC en ROM du PC IBM par INT 18h (absent ici). À l'émulateur, ver/dir/chkdsk/date/time/mode/type/format de PC-DOS 2.1 n'ont déclenché AUCUNE interruption non implémentée. bios_test.py: 108 vérifications.
* Demande: MS-DOS 3.30 (image `Dos33-d1.IMG`) échoue SUR LE MATÉRIEL seulement (à l'émulateur il arrive à `A>`, même avec ROM protégée en écriture et ports à 0FFh): `*** Interruption non implementee: INT E0h/CDh, AH=A0h, appelee depuis 1D7D:0A56/0A5A/0A5E ***`, un `▒`, `)))` puis « Bad or missing Command Interpreter ». Ces adresses sont dans la zone haute où le SYSINIT de DOS 3.3 se déplace: du code corrompu s'exécute, donc des octets lus sont perdus ou altérés (soupçon: réponses à 20 µs, ajoutées juste avant). Diagnostic + protection (ROM ET pont à mettre à jour ensemble): commande 2Bh du pont (somme 16 bits de secBuf), `fs_blk_read` somme les 512 octets reçus et rend FSE_BADSUM (10) si elle diffère, `bios_xfer` relit le secteur (3 essais, `BIOS_TRY`), affiche `!` par relecture (`BIOS_SHOW_RETRY`), compte dans `BIOS_BADSUM` (FBF2h), puis AH=20h; BASIC: FSE_BADSUM -> Disk I/O error. `int_not_implemented` affiche en plus « , code xx xx ... » (les 8 octets qui précèdent l'adresse de retour). bios_test.py: 114 vérifications (octet altéré -> relu, 3 sommes fausses -> AH=20h, image idem, code affiché). Si des `!` apparaissent: les réponses rapides sont en cause (augmenter REPLY_GAP_US); sinon, la cause est ailleurs (le message montrera les octets de code). À valider sur le matériel.
* Matériel (DOS 3.30, ROM + pont avec sommes de contrôle): AUCUN `!` -> les lectures de secteurs sont justes (somme égale): les réponses rapides du pont ne sont pas en cause. Le message a montré chaque fois deux interruptions de suite depuis la même adresse (INT E0h puis INT CDh, appelant 1D7D:0A56, 0A5A, 0A5E) et un `▒`, mais les octets « code » sont sortis VIDES. Cause (bogue du diagnostic): `uart_tx_hex_byte` lit sa table de chiffres par DS (`[hex_table + bx]`); la boucle des octets de code gardait DS = segment de l'appelant, donc la table lue était la RAM du DOS (zéros). Corrigé: DS = segment de l'appelant seulement le temps de `lodsb`, DS = CS pendant l'affichage (DX sauvé). Le test précédent ne le voyait pas (appelant dans le segment de la ROM); nouveau test: l'INT part d'un secteur d'amorce en RAM (0000:7C06) et les 8 octets EB 00 B4 A0 CD 60 sont attendus (rouge avec l'ancien code: octets 00). bios_test.py: 115 vérifications. À rejouer sur le matériel pour LIRE les octets du code exécuté en 1D7D:0A56.
* Matériel (DOS 3.30, octets « code » enfin lisibles): en 1D7D:0A4E: `06 B0 FF BA F2 02 EE 42 | EE 42 EE 42 ...` = `push es / mov al,0FFh / mov dx,2F2h / out dx,al / inc dx / out dx,al ...`: du VRAI code de IO.SYS (trouvé dans l'image en 0x597D, fichier IO.SYS), pas de la corruption. Il écrit 0FFh sur les ports 2F2h-2F7h (deux suites: 2F2h... puis, seulement sur PS/2, 2F6h...). Sur un PC ces ports n'existent pas; ici le 8255 est sélectionné par A7 seul (IO.A7), donc 2F2h=port C, 2F3h=REGISTRE DE MODE (0FFh: reprogrammation du 8255 en plein amorçage), 2F4h=port A (octet 0FFh vers le pont), 2F5h=port B...: le pont est perdu, INTR parasites, vecteurs bidon (E0h, CDh) -> d'où les interruptions non implémentées répétées deux par deux à chaque OUT, et le `▒`. Le 8255 n'a rien à voir avec les lectures de secteurs (aucun `!`). Correction logicielle (ROM seulement): `bios_patch_sector` (lib/bios.asm) appelée après chaque secteur LU par INT 13h: cherche `BA F2 02|06 EE` puis la suite d'octets `EE`/`42` (au plus 16) et remplace chaque `EE` (OUT DX,AL) par `90` (NOP); ignore un motif à cheval sur la fin du secteur; `+` sur l'UART par OUT neutralisé (`BIOS_SHOW_PATCH`), compteur `BIOS_NPATCH` (FBF4h). Le banc journalise maintenant les OUT vers des ports autres que 20h/21h/80h-83h (`badports`): à l'émulateur, MS-DOS 3.30 sans correctif écrit exactement sur 2F2h-2F7h; avec: aucun port parasite, 22 `+` (11 OUT, deux lectures d'IO.SYS), `Version 3.30` affichée, aucune interruption non implémentée. bios_test.py: 119 vérifications (motif, leurres, motif tronqué, image réelle DOS 3.30). Remède matériel possible: décoder toutes les lignes d'adresse d'E/S. À valider sur le matériel.
* Matériel (DOS 3.30 avec le correctif des OUT): les 22 `+` apparaissent (11 OUT neutralisés à chacune des deux lectures d'IO.SYS), puis: « Current date is MS-DOS Version 0.6656 » (le jour de la semaine est remplacé par le texte de VER: du code ou des données de la partie transitoire de COMMAND.COM ne sont pas ce qu'ils devraient être), « Invalid COMMAND.COM », « Insert disk with \COMMAND.COM in drive A ». À l'émulateur la même image affiche « Current date is Sun  9-20-2026 » puis l'invite de date. Pistes testées à l'émulateur, TOUTES SANS EFFET: dates de la RTC (2026-9-21, 2026-9-20 23:59:59, 2000-1-1 -> DOS retombe sur 1980), lecture des ports (le DOS ne lit AUCUN port sauf notre 8255), accès mémoire au-delà de 128 Ko (aucun), disque dur 80h avec MBR + partition FAT16 type 04 ou 06 (DOS 3.30 la voit: INT 13h AH=08/02 sur 80h/81h, ES 095F -> 0964, mais démarre quand même). Outil de diagnostic ajouté: `make trace` (ou `nasm -dBIOS_TRACE=1`) -> rom_trace.bin, ROM identique mais chaque INT 13h et 1Ah écrit sur l'UART `<nn AX BX CX DX ES-AX CF>` (entrée puis sortie; nn = numéro de l'INT). Comparer la trace du MATÉRIEL à celle de l'émulateur (`TRACE=1 FULL=1 dosint.py`): la première ligne qui diffère (registres d'entrée = ce que le DOS a demandé, AX de sortie = ce que le BIOS a répondu) montre où le DOS suit un autre chemin. bios_test.py accepte `TRACE=1` (variable d'environnement) pour compiler avec la trace; 119 vérifications avec la trace éteinte (par défaut).
* Matériel, PREMIÈRE TRACE (rom_trace.bin, DOS 3.30): la séquence d'appels INT 13h/1Ah vue par le matériel est IDENTIQUE à celle de l'émulateur (avec un disque dur 80h simulé) jusqu'à « Current date is »: mêmes fonctions, mêmes secteurs, mêmes AX de sortie (aucune erreur, aucun `!`); seuls diffèrent l'heure (15:06:07) et l'emplacement de la partition de la flash (1re partition en C0 H2 S34). Ensuite, à l'émulateur: un seul INT 1Ah AH=00 puis « Sun  9-20-2026 »; sur le matériel: « MS-DOS Version 0.6656 » puis des CENTAINES d'INT 1Ah AH=00 identiques (mêmes registres BX=0306 CX=0006 DX=0000, appelant en 0070:0B61 = lecture d'horloge de IO.SYS: `int 1Ah / or al,al / inc [DAYCNT] / conversion des ticks (x5, / 0E90Bh)`), jusqu'à Ctrl-C. Puis « Invalid COMMAND.COM » (rechargement de la partie transitoire depuis le disque: échec de la vérification). La trace étendue affiche maintenant AX CX DX de SORTIE et, pour INT 1Ah, les 8 octets bruts de la RTC (`R:` annee lo/hi, mois, jour, h, min, s, cs): à comparer avec l'émulateur (ticks attendus 000F 1930 pour 15:06:07). À rejouer sur le matériel.
* Matériel, TRACE COMPLÈTE (DOS 3.30): la RTC du pont est JUSTE (octets bruts EA07 09 15 0F 1C 38 49 = 2026-09-21 15:28:56,73; ticks 000F 7A88 = 15:28:56 x 18,2; AL=0 (pas de minuit)) et la séquence INT 13h/1Ah est identique à l'émulateur. Après « Current date is »: 1 appel d'horloge (BX=0306 CX=0006 DX=0000), le texte « MS-DOS Version 0.6656 » (AX=1A00 = 6656 décimal lu comme version: une fonction du DOS rend un AX bidon), puis des appels d'horloge répétés (un tour = ~0,6 s à cause de la trace). B61 (IO.SYS) = lecture d'horloge du pilote CLOCK$: `int 1Ah / or al,al / inc [DAYCNT] / ticks x5 / 0E90Bh -> jours, minutes, secondes, centièmes`; la boucle est plus haut, dans le noyau. Les entrées de l'init (date 2026 0921 BCD) sont les mêmes qu'à l'émulateur, donc la divergence est dans le DOS lui-même: contenu de la RAM ou comportement du vrai 8088 (décalages, DIV, préfixes de segment + REP interrompus, file de prélecture...). Expérience ajoutée à la ROM de trace: au 5e appel INT 1Ah AH=00 de signature BX=0306 CX=0006 DX=0000 (la lecture de l'heure de « Current date is », même point sur le banc et le matériel) `bios_memmap` écrit la carte de la RAM 128 Ko: 32 lignes `Mbbbb: s ... ` (16 blocs de 256 octets par ligne; s = rol(s,1) xor mot); carte du banc dans le dossier de travail (emu_map.txt). Comparer bloc à bloc: blocs différents = mémoire fausse sur le matériel (on ira voir ces blocs); blocs identiques = comportement du processeur.
* Matériel, CARTE MÉMOIRE (DOS 3.30) comparée à celle du banc (32 lignes de 16 sommes par 256 octets, même point du programme: 5e appel d'horloge après « Current date is »): 252 blocs sur 512 diffèrent, dont 6 seulement dépendent de l'heure (deux exécutions du banc). Deux familles: (1) la RAM libre 10000h-1AFFFh (83 blocs contigus dès 13900h) et 1FD00h-1FFFFh est NON NULLE sur le matériel (restes de BASIC / du test de RAM), nulle sur le banc; un remplissage aléatoire de la RAM du banc (GARBAGE=n dans bios_test.py) NE reproduit PAS l'échec; (2) les zones de tampons/tables de disque du DOS (9E00h-A4FFh, E900h-F6FFh, 1D300h-1E0FFh, IO.SYS 600h-AFFh) diffèrent: sur le matériel DOS 3.30 monte la flash comme DISQUE DUR C: (partition lue en C0 H2 S34 = LBA 159), sur le banc c'est mon faux disque (MBR + FAT16 type 04 de 63 à 16383, BPB inventé). PC-DOS 2.1 ignore les disques durs et démarre. Hypothèse suivante: le montage de C: (BPB réel de SdFat) perturbe DOS 3.30. Test prêt: `make trace-nohd` -> rom_trace_nohd.bin = ROM de trace dont INT 13h refuse DL >= 80h (`BIOS_HIDE_HD`, AH=01 CF=1: le DOS ne voit aucun disque dur; F0h/F1h de montage d'image exceptés). Au banc: le DOS saute alors les lectures du MBR et arrive à « Current date is Mon 9-21-2026 » (HIDEHD=1 dans bios_test.py). À essayer sur le matériel; en parallèle demander à l'utilisateur le MBR et le secteur de démarrage de la partition de la flash (petit programme BASIC DSKREAD) pour reproduire son disque exact au banc.
* DIAGNOSTIC MATÉRIEL (RAM): l'utilisateur a relevé le BPB/MBR de la flash (partition type 04 en LBA 159, 16225 secteurs, BPB SdFat avec total 16 bits = 0, secteurs/piste = 0, têtes = 0); reproduits à l'identique au banc (hdreal.py), DOS 3.30 y démarre TOUJOURS: les appels INT 13h/1Ah du matériel sont identiques (y compris les valeurs de sortie) donc le BIOS n'est pas en cause. Sondes BASIC (attention: &H8000-&HFFFF sont négatifs en BASIC, une boucle FOR jusqu'à &H9000 ne fait qu'un tour): après mise sous tension, SANS DOS, la RAM haute (10000h-1FFFFh) contient un octet non nul par bloc de 256 octets, à l'offset FFh (valeurs stables d'une mise sous tension à l'autre: 34 AA C9 60 D8 8D 42 52 03 40 42 pour les blocs 13Ah-144h; ce sont les octets de poids fort des sommes de la carte mémoire prise pendant le DOS). POKE 0 sur ces octets ne les change pas; test de toutes les valeurs 0-255 aux offsets 250-255 du bloc 13A00h: SEULE l'écriture de 00h à l'adresse finissant par FFh échoue (lu 52h); toutes les autres valeurs et les offsets 250-254 passent. Cas extrême du bus multiplexé du 8088 (AD0-7 = FFh pendant la phase d'adresse puis 00h pendant les données: 8 lignes qui basculent ensemble): rebond de masse, verrou 74HC373/ALE, temps d'accès de la RAM. Le test de RAM du menu ne le voyait pas: `test_segment` n'écrivait que AAh et 55h (puis restaurait l'octet). Correction: motifs 00h et FFh ajoutés (4 motifs; durée x2; le rapport d'erreur donne adresse, attendu et lu). À faire sur le matériel: relancer le test de RAM (ROM normale), tester la RAM basse par BASIC (DEF SEG=&H500), découpler (100 nF près du 8088, 74HC373, transceiveur, RAM), raccourcir les masses, baisser l'horloge pour voir si le défaut disparaît. Ce défaut expliquerait l'échec de DOS 3.30 (les zéros écrits à xxFFh ne sont pas pris).
* DÉFAUT MATÉRIEL LOCALISÉ (RAM = une seule puce HM628128, 128 Ko): scan complet des 256 valeurs sur les offsets 0-249 du bloc 13A00h: AUCUNE erreur; RAM basse (DEF SEG=&H500) offset 250-255: AUCUNE erreur; RAM haute offsets 250-254: aucune erreur; SEUL échec: écrire 00h à une adresse haute finissant par FFh. Test d'atterrissage (`DEF SEG=&H300:POKE &HA00,17:POKE &HAFF,&H77 / DEF SEG=&H13A0:POKE 0,34:POKE 255,0 / DEF SEG=&H300:PRINT PEEK(&HA00);PEEK(&HAFF)`) -> `17 0`: les deux moitiés sont indépendantes (17 intact), et l'écriture de 00h en 13AFFh est allée en 03AFFh (0 au lieu de 77h): la ligne A16 (verrouillée par ALE, multiplexée avec S3 sur le 8088) DÉCROCHE de 1 à 0 quand les 8 lignes AD0-7 passent ensemble de FFh (adresse) à 00h (données). Conséquences: tout 00h écrit en 1xxFFh est perdu ET écrit en 0xxFFh (corruption silencieuse de la moitié basse: DOS 3.30, qui écrit beaucoup de zéros dans la RAM haute, échoue; PC-DOS 2.1, plus petit, passe); le test de RAM d'origine (AAh/55h seulement, octet restauré) ne le voyait pas. Correction logicielle faite: 4 motifs (AAh, 55h, 00h, FFh). Aucune correction logicielle sûre pour un DOS. Pistes matériel: découplage 100 nF au verrou de A16-A19 et à la HM628128, masse courte/épaisse, trajet et soudures de A16, LE/ALE du verrou; boucle d'écriture (`10 DEF SEG=&H13A0:20 POKE 255,0:30 GOTO 20`) pour observer A16 à l'oscilloscope, déclenché sur /WE. Après réparation: relancer le test de RAM du menu (ROM normale) puis DOS 3.30.
* Demande: sur la ligne du test de RAM (ex. "1000:EC00-1000:EFFF"), afficher aussi l'adresse en binaire; a la fin du test, afficher la quantite totale de memoire defectueuse ("TOTAL DEFAUT: HEX, DEC"). Fait (solution-01.asm, lib/uart.asm, include/hardware.inc), utile pour le diagnostic materiel en cours (le defaut trouve touche A16 - voir plus haut): chaque ligne UART de msg_bloc_progression affiche desormais l'adresse PHYSIQUE de debut du bloc en binaire (21 caracteres: le nibble de poids fort - bits 19-16, dont A16 - puis les 16 bits de poids faible), via deux nouvelles routines lib/uart.asm: `uart_tx_bin20` (DX:AX physique -> binaire, reutilise `uart_tx_bin_word` pour les 16 bits de poids faible) et `uart_tx_dec_word` (AX 0-65535 -> decimal sans zero de tete, chiffres empiles poids faible d'abord puis depiles: sortent naturellement dans le bon ordre). Nouvelle variable `RAM_DEFECT_BYTES` (mot, 0FBFAh, meme zone que BIOS_TRY et consorts: fin du tampon d'edition, non testee par test_ram) remise a zero au debut de test_ram, incrementee une fois par octet defectueux dans `msg_defaut_detail` (donc par octet, pas par motif ni par bloc); `msg_ram_total_defauts` (nouvelle routine) affiche "TOTAL DEFAUT: <hex>h, <dec> octet(s)" a la fin du test, dans les deux cas (RAM OK ou defectueuse). Non ajoute au LCD (pas de place sur 20 colonnes). Verifie: make check/check-modules + build TEST_PS2 + make test (bios_test 119, basic_test 323, 0 echec) + un modele Python independant de uart_tx_bin20/uart_tx_dec_word/mem_calc_physical (memes calculs que l'assembleur, valeurs attendues confirmees, ex. 1000:EC00 -> physique 1EC00h -> "0001 1110110000000000"). Pas de banc Unicorn pour test_ram lui-meme (menu interactif de solution-01.asm, hors du cadre de bios_test.py/basic_test.py - meme situation que le changement precedent des motifs 00h/FFh). A valider sur le materiel.
* CORRECTION (regression introduite par l'ajout de l'adresse binaire ci-dessus, trouvee sur le materiel par l'utilisateur - « le test tourne en rond, il n'atteint jamais le deuxieme bloc de 64K », puis « RAM OK » affiche malgre des dizaines de DEFAUT): msg_bloc_progression appelait `mem_calc_physical` (detruit CX, documente) et `uart_tx_bin20`/`uart_tx_bin_word` (detruit BX: 16x `shl bx,1` -> BX = 0 A LA SORTIE, TOUJOURS) sans les proteger, alors que test_segment/test_ram utilisent CX et BH comme ETAT VIVANT (pas des variables memoire) a travers TOUTE la boucle: CX = compteur du `loop .byte_loop` (ecrase a 0 a chaque bloc -> le segment 0000h reboucle indefiniment: DI progresse normalement en parallele et finit par deborder de FFFFh a 0000h, d'ou les blocs qui semblent recommencer sans jamais passer au segment 1000h) et BH = drapeau GLOBAL « RAM defectueuse » (efface au DERNIER bloc du test, quel que soit son contenu -> `*** RAM OK ***` affiche meme avec des defauts, alors que `TOTAL DEFAUT` - lui en RAM, jamais touche par ce bogue - restait juste). Corrige: `push cx`/`pop cx` autour de `call mem_calc_physical`, `push bx`/`pop bx` autour de tout le nouveau bloc. Verifie a l'emulateur (nouveau: demarrage complet depuis `start:`, IVT emulee par UC_HOOK_INTR, touche '1' injectee dans UART_BUF des que ps2_get_char attend, dans le dossier de travail): le test atteint desormais bien `1000:0000-1000:03FF` (jamais le cas avec le bogue CX) et se termine par `*** RAM OK ***` sur une RAM emulee (parfaite); confirmation isolee du mecanisme de chaque bogue par execution directe d'extraits de code (uart_tx_bin_word laisse toujours BX=0; le bloc corrige preserve bien BH=1 a travers l'appel). make check/check-modules/PS2 + make test (119 BIOS, 323 BASIC, 0 echec).
* Matériel, PREMIER RAPPORT FIABLE (apres les 2 corrections ci-dessus): RAM DEFECTUEUSE, TOTAL DEFAUT 00F7h (247 octets). Profil inchange par rapport aux essais precedents: segment 0000h 100% propre (64 blocs OK), segment 1000h quasiment CHAQUE fenetre de 256 octets echoue a l'ecriture de 00h a son dernier octet (xxFFh) - le defaut A16 deja localise. Deux ecarts mineurs d'une execution a l'autre (1000:09FF passe cette fois, 1000:0BFF lit 45h au lieu de 55h): compatible avec une marge de synchronisation plutot qu'une panne franche. Les condensateurs de decouplage essayes hier soir n'ont pas regle le probleme (deja etabli); les autres pistes (filtre RC sur IC-03 broche 6, condensateur sur ALE, remplacement de IC-03) restent a essayer et a rapporter.
* Demande: retirer l'injection automatique de la date/heure aux invites du DOS (« Enter new date: »/« Enter new time: ») - posait probleme avec certains DOS (chaine injectee acceptee a un moment ou le curseur ne l'attendait pas, donnant une date invalide). Fait (lib/bios.asm): supprime `bios_prompt_watch`/`bios_watch1`/`bios_pat_date`/`bios_pat_time`/`bios_mkdate`/`bios_put2` et leurs appels (INT 19h `call bios_mkdate`, INT 10h AH=0Eh `call bios_prompt_watch`), ainsi que la priorite des touches injectees dans `bios_trykey`/`bios_key` (BIOS_INJ_PTR/BIOS_KSRC); ces variables et BIOS_MSTATE/BIOS_TSTATE/BIOS_DATESTR/BIOS_TIMESTR retirees de hardware.inc (BIOS_LASTTICK conserve: sert au seul indicateur de minuit de INT 1Ah, sans rapport). Les invites du DOS attendent desormais une vraie saisie au clavier, comme sur un PC reel. tests/bios_test.py: retire les 9 verifications de l'injection (motifs, priorite, cas sans date preparee), les 2 tests d'integration PC-DOS 2.1/MS-DOS 3.30 tapent maintenant la date (09-20-2026 + Entree x2) dans leur `uart_in` au lieu de compter sur l'injection. 110 verifications (au lieu de 119: -9 supprimees). make check/check-modules/PS2 + bios_test.py tous OK. README mis a jour (section Date et heure du DOS). A valider sur le materiel: PC-DOS 2.1 et MS-DOS 3.30 doivent maintenant demander et ATTENDRE la date/l'heure au clavier au demarrage.
* Demande: reorganiser le menu principal en 4 sous-menus - "=== VE2CUY PCx86 ===": 1) Basic (Tiny Basic, BASIC), 2) Memory functions (+ Test RAM ajoute), 3) USB Disk (USB ON/OFF, List files, Boot disk image), 4) Configuration (Clock speed, a venir). Choix de l'utilisateur pour USB ON/OFF: bascule automatique (un seul etat memorise, pas de sous-sous-menu). Fait (solution-01.asm):
  - `.main_menu` n'aiguille plus que vers 4 sous-menus (`.basic_menu`, `.dump_menu`, `.usb_menu`, `.config_menu`); chacun revient au menu principal sur Echap (jamais directement d'une action imbriquee), meme motif qu'avant pour Memory functions/dos_menu.
  - `.basic_menu` (nouveau): Tiny Basic et BASIC (ex-options 3/4 du menu principal), sans pagination LCD (2 options).
  - `.dump_menu` (Memory functions): 6e option "Test RAM" ajoutee (ex-option 1 du menu principal), en fin de liste; repagine LCD (page 2 = options 5-6 au lieu de 5 seule).
  - `.usb_menu` (nouveau): "1) USB ON/OFF" (`usb_toggle_action`, nouvelle routine: bascule BIOS_USB_STATE - hardware.inc, nouvel octet 0FCE8h, reutilise le slot libere par BIOS_INJ_PTR - envoie FS_USB_ON/OFF au pont, FSE_NOSUPPORT distingue "pont sans lecteur de masse"), "2) List files" (`list_files_action`, nouvelle routine: fs_dir_first/fs_dir_next/fs_free + put_udec32 de lib/basic_disk.asm reutilises DIRECTEMENT, sans passer par BASIC - bas_puts/ERROR y ajoutent un etat qui n'existe pas ici; meme motif DS/ES=VAR_SEG que dos_menu, bios_puts pour le texte ROM, bios_puts_ds pour les tampons RAM - piege trouve et corrige AVANT tout essai: bios_puts_ds utilise DS, pas bios_puts, pour le texte ROM une fois DS=VAR_SEG), "3) Boot disk image" (= dos_menu, ex-option 5 du menu principal, inchangee).
  - `.config_menu` (nouveau): "1) Clock speed" - pas encore implemente, affiche seulement un message ("a venir").
  - Textes UART/LCD mis a jour (txt_menu_main/basic/dump/usb/config, lcd_txt_menu_main_l1-4 et nouveaux lcd_txt_menu_basic/usb/config/dump_l6); README.md (section Menu interactif + references eparpillees a "option N du menu principal").
  - Verifie: make check/check-modules/PS2 + make test (bios_test/basic_test inchanges, aucune regression - le menu du moniteur n'est couvert par aucun des deux). Nouveau: banc Unicorn de navigation dans le dossier de travail (demarrage complet depuis `start:`, IVT emulee par UC_HOOK_INTR, injection INCREMENTALE des touches - un octet a la fois, seulement quand le tampon UART est vide ET le CPU est revenu a ps2_get_char.loop - necessaire pour Echap: sinon la touche suivante, deja disponible, est prise pour le debut d'une sequence ANSI par uart_get_key/uart_wait_byte et les deux sont perdues, piege trouve par un premier essai rate). Verifie: les 4 sous-menus s'affichent, Echap revient au menu principal depuis chacun, "6) Test RAM" est bien liste, usb_toggle_action et list_files_action affichent leurs messages initiaux corrects (le reste - vrai echange avec le pont - n'est testable qu'au materiel, comme dos_menu). A valider sur le materiel.
* Demande: identifier l'etat USB courant dans "1) USB ON/OFF" du sous-menu USB Disk. Fait: l'option elle-meme montre l'etat ("1) USB: OFF"/"1) USB: ON", nouvelle routine `usb_state_print`, lit BIOS_USB_STATE), sur l'UART et le LCD, redessinee a chaque passage dans le sous-menu (donc a jour tout de suite apres une bascule). txt_menu_usb scinde en txt_menu_usb_head/txt_menu_usb_rest (l'option 1 est generee entre les deux, dynamique - pas dans le texte fixe); lcd_txt_menu_usb_l1 retiree (generee dynamiquement, ligne 0 du LCD). Verifie: make check/check-modules/PS2 + 2 bancs Unicorn dans le dossier de travail (etat par defaut OFF a l'ouverture; etat ON reflete apres bascule - simulee en RAM, faute de vrai pont dans l'emulateur) + make test (aucune regression). README mis a jour.
* Demande: dans Edit RAM (sous-menu Memory functions), demander l'adresse de depart COMPLETE sur 20 bits (segment:offset, ex. 0x1000:0000) plutot que seulement 16 bits (offset, segment TOUJOURS 0000h implicite - la RAM haute, VAR_SEG/1000h, etait inaccessible depuis ce menu). Fait (solution-01.asm, hardware.inc):
  - Nouvelle variable `EDIT_BASE_SEG_OFF` (mot, 0FCF0h - reutilise le slot libere par l'ancien BIOS_DATESTR).
  - `edit_ram_action`: la saisie "Address: 0x" devient 2 champs (segment puis offset), meme mecanique a 2 champs que dump_memory_action (Start:/End:) - reutilise directement `txt_dump_seg_off_sep` (":0x") de dump_memory_action.
  - Protection de l'IVT (offset < EDIT_MIN_START = 0400h rejete) rendue SPECIFIQUE au segment 0000h (l'IVT ne vit qu'a 0000:0000-0000:03FF; un offset < 0400h dans un AUTRE segment n'a rien a voir avec elle et n'est plus rejete).
  - `edit_ram_load_buffer`/`edit_ram_commit_buffer`: ES lu dynamiquement depuis EDIT_BASE_SEG_OFF au lieu du xor ax,ax/mov es,ax fixe (segment 0000h) code en dur.
  - `edit_run_load_buffer`/`edit_run_commit_buffer` (edit_run_action, adresse fixe 1000:0000): INCHANGEES - routines separees, deja codees en dur sur VAR_SEG, ne lisent jamais EDIT_BASE_SEG_OFF.
  - Grille d'affichage (LCD ET terminal, par ligne) INCHANGEE: continue de montrer seulement l'offset ("OOOO:"), le segment choisi etant deja visible a l'ecran au moment de la saisie (echo) - pas de place sur le LCD (20 colonnes, deja calees au pixel pres - voir Directives.md pour le bug materiel deja corrige a ce sujet) pour l'ajouter sans tout redecaler.
  - Verifie: make check/check-modules/PS2 + 4 bancs Unicorn dans le dossier de travail (edition reussie dans 1000h - ecrit puis relit AB a 1000:0010; regression segment 0000h - CD a 0000:0500; protection IVT toujours active en 0000h - compare a un boot temoin plutot qu'a une valeur supposee, l'IVT n'etant jamais a zero apres le demarrage; le MEME offset dans un AUTRE segment n'est PAS rejete - EF a 1000:0100) + make test (aucune regression). README mis a jour (Edit RAM, Edit+Run RAM).
* Demande: pourquoi DOS 5 (Dos50-d1.img, dans breadboard/PC-DOS/) ne charge pas. Diagnostic a l'emulateur (Unicorn, scripts dans le dossier de travail): le demarrage n'echoue pas et n'affiche aucune erreur - il BOUCLE INDEFINIMENT pendant SYSINIT, bien avant COMMAND.COM (aucun progres entre 600 millions et 2 milliards d'instructions simulees). Localise precisement: boucle a CS:IP ~0FFCh:0BC1Fh-0BC42h (36 octets, visites >24 millions de fois), qui balaie en arriere (ES=06C7h, depart 40BFh, pas de 8) une pretendue table de drapeaux, cherchant un octet a 0, avec une limite d'arret (0001h) mathematiquement INATTEIGNABLE vu le pas (40BFh mod 8 = 7, jamais egal a 1: la boucle ne peut PAS se terminer naturellement une fois entree). Les octets balayes ne ressemblent pas a une petite table d'etat (valeurs quelconques, plutot du code/des donnees) - suggere un pointeur mal calcule en amont. L'utilisateur a confirme la cause: la documentation de PC-DOS 5.0 exige AU MOINS 256 Ko de RAM; ce materiel n'en a que 128 Ko (126 Ko annonces par INT 12h) - tres probablement une table interne de SYSINIT dimensionnee/placee a partir de la memoire disponible, qui deborde/est mal calculee avec si peu de RAM. PC-DOS 2.1 et MS-DOS 3.30 (initialisation plus simple, pas de cette exigence) s'amorcent normalement sur ce materiel. CONCLUSION: PAS un bogue du firmware - limite materielle (128 Ko de RAM, en dessous du minimum de DOS 5.0+). README mis a jour (section Limites): DOS 5.0+ documente comme non supporte, avec l'explication. Rien a corriger dans le code.
* Demande: dans Edit+Run RAM, remplacer le programme de depart par defaut (B8 34 12 CB = "mov ax,1234h"/"retf") par "inc ax"/"inc cx"/"mul cx"/"add bx,2"/"retf" (40 41 F7 E1 83 C3 02 CB, 8 octets). Fait (solution-01.asm): `edit_run_default_code` mis a jour; sa longueur (`edit_run_default_code_len equ $ - edit_run_default_code`) est calculee automatiquement, aucun autre endroit n'en dependait (copie par boucle CX = edit_run_default_code_len). Verifie: make check/check-modules/PS2 + 1 banc Unicorn dans le dossier de travail (2) Memory functions, 4) Edit+Run RAM, r: 1re execution avec les registres persistants a 0 -> AX=1 BX=2 CX=1 DX=0 (conforme: inc ax, inc cx, mul cx = 1*1=1, add bx,2); 2e 'r' (registres persistants d'une execution a l'autre) -> AX=4 BX=4 CX=2 DX=0, confirmant la croissance cumulative). Rien dans tests/bios_test.py ou basic_test.py ne reference ce programme (menu interactif hors de leur portee, comme le reste du moniteur).
* NOTE: le depot de travail change a partir d'ici. Demande explicite de l'utilisateur: "A partir de maintenant, il ne faut plus modifier le projet i86. Toutes les modifications doivent-etre faites dans le projet du dossier breadboard-pc." Suite a cette demande, un nouveau depot GitHub public `ve2cuy/breadboard-PC` a ete cree (contenu du dossier breadboard/ sauf etapes/, plus le dossier medias/ a la racine, plus les images de disquette PC-DOS/MS-DOS malgre le risque de droit d'auteur signale - l'utilisateur a demande de les inclure quand meme; README.md racine = celui de Solution-01) et clone localement dans C:\Users\alin_\github\breadboard-PC - release GitHub v1.0 publiee. CE FICHIER Directives.md CONTINUE DESORMAIS DANS CE DEPOT (breadboard-PC), plus dans i86 - i86 ne doit plus recevoir aucune modification.
* Demande: integrer dans le pont STM32 la fonctionnalite du projet Arduino separe `projets/Clock-8088` (i86, tourne sur un Arduino UNO R4 externe: genere l'horloge du 8088 par PWM materiel a 1/3 de cycle utile, frequence ajustable par un potentiometre, ~10kHz-4,77MHz), en utilisant une broche libre du STM32 Black Pill - elimine le besoin de la carte R4 separee. Menu vise: sous-menu Configuration, "1) Clock speed" (jusqu'ici un message "a venir") doit afficher la frequence resultante a la selection. Par defaut 4,77 MHz (vitesse de demarrage souhaitee); reglage permis de 1 a 10 MHz.
  - Choix de la broche: PB11 propose et implemente en premier, mais compilation echouee ("'PB11' was not declared in this scope") - verification faite dans le coeur STM32duino installe (variant_BLACKPILL_F411CE.h, PeripheralPins_BLACKPILL_F411CE.c, PeripheralPins.c): PB11 est ABSENT de toutes les tables de broches de cette carte, tres probablement non sortie sur le connecteur physique de cette variante Black Pill F411CE. Tout le port A et tout le port B (sauf PB2/BOOT1, risque) sont deja reserves par le protocole du pont; PC14/PC15 reserves au quartz RTC 32,768kHz; PH0/PH1 probablement lies au quartz principal 25MHz. Demande a l'utilisateur: PA3 confirmee libre sur le montage reel ("PA3 sur PC2 ne sont pas connectes sur mon montage" - la case reservee a TAG2/PC2 n'a jamais ete cablee) - PA3 retenue (meme timer/canal que PB11 aurait ete: TIM2 CH4).
  - Choix du reglage (demande a l'utilisateur): fleches Haut/Bas (+-1 MHz par pas), plus raccourcis directs 'D'/'d' -> 4,77 MHz et '8' -> 8 MHz (les 2 vitesses "classiques" d'un PC/XT d'origine). Chaque touche applique IMMEDIATEMENT la nouvelle frequence (pas d'etape de confirmation separee - reproduit le comportement continu du potentiometre d'origine, contrairement au design "tampon/annulable" d'Edit RAM, justifie car changer la frequence d'horloge n'est pas destructif comme une ecriture RAM).
  - Fait (arduino/8088_bridge_stm32/src/main.cpp): `#include <HardwareTimer.h>`; nouvelle broche `PIN_CLK8088 = PA3` (remplace l'ancienne `PIN_TAG2`, jamais cablee - son pinMode/digitalWrite d'initialisation retires); `HardwareTimer clockTimer(TIM2)`, table fixe `CLOCK_STEPS_HZ[]` de 11 frequences (1 a 10 MHz + 4,77 MHz insere a sa place, index 4 = valeur par defaut), `clockApply()` (`clockTimer.setPWM(4, PIN_CLK8088, hz, 33)` - 33% ~ 1/3 de cycle utile, comme l'original Renesas), `clockExec(action)` (0 lire, 1 +1 MHz, 2 -1 MHz, 3 -> 4,77 MHz, 4 -> 8 MHz, bornes respectees) renvoie la frequence resultante en 4 octets (poids faible d'abord). Nouvelle commande de protocole canal 3 `2Ch` (1 octet d'argument = l'action) ajoutee a `cmdNeed()` et au dispatcheur. `clockSetup()` appelee TOUTE PREMIERE dans `setup()`, avant meme le bloc `USE_TINYUSB` - le 8088 a besoin d'une horloge stable des la mise sous tension, avant les init plus lentes (SPI/USB/RTC). Compile proprement sur les 2 environnements PlatformIO (`blackpill_f411ce_usbdrive`, `blackpill_f411ce`).
  - Fait (lib/bridge.asm): `FS_CLOCK equ 2Ch`; nouvelle routine `fs_clock_cmd` (DL = action -> DX:AX = Hz resultant, CF=1 si delai/erreur) - meme convention poids-faible-d'abord que `fs_cmd4`/`fs_dir_next`, mais avec un octet d'argument en plus (pas une simple variante de fs_cmd4).
  - Fait (solution-01.asm): l'option '1' du sous-menu Configuration appelle desormais `clock_speed_action` (remplace le message "a venir", `txt_config_clock_tbd` retiree). `clock_speed_action` affiche un ecran statique (titre + aide "Haut/Bas: +-1 MHz" / "D=4.77 8=8 Echap=fin"), envoie l'action 0 (lecture) via `fs_clock_cmd`, appelle `clock_show`, puis boucle sur `ps2_get_char` (Haut->1, Bas->2, D/d->3, '8'->4, Echap->retour), reappelant `fs_clock_cmd`+`clock_show` a chaque touche; `dm_e_tmo` affiche sur timeout (CF=1). `clock_show` convertit DX:AX (Hz) en "N.NN MHz" par 2 divisions 32 bits/16 bits successives (par 10000 puis par 100), partie entiere TOUJOURS affichee sur 2 caracteres (espace de tete si <10) pour garder une largeur de ligne LCD constante d'un reglage a l'autre, sans caractere perime a effacer. Bug trouve et corrige AVANT tout test (revue de code): `clock_show` ecrivait initialement les chiffres sans repositionner le curseur LCD - `gotoxy 1, 0, LCDI2C` ajoute en tete de la procedure pour garantir la bonne position quelle que soit l'etat laisse par l'appelant.
  - Verifie: make check/check-modules/PS2 + make test (aucune regression) + 2 bancs Unicorn dans le dossier de travail (pont simule via interception des octets de commande 2Ch/reponse canned): sequence d'actions envoyees correcte (0 a l'entree, puis 1/2/3/4 pour Haut/Bas/D/8), affichage "Frequence: N.NN MHz" correct pour 5,00/3,00/4,77/8,00 MHz (avec le double espace de remplissage attendu pour un chiffre unique - premier essai du test corrige, ce n'etait pas un bug d'affichage), retour correct au sous-menu apres Echap. Piege de banc d'essai rencontre et corrige en cours de route: l'injection de touches INCREMENTALE (existante, un octet a la fois) ne fonctionne pas pour les sequences ANSI multi-octets des fleches (ESC [ A/B) - les octets intermediaires sont consommes par des appels imbriques a `uart_wait_byte` qui ne redonnent jamais la main au point d'arret surveille avant la fin de la sequence; corrige en injectant chaque "paquet" de touche (1 octet pour une touche ordinaire, 3 pour une fleche) en un seul bloc atomique. Compilation du pont verifiee separement sur les 2 environnements PlatformIO (aucun test materiel possible depuis ce banc, pas de vrai STM32 ni de vrai 8088 emules). README.md mis a jour (Solution-01: section Configuration/Clock speed; arduino/8088_bridge_stm32: cablage PA3, protocole 2Ch). A VALIDER SUR LE MATERIEL: cabler PA3 vers la broche CLK (19) du 8088 (remplace le fil de l'Arduino UNO R4), flasher le nouveau firmware du pont ET la nouvelle ROM - qualite reelle du signal PWM (precision de frequence, cycle utile surtout en haut de plage ou la resolution du minuteur est plus grossiere) et bon fonctionnement du 8088 sous cette nouvelle horloge jamais confirmes.
* Confirme sur le materiel reel: l'horloge fonctionne (PA3/TIM2 CH4 du pont STM32 genere correctement le signal CLK du 8088, remplace avec succes l'ancien Arduino UNO R4).
* Rapport de bug (suite a la confirmation ci-dessus): sur l'UART, aucune instruction n'est visible dans le sous-menu Clock speed - seulement sur le LCD. Cause: `clock_speed_action` (solution-01.asm) envoyait son titre/aide ("Clock speed" / "Haut/Bas: +-1 MHz" / "D=4.77 8=8 Echap=fin") UNIQUEMENT au LCD (`print ..., LCDI2C`) - jamais a l'UART; seule la ligne "Frequence: N.NN MHz" (bios_puts, UART seulement) y apparaissait. Demande combinee: refondre le sous-menu en menu NUMEROTE (comme le reste du projet), avec pas fin (0,1 MHz) en plus du pas de 1 MHz:
  ```
  Current speed: 4.77 mhz
  1) Up : 0.1 Mhz
  2) Down: 0.1 Mhz
  3) Up : 1 Mhz
  4) Down: 1 Mhz
  5) 4.77 Mhz
  6) 8.0 Mhz
  ESC - back
  ```
  Repositionner le curseur/reafficher la frequence a chaque modification (deja le comportement de clock_show - conserve). Afficher aussi la vitesse courante au menu principal, a droite de la 1re ligne (ex. "1) Basic        4.77"). Fait:
  - arduino/8088_bridge_stm32/src/main.cpp: la table fixe `CLOCK_STEPS_HZ[]`/`clockIdx` est retiree, remplacee par une valeur continue `clockHz` (uint32_t, bornee [1;10] MHz, defaut 4 770 000). Nouvelle numerotation des actions de `clockExec`, alignee EXACTEMENT sur les options du menu (1=+0,1MHz, 2=-0,1MHz, 3=+1MHz, 4=-1MHz, 5=4,77MHz, 6=8MHz - 0=lire) - plus de decalage a traduire cote 8088. Compile proprement sur les 2 environnements PlatformIO.
  - lib/bridge.asm: commentaires de `fs_clock_cmd`/protocole 2Ch mis a jour pour la nouvelle numerotation - AUCUN changement de code (l'octet d'action est un simple passe-plat generique).
  - include/hardware.inc: nouvelle variable `CLOCK_FREQ_HZ_OFF` (double mot, VAR_SEG, emplacement libre 0FC65h entre BRIDGE_EXPECT_OFF et BRIDGE_RX_BUF_OFF) - cache de la frequence courante cote 8088, evite un aller-retour au pont a CHAQUE redessin du menu principal (frequent - apres chaque action de sous-menu). Initialisee a 4 770 000 juste apres l'effacement de VAR_SEG (start:, solution-01.asm) - correspond a la valeur par defaut REELLE du pont a SON propre demarrage - puis tenue a jour par `clock_show` a chaque lecture/reglage reussi.
  - solution-01.asm, refonte complete de clock_speed_action/clock_show, plus 3 nouvelles routines PARTAGEES (evitent de dupliquer la logique d'affichage 3 fois - UART seul pour le menu principal, LCD seul pour le menu principal, UART+LCD simultanes pour le sous-menu): `clock_hz_to_wholefrac` (DX:AX Hz -> BL/BH partie entiere/decimale, math extraite telle quelle de l'ancien clock_show), `clock_print_digits` (BL/BH + BP=cible en bits [bit0 UART, bit1 LCD] -> "N.NN", 5 caracteres largeur constante), `clock_print_str` (CS:SI + BP=cible -> chaine simple, ex. le suffixe " MHz" qui doit maintenant apparaitre sur LCD ET UART - avant, seulement UART via bios_puts). `clock_speed_action`: le menu fixe (1-6 + Echap) est desormais envoye UNE FOIS a l'entree a la fois sur `txt_menu_clock_head`/`txt_menu_clock_opts` (UART, texte complet) ET `lcd_txt_clock_opts_l1/l2/l3` (LCD, 3 lignes compactees - ex. "5)4.77 6)8.0 ESC=Fin", exactement 20 caracteres); dispatch touche simplifie a `dl = al - '0'` pour '1'-'6' (numerotation IDENTIQUE au code d'action du pont, plus de table de correspondance). `clock_show`: deplace le prefixe "Current speed: " (avant "Frequence: ") sur la ligne 0 du LCD (au lieu de 1 - plus de titre statique separe), mais UART SEULEMENT (pas la place sur 20 colonnes) - le LCD ne montre que "N.NN MHz" (digits + suffixe, 9 caracteres); met a jour CLOCK_FREQ_HZ_OFF. Nouvelle `clock_main_speed_print` (BP=cible, appelee 2 FOIS par `.main_menu` - UART juste apres "1) Basic" avant le CRLF puisque `txt_menu_main` est scinde en `txt_menu_main_head`/`_rest`, puis LCD apres le dessin complet de `lcd_txt_menu_main_l1` sinon son padding pleine largeur ecraserait les chiffres - `gotoxy 0,15` pour les 5 derniers caracteres de la ligne 0).
  - Verifie: make check/check-modules/PS2 + make test (aucune regression) + nouveau banc Unicorn (clock_smoke3.py, dossier de travail): sequence d'actions correcte pour +1/+0,1/->4,77/->8,0 MHz = [3,1,5,6]; le menu du sous-menu (banniere, 6 options, ligne de retour) apparait bien sur l'UART cette fois (bug confirme corrige); "Current speed: N.NN MHz" correct pour chaque reglage; menu principal affiche "1) Basic    4.77 MHz" AVANT toute visite du sous-menu (valeur par defaut du cache) et "1) Basic    8.00 MHz" APRES (cache mis a jour), SANS commande 2Ch supplementaire envoyee au retour au menu principal (confirme l'absence d'aller-retour au pont a chaque redessin). README.md mis a jour (Solution-01: sous-menu Clock speed + affichage au menu principal; arduino/8088_bridge_stm32: table protocole 2Ch). A VALIDER SUR LE MATERIEL: affichage UART et LCD du nouveau menu, reglage par pas de 0,1 MHz.
* Demande: ajouter au sous-menu Configuration une option "2) Test CPU speed" - lance un banc d'essai d'AU MOINS 30 secondes a 4,77 MHz, indique le temps ecoule en secondes et un pourcentage par rapport a une execution a 4,77 MHz (exemple donne: "le 8088 roule 20% plus vite qu'un 8088 a 4,77 mhz. Vitesse estimee de 00.00 mhz."), avec une progression visible pendant le test. Fait:
  - Principe: charge FIXE (nombre d'iterations connu a l'avance d'une boucle "dec bx / loop" - 8088, PAS de 8259/timer materiel), decoupee en `CPU_TEST_CHECKPOINTS` (30) "checkpoints" de `CPU_TEST_INNER_REPS` (8) boucles CX=0 (65536 iterations chacune) - total 30*8*65536 = 15 728 640 iterations. La duree REELLE est mesuree via la RTC du pont (fs_time/rtc_get, lib/bridge.asm/bios.asm) - INDEPENDANTE de l'horloge du 8088 (contrairement a un comptage de cycles logiciel, circulaire ici puisque c'est justement la vitesse du CPU qu'on cherche a mesurer). Comparee a `CPU_TEST_REF_SECONDS` (60, constante ESTIMEE - PAS mesuree sur le materiel, a recalibrer: lancer le test a 4,77 MHz - reglage par defaut - et reporter la valeur REELLEMENT affichee) pour calculer le pourcentage (`|R-T|*100/T`) et la vitesse estimee (`4,77*R/T` MHz).
  - solution-01.asm: nouvelle option '2' du sous-menu Configuration -> `cpu_speed_test_action`. Affiche "Ecoule: NNN s" (ligne 0 du LCD, meme convention largeur-constante que clock_show - 3 chiffres zero-remplis via `i2c_lcd_tx_dec3`) mise a jour a CHAQUE checkpoint (`cpu_test_show_progress`) - permet de constater la progression. Echap (verification NON BLOQUANTE via `ps2_key_available`, meme technique que dump_memory_action) interrompt le test a la fin du checkpoint courant. A la fin (`cpu_test_show_result`): pourcentage + vitesse estimee (reutilise `clock_print_digits`/nouvelle `centihz_to_wholefrac` - extraite de `clock_hz_to_wholefrac`, qui l'appelle desormais aussi, pour ne pas dupliquer la conversion centiemes-de-MHz -> "N.NN"), attend une touche avant de revenir au sous-menu. Nouvelles `cpu_test_rtc_to_seconds` (h/m/s -> secondes depuis minuit, 32 bits car 23*3600 depasse 16 bits) et `cpu_test_elapsed_seconds` (soustraction 32 bits, gere un passage de minuit). Nouvelle variable `CPU_TEST_START_SEC_OFF` (hardware.inc, double mot, emplacement libre 0FC69h).
  - Bug trouve ET CONFIRME PAR L'UTILISATEUR pendant le developpement (avant tout commit): `cpu_test_show_progress` utilise SI en interne (pointeurs de texte: `txt_cpu_test_elapsed`/`_seconds`/`txt_crlf`) sans le preserver, alors que l'appelant (`cpu_speed_test_action`) utilise JUSTEMENT SI comme compteur de checkpoints restants - le "dec si / jnz .checkpoint" qui suit l'appel operait donc sur une valeur ecrasee (l'adresse ROM d'un des textes), qui ne descend a 0 qu'apres des dizaines de milliers d'iterations parasites: le test semblait ne "jamais s'arreter" (symptome exact rapporte: "le temps ecoule depasse 30 secondes, il ne doit pas... j'ai l'impression que la condition d'arret n'est jamais vraie" - repere INDEPENDAMMENT, en parallele, par un banc Unicorn dans le dossier de travail qui bouclait des centaines de fois sur "Ecoule: 30 s"). Corrige: `push si` / `pop si` autour de l'appel a `cpu_test_show_progress`.
  - 2e bug trouve ET CONFIRME PAR L'UTILISATEUR ("l'affichage du temps ecoule sur le LCD est en mode TTY, il faut plutot repositionner le curseur a la position d'affichage", puis "c'est le meme probleme lors de la modification de la vitesse"): "gotoxy ligne,colonne,LCDI2C" (macro, AH=02h) ne positionne QUE le curseur LOGIQUE (variable RAM BIOS_CURSOR_LCDI2C_*) - SANS "print" immediatement a la suite (qui, lui, repositionne PHYSIQUEMENT le curseur avant CHAQUE caractere, via int10h_print_string), le curseur PHYSIQUE du LCD ne bouge JAMAIS reellement: une ecriture "brute" suivante (i2c_lcd_data/i2c_lcd_tx_dec3/clock_print_digits/clock_print_str) continue tout simplement de la ou le PRECEDENT write l'a laisse - comportement "TTY" plutot que positionne. Ce piege etait DEJA documente dans le projet (voir l'en-tete de int10h_print_string, et registers_dump_action qui l'evite correctement via `i2c_lcd_goto LCD_LINE4` pour sa section FLAGS) mais pas suivi ici. Touchait EN FAIT 4 endroits, pas seulement le nouveau test CPU: `clock_show` (ligne 0), `clock_main_speed_print` (ligne 0, colonne 15), et les 2 nouvelles routines du test CPU (`cpu_test_show_progress`, `cpu_test_show_result` - 3 positions: colonne 8 ligne 0, colonne 12 ligne 1, colonne 5 ligne 2). Corrige: nouvelle macro `i2c_lcd_goto_col` (include/lcd_macros.inc, %1=LCD_LINE1..4, %2=colonne constante - positionnement PHYSIQUE reel, meme principe que `i2c_lcd_goto` existant mais avec une colonne arbitraire) substituee a chaque "gotoxy ..., LCDI2C" BRUT (sans print a la suite) dans ces 4 endroits.
  - Verifie: make check/check-modules/PS2 + make test (aucune regression) + banc Unicorn dedie (cpu_test_smoke.py, dossier de travail - constantes CPU_TEST_CHECKPOINTS/INNER_REPS PATCHEES DANS LE BINAIRE ASSEMBLE, pas dans la source, a 3x1x65536 pour un test rapide; RTC simulee via interception du canal 3/commande 01h - sequence de secondes controlee): banc complet (30/20/10s de progression, resultat final EXACT pour R=60/T=30 - "100% plus vite", "9.54 MHz" - calcule a la main et compare octet pour octet) et banc interrompu (Echap au 1er checkpoint - aucune ligne de progression, aucun resultat, retour immediat) tous les 2 valides (11 verifications). Nouveau banc dedie a la correction du 2e bug (lcd_position_smoke.py): capture les octets envoyes sur les canaux LCD_CMD/LCD_DATA du pont et verifie que la commande DDRAM 80h (LCD_LINE1) precede bien CHAQUE groupe de 5 caracteres "N.NN" ecrit par clock_show (2 fois, sur 2 appels) - **confirme discriminant**: rejoue avec l'ancien "gotoxy" (copie temporaire du fichier, restauree ensuite) et le test echoue bien (0 occurrences au lieu de 2), prouvant qu'il aurait detecte le bug original. README.md mis a jour (section Configuration: description du test, exemple d'affichage, avertissement explicite sur la calibration non verifiee de CPU_TEST_INNER_REPS/CPU_TEST_REF_SECONDS). A VALIDER SUR LE MATERIEL: duree reelle du banc a 4,77 MHz (recalibrer CPU_TEST_REF_SECONDS en consequence), lisibilite de l'affichage LCD (positions physiques maintenant corrigees mais jamais vues sur un vrai afficheur).
* Confirme sur le materiel reel: les 2 bugs ci-dessus sont bien corriges (le test s'arrete normalement, l'affichage LCD est correctement positionne). Rapport de 2 nouveaux problemes:
  - Duree du test ~60s a 4,77 MHz (pas 30s - attendu, "au moins 30s" seulement, deja documente). Premier resultat obtenu avec l'ANCIENNE constante ESTIMEE (CPU_TEST_REF_SECONDS=60): "Le 8088 roule 13% plus lent qu'un 8088 a 4,77 MHz. Vitesse estimee: 4.14 MHz" - alors que le 8088 tourne reellement a 4,77 MHz (reglage par defaut, non modifie). Cause: 60 n'etait qu'une estimation, jamais mesuree. Calcul inverse EXACT a partir des 2 valeurs rapportees (|60-T|*100/T=13 ET 477*60/T=414 - les 2 equations ne sont simultanement satisfaites, en entiers, QUE par T=69) donne la duree REELLEMENT mesuree: 69s. Corrige: `CPU_TEST_REF_SECONDS` 60 -> 69 (voir sa definition, solution-01.asm) - a la prochaine execution a 4,77 MHz, le resultat devrait maintenant afficher ~0% et ~4,77 MHz.
  - "Si le test est lance une deuxieme fois [directement depuis le sous-menu Configuration, sans repasser par le menu principal], ceci est affiche, sans aucune progression" (seulement la banniere "--- Test CPU speed ---" / "Banc d'essai en cours..."); confirme que "il faut revenir au menu principal pour que le test fonctionne a nouveau". Cause exacte non confirmee avec certitude (pas d'acces direct au materiel depuis cette session), mais un DEFAUT DE CONCEPTION reel a ete trouve et corrige en cours d'investigation, independamment de la cause precise: `cpu_test_show_progress` (voir plus haut) ignorait SILENCIEUSEMENT un timeout du pont (CF=1 apres rtc_get) a CHAQUE checkpoint - si le pont cessait de repondre aux commandes GET_TIME en cours de route (par exemple apres les nombreux appels du 1er test - 32 en tout sur ~69s), le test continuait EN SILENCE ses ~30 checkpoints restants sans JAMAIS rien afficher, indiscernable d'un blocage reel. Corrige: `cpu_test_show_progress` renvoie desormais CF=1 a l'appelant (au lieu de l'avaler), et `cpu_speed_test_action` abandonne PROPREMENT (meme message "The bridge does not answer." qu'un timeout a l'entree du test ou dans cpu_test_show_result - comportement desormais COHERENT partout dans cette routine) des le premier checkpoint en echec, plutot que de laisser tourner les checkpoints restants sans aucun retour. Meme si ce n'est pas prouve etre LA cause exacte du symptome rapporte, c'est un vrai bug de robustesse corrige (l'ancien comportement pouvait masquer un probleme materiel reel derriere un faux "gel"), et le nouveau comportement rendra un futur probleme similaire IMMEDIATEMENT visible (message d'erreur au lieu d'un silence) plutot que de necessiter une nouvelle investigation a l'aveugle.
  - Verifie: make check/check-modules/PS2 + make test (aucune regression) + 3e scenario ajoute a cpu_test_smoke.py (dossier de travail): pont simule "muet" a partir du 2e appel GET_TIME (apres le depart, donc des le 1er checkpoint) - confirme l'abandon immediat avec le message d'erreur, aucune ligne de progression, aucun resultat final (16 verifications au total desormais, sur les 3 scenarios). Scenario "banc complet" recalibre sur R=T=69 (0% d'ecart, 4,77 MHz estime exactement) plutot que l'ancien R=60/T=30 arbitraire. README.md mis a jour (duree/calibration reelles, mention de l'abandon propre sur timeout mi-test). A VALIDER SUR LE MATERIEL: confirmer que le pourcentage/la vitesse estimee sont desormais corrects a 4,77 MHz, et si le "gel" au 2e lancement se reproduit malgre la correction ci-dessus (auquel cas la vraie cause reste a trouver - le message d'erreur explicite, si le pont EST effectivement en cause, devrait au moins le confirmer clairement).
* Confirme sur le materiel reel: la calibration (CPU_TEST_REF_SECONDS=69) est EXACTE - resultat "0% plus vite... Vitesse estimee: 4.77 MHz" a l'horloge par defaut, avec 30 lignes de progression coherentes (2-3s d'ecart entre checkpoints, total 69s pile). Le "gel au 2e lancement" n'est PAS reapparu dans ce rapport (le correctif du timeout mi-test - voir ci-dessus - est plausiblement en cause, meme si non confirme explicitement).
  - Nouvelle demande: la duree du test (~69s, confirmee) est plus longue que necessaire - preference pour ~30 secondes (le minimum demande a l'origine). Fait: `CPU_TEST_INNER_REPS` reduit de 8 a 4 (projection LINEAIRE a partir de la mesure reelle: chaque repetition represente un travail identique, donc 69*4/8 = 34,5s, arrondi a 35). `CPU_TEST_REF_SECONDS` mis a jour en consequence: 69 -> 35 (PROJECTION, pas une nouvelle mesure directe - le commentaire du code et le README invitent a reconfirmer par un lancement reel a 4,77 MHz et a ajuster si l'ecart avec "Ecoule: ..." depasse 1-2s).
  - Verifie: make check/check-modules/PS2 + make test (aucune regression) + cpu_test_smoke.py recalibre sur R=T=35 (0%/4,77 MHz, meme raisonnement qu'avant, valeurs mises a l'echelle) - 16 verifications toujours valides. README.md mis a jour (exemple d'affichage a 12/23/35s, explication de la reduction). A VALIDER SUR LE MATERIEL: confirmer que la duree reelle a 4,77 MHz est bien proche de 35s (projection lineaire, jamais mesuree directement a INNER_REPS=4).
* Confirme sur le materiel reel (CPU_TEST_INNER_REPS=4): "Le 8088 roule 2% plus vite qu'un 8088 a 4,77 MHz. Vitesse estimee: 4.91 MHz" - avec la projection CPU_TEST_REF_SECONDS=35 (pas encore une mesure directe). Calcul inverse EXACT a partir de ces 2 valeurs ((35-T)*100/T=2 ET 477*35/T=491 - les 2 equations ne sont simultanement satisfaites, en entiers, QUE par T=34) donne la duree REELLEMENT mesuree: 34s - quasi identique a la projection lineaire (34,5s), confirmant que le calcul lineaire etait fiable. Corrige: `CPU_TEST_REF_SECONDS` 35 -> 34 (mesure directe desormais, plus une projection).
  - Verifie: make check/check-modules/PS2 + make test (aucune regression) + cpu_test_smoke.py recalibre sur R=T=34 (0%/4,77 MHz) - 16 verifications toujours valides. README.md mis a jour (exemple d'affichage a 11/22/34s, calibration decrite comme MESUREE plutot que projetee). Calibration du banc d'essai "2) Test CPU speed" desormais consideree COMPLETE et confirmee sur le materiel reel (34s a 4,77 MHz, respecte le minimum de 30s demande, resultat exact a la reference).
* NOTE: nouveau fichier `Manifest.md` (racine du depot breadboard-PC) - l'utilisateur y ajoute desormais des directives (le texte entre parentheses y precise ce qui s'adresse specifiquement a Claude). 3 chantiers demandes en une fois: 1) points de progression UART (au lieu des secondes) pour le test CPU speed + annonce de la duree au depart; 2) compilation conditionnelle bilingue FR/EN (ROM_FR/ROM_EN) pour tous les textes UART/LCD; 3) sous-menu Configuration: options Heure/Date (regler la RTC) et Information (ecran recapitulatif: date/heure rafraichie chaque seconde, version BIOS, firmware STM, taille RAM, espace disque, vitesse CPU). Decision (demande a l'utilisateur): traiter un chantier a la fois, DANS L'ORDRE du fichier - le bilinguisme (chantier 2) touchera TOUS les textes deja ecrits, mais l'utilisateur a choisi l'ordre du fichier plutot que de le repousser en dernier.
* Chantier 1/3 (Manifest.md): "Lors du test de vitesse, afficher sur le UART des points sur la meme ligne, au lieu des secondes... indiquer qu'il dure environ 30 secondes." Fait (solution-01.asm):
  - `txt_cpu_test_head`: la ligne d'intro annonce desormais "duree: environ 30 secondes" (texte fixe, pas calcule a partir de CPU_TEST_REF_SECONDS - la demande visait un message simple, pas une valeur dynamique); la ligne vide de separation qui suivait est retiree (les points de progression commencent directement sur la ligne suivante).
  - `cpu_test_show_progress`: l'UART reçoit desormais un seul "." par checkpoint (uart_tx_byte, SANS CRLF - tous les points d'un meme test s'accumulent sur la MEME ligne), au lieu de "Ecoule: NN s\r\n" repete a chaque fois. Le LCD est INCHANGE (toujours "NNN" numerique, colonne 8, ligne 0). Piege trouve et corrige AVANT tout test (revue de code): "mov al,'.'" ecrase AL, qui contenait le poids faible de T (le compte de secondes, necessaire ENSUITE pour le LCD) - corrige en sauvant T dans BX avant d'ecrire le point, puis en le restaurant juste avant l'appel a i2c_lcd_tx_dec3.
  - `cpu_test_show_result` et les 2 `.tmo:` concernes (cpu_speed_test_action - timeout a l'entree OU propage depuis un checkpoint en echec -, cpu_test_show_result - timeout de la lecture finale): ajout d'un CRLF explicite avant le premier texte affiche ("Ecoule: ..." ou le message d'erreur du pont), pour terminer proprement la ligne de points en cours - sans quoi le resultat/l'erreur se serait retrouve colle a la suite des points sur la meme ligne. Inoffensif dans le cas ou aucun point n'a encore ete affiche (timeout des l'entree): juste une ligne vide de plus.
  - Verifie: make check/check-modules/PS2 + make test (aucune regression) + cpu_test_smoke.py adapte (nouvelles verifications: annonce de duree presente, points "..." presents sur l'UART, UNE SEULE occurrence de "Ecoule:" au lieu d'une par checkpoint) - 17 verifications, toutes valides. Rendu UART verifie caractere pour caractere (repr Python de la sortie capturee): "--- Test CPU speed ---\r\nBanc d'essai en cours, duree: environ 30 secondes (Echap pour annuler)...\r\n...\r\nEcoule: 34 s\r\nLe 8088 roule 0% plus vite..." - conforme a la demande (30 points tiennent largement sur une seule ligne d'un terminal 80 colonnes). README.md mis a jour (exemple d'affichage, description du nouveau comportement UART vs LCD inchange). A VALIDER SUR LE MATERIEL.
* Chantier 2/3 (Manifest.md): "Implementer une compilation conditionnelle pour les messages des interfaces UART et LCD... produire un ROM_EN et un ROM_FR en fonction d'un parametre a la compilation... tous les messages de la version francaise sont en francais... tous les messages de la version anglaise sont en anglais." Portee precisee avec l'utilisateur (question posee): "moniteur + BIOS partage" (solution-01.asm + lib/bios.asm - amorcage DOS, interruption non implementee) - PAS les interpreteurs BASIC/Tiny BASIC (chantier beaucoup plus vaste, explicitement exclu). Fait:
  - Mecanisme: chaque texte traduisible duplique dans une branche `%ifdef LANG_EN` (anglais) / `%else` (francais, PAR DEFAUT - inchange pour `make`/`make rom`/`nasm solution-01.asm` sans aucun `-d`) - MEME etiquette dans les 2 branches, un seul jeu reellement assemble a la fois. Textes PUREMENT techniques (mnemoniques de registres AX=/BX=/.., drapeaux DEBUG.COM OV/NV/.., sequences ANSI, "OK", donnees binaires du programme Edit+Run par defaut) laisses PARTAGES (1 seule definition, hors %ifdef) - deja "universels", rien a traduire; ca reduit sensiblement la duplication par rapport a un dedoublement total du bloc de donnees.
  - Piege AUDITE et evite AVANT de traduire (pas trouve par un test qui aurait echoue - repere par relecture attentive du code, apres l'experience du piege "curseur LCD" de la session precedente qui, lui, avait ete trouve tardivement): certains textes LCD sont suivis d'un positionnement de colonne physique CODE EN DUR (`i2c_lcd_goto_col`, voir le chantier "Test CPU speed" precedent) qui suppose une largeur de PREFIXE precise - notamment "Ecoule: " (8 caracteres exactement) avant les 3 chiffres de cpu_test_show_progress/show_result. Deux strategies utilisees selon le cas: (a) choisir une traduction anglaise de LA MEME LONGUEUR ("Elapsed:", SANS espace, toujours 8 caracteres - evite de rendre la colonne elle-meme conditionnelle) pour ce cas precis; (b) pour "Bloc:"/"/126 Def:" (test RAM, msg_bloc_progression), verifie que la position s'appuie en fait sur un enchainement SEQUENTIEL d'ecritures brutes depuis UNE SEULE position de depart (i2c_lcd_goto UNIQUE puis i2c_lcd_print/i2c_lcd_tx_dec3 qui suivent, auto-incrementation MATERIELLE du LCD) - AUCUNE dependance de longueur, donc "Blk:"/"/126 Flt:" (longueurs differentes) ne posent aucun probleme. Deux abreviations deja identiques dans les 2 langues repérées et EXPLOITEES pour eviter d'autres cas a risque: "vs 4.77MHz: " et "Est: " (deja des abreviations anglaises standard) laissees PARTAGEES plutot que "traduites" vers elles-memes.
  - solution-01.asm: bloc de donnees (~377 lignes, "Section suivante: donnees et textes") restructure - branche `%ifdef LANG_EN` (nouvelle, ~130 lignes) / `%else` (francais, texte EXISTANT deplace tel quel) / puis section partagee. Bug trouve ET CORRIGE AVANT tout test (revue du 1er essai de compilation -dLANG_EN=1): `txt_crlf`/`txt_ok_court` places PAR ERREUR seulement dans la branche %else (identifies comme "partages" dans le plan, mais physiquement oublies dans la mauvaise section) - la compilation EN echouait avec "symbol not defined" en cascade partout ou ils sont utilises; corrige en les deplacant dans la section partagee.
  - lib/bios.asm: 2 groupes de messages traduits - `bios_msg_boot/bootA/nosig/nodisk/tmo` (amorcage DOS via INT 19h) et `dm_title/prompt/cancel/none/e_disk/e_tmo/e_size/e_nf/e_mount` (sous-menu "3) Boot disk image", dos_menu) etaient DEJA EN ANGLAIS SEULEMENT (aucune version francaise n'existait avant) - le francais devient donc le nouveau texte AJOUTE (pas juste une traduction inverse), et bascule en PAR DEFAUT pour rester coherent avec le reste du projet. `txt_ini_1/3` (message "Interruption non implementee") traduits (etaient DEJA en francais par defaut - AH=/code/*** partages, deja universels).
  - Makefile: nouvelles cibles `rom-fr` (= comportement de `rom`, sans -d) et `rom-en` (`-dLANG_EN=1 -w-error=label-redef-late`). Le flag supplementaire est necessaire UNIQUEMENT pour rom-en: nasm signale (par defaut, en ERREUR) que plusieurs labels "changent pendant la generation de code" - la taille differente des textes anglais retarde la convergence normale des multiples passes de nasm sur des sauts eloignes ailleurs dans ce gros fichier (deja limite, pas cause par ce chantier). Verifie METICULEUSEMENT avant d'accepter de degrader cette erreur en avertissement: 2 compilations successives de rom-en produisent un binaire BINAIREMENT IDENTIQUE (diff vide) et check_rom.py valide sa structure - confirme que nasm CONVERGE bel et bien, juste en yant besoin d'une derniere passe non comptee par son detecteur de "trop de passes deja". rom/rom-fr n'ont jamais eu besoin de ce flag.
  - Regression trouvee ET CORRIGEE dans les tests EXISTANTS (pas dans le firmware): 5 echecs dans tests/bios_test.py (`make test`) - toutes des assertions qui verifiaient le texte ANGLAIS en dur (`b'Boot: flash disk'`, `b'no boot signature'`, `b'does not answer'`, `b'floppy image (A:)'`), puisque ce texte etait le SEUL qui existait avant ce chantier. Legitimement corrige (pas un contournement): le francais est desormais le comportement PAR DEFAUT partout dans le projet (coherent avec solution-01.asm depuis le debut) - les tests verifient maintenant le texte francais correspondant ("Amorce: disque flash", "signature de demarrage absente", "le pont ne repond pas", "image disquette (A:)"). Meme correction necessaire dans mon PROPRE banc Unicorn du chantier precedent (cpu_test_smoke.py, scenario "pont muet" - dm_e_tmo, partage avec dos_menu, est maintenant francais par defaut aussi).
  - Verifie: make check/check-modules/PS2 (francais ET anglais, TEST_PS2 inclus) + make test (aucune regression, apres correction des 5 assertions ci-dessus) + les 3 bancs Unicorn existants (cpu_test_smoke.py, clock_smoke3.py, lcd_position_smoke.py) tous encore valides sur le francais (comportement par defaut totalement inchange, texte deplace tel quel) + nouveau banc dedie (lang_en_smoke.py, dossier de travail): navigue dans les 4 sous-menus + Clock speed en anglais, verifie le texte anglais attendu partout (bannieres, options, "Esc: back to...") ET l'ABSENCE de tout residu francais ("Echap"/"Sous-menu"/"Vitesse" absents du flux capture). Reproductibilite verifiee (2 compilations successives -> binaire identique, francais ET anglais). README.md (nouvelle section "Bilinguisme (FR/EN)") et Makefile.md mis a jour. A VALIDER SUR LE MATERIEL: jamais teste sur un vrai afficheur/terminal (positions de colonne LCD anglaises en particulier - "Elapsed:034 s" sans espace, moins joli mais fonctionnellement correct).
* Chantier 3/3 (Manifest.md, dernier des 3): "Dans le menu Configuration, ajouter les items: Heure et date (permet de renseigner la date et l'heure du RTC); Information (jj-mm-aaaa hh:mm:ss rafraichie a toutes les secondes, BIOS version, STM firmware, RAM, DISQUE utilise/disponible, Vitesse CPU)." Fait:
  - Nouvelle commande de protocole `03h` VERSION DU FIRMWARE (demandee a l'utilisateur avant de l'ajouter: aucune vraie version de firmware n'existait, seulement "version (3)" du PROTOCOLE renvoyee par PING - sans rapport; l'utilisateur a confirme vouloir une VRAIE version plutot que de reutiliser ce "3"). arduino/8088_bridge_stm32/src/main.cpp: `FW_VERSION_MAJOR`/`FW_VERSION_MINOR` (1.0, assorti a "Version 1.0" du splash) -> 2 octets. lib/bridge.asm: `fs_version_cmd` (BH=majeure, BL=mineure, CF=1 si echec - meme convention que rtc_get). Les 2 environnements PlatformIO recompiles avec succes - NECESSITE UN REFLASH du pont (comme pour Clock speed).
  - Nouvelle routine `ps2_read_dec_editable` (lib/ps2.asm), MEME PRINCIPE que `ps2_read_hex_editable` (echo + retour arriere, largeur fixe) mais base 10 (MUL/DIV) au lieu d'un decalage de 4 bits (base 16): saisie de date/heure (decimal, PAS hexadecimal - contrairement a Edit RAM/Dump memory). 2 pieges trouves ET CORRIGES AVANT tout test materiel, tous deux lies a un registre qui semblait "libre" mais ne l'etait pas: (1) `mov cx,10` (pour le MUL/DIV) ecrasait CH, utilise ICI comme compteur PERSISTANT du nombre total de chiffres a lire (contrairement a ps2_read_hex_editable, qui ne s'en sert PAS - ses seules operations, SHL/OR, ne touchent pas CX) - corrige en utilisant DI comme registre scratch pour la constante 10 a la place (preserve via push/pop, donc toujours "jamais touche" du point de vue de l'appelant). (2) MEME APRES cette 1re correction, le banc d'essai echouait TOUJOURS de la meme facon (repere en le rejouant) - cause reelle: MUL et DIV ecrasent TOUJOURS DX (poids fort du produit/reste), QUELLE QUE SOIT l'operande choisie (donc meme en evitant CX) - DH sert ICI de compteur de chiffres SAISIS (contrairement, encore une fois, a ps2_read_hex_editable qui n'a pas ce probleme, ses operations ne touchant jamais DX); corrige par un push/pop dx explicite autour de CHAQUE MUL et DIV. Sans les 2 corrections, une saisie de "20" ne donnait qu'un seul chiffre accepte par champ (bloque des le 2e) puis, une fois le 1er piege corrige seul, aucune separation entre les champs n'apparaissait plus du tout (repere par un banc Unicorn qui capturait litteralement "2092026143507" au lieu de "20-09-2026" puis "14:35:07" - aucun "-"/":" nulle part, la saisie du dernier champ restant bloquee indefiniment en attente d'un chiffre qui n'arrivait jamais).
  - Nouvelle routine partagee `print_dec_n` (solution-01.asm, pres de clock_print_digits/clock_print_str): AX=valeur, CL=nombre de chiffres (largeur FIXE, zeros de tete), BP=cible (meme convention bit0 UART/bit1 LCD) - generalise l'affichage decimal a largeur fixe pour la date/l'heure (2 et 4 chiffres) et les versions BIOS/firmware (1 chiffre), la ou le projet n'avait jusqu'ici que i2c_lcd_tx_dec3 (LCD seul, largeur fixe a 3) et uart_tx_dec_word (UART seul, SANS zero de tete).
  - solution-01.asm: nouvelles constantes `BIOS_VERSION_MAJOR`/`MINOR` (1/0, assorti au splash - a maintenir manuellement en phase) et `DISK_TOTAL_KB` (8192, capacite NOMINALE de la flash W25Q64/8 Mo - aucune commande de protocole pour la capacite TOTALE, seulement l'espace LIBRE via fs_free existant, donc pas interrogee dynamiquement). `clock_datetime_action` ("3) Heure et date"): 2 invites chainees - "Date: JJ-MM-AAAA" (LCD_LINE1) puis "Heure: HH:MM:SS" (LCD_LINE2), meme mecanique de positionnement DDRAM chainee que dump_memory_action (colonnes calculees a partir de la longueur des prefixes deja affiches) - envoie les 7 octets a rtc_set (bascule DS sur VAR_SEG le temps de l'appel SEULEMENT - rtc_set l'exige - puis revient a CS aussitot apres, l'invariant "DS=CS partout" du reste du projet reste intact). `information_action` ("4) Information"): ecran recapitulatif - SEULE la ligne date/heure est rafraichie en direct (boucle non bloquante sur ps2_key_available + rtc_get, redessine des que la seconde change - un pont TEMPORAIREMENT muet pendant cette boucle ne fait PAS abandonner l'ecran, contrairement a cpu_test_show_progress: ici ce n'est qu'un affichage, pas une mesure a interrompre proprement); BIOS/STM/RAM/Disque/CPU interroges/calcules UNE SEULE FOIS a l'entree (demande explicite: pas besoin de les rafraichir chaque seconde) - un echec INDIVIDUEL de fs_version_cmd ou fs_free affiche "?" a la place plutot que d'abandonner tout l'ecran (seul un echec du TOUT PREMIER rtc_get, a l'entree, fait abandonner - la date/heure est le coeur de cet ecran). Bug trouve ET CORRIGE AVANT tout test (revue de code, pas par un echec de banc): les etiquettes "BIOS:"/"RAM:"/"Disque:" n'etaient imprimees QUE sur le LCD (oubliees sur l'UART) - meme categorie de bug que le tout premier chantier de cette session (Clock speed, instructions UART manquantes) - corrige en ajoutant un `print ..., UART` avant chaque `print ..., LCDI2C`.
  - Piege de largeur LCD reaudite pour ces nouveaux textes (meme classe que le bilinguisme): "BIOS:"/"STM:"/"RAM:"/"Disque:"/"CPU: "/"K "/"KB" sont TOUS suivis d'autre chose sur la MEME ligne (chiffres, un autre libelle) - PAS de padding "lcd_text" (qui aurait deplace le curseur physique trop loin, meme piege que "Ecoule:"/"Elapsed:" du chantier precedent): definis en `db` bruts. `lcd_txt_info_disk` ("Disque:"/"Disk:") rendu BILINGUE (contrairement a BIOS:/STM:/RAM:, deja identiques dans les 2 langues) car SANS risque de largeur ici (positionnement purement SEQUENTIEL, comme "Bloc:"/"Def:" du test RAM - aucun i2c_lcd_goto_col ne suit).
  - Verifie: make check/check-modules/PS2 (francais ET anglais, TEST_PS2 inclus) + make test (aucune regression) + les 4 bancs Unicorn existants tous encore valides + 2 nouveaux bancs dedies (datetime_info_smoke.py francais, datetime_info_en_smoke.py anglais, dossier de travail - injection d'Echap pendant la boucle non bloquante de information_action via un hook cible, meme piege/technique que cpu_speed_test_action): saisie complete d'une date/heure verifiee OCTET PAR OCTET dans la commande rtc_set envoyee au pont (annee/mois/jour/h/min/s exacts); ecran Information verifie champ par champ (BIOS 1.0, STM version simulee 2.3, RAM 126K, CPU 4,77 MHz avec l'espace de tete attendu, disque 1192/7000KB calcule a partir d'un fs_free simule) + scenario "pont muet des l'entree" (abandon propre, aucun contenu affiche au-dela du message d'erreur) - 24 verifications au total, toutes valides, dans les 2 langues. READMEs (Solution-01, arduino/8088_bridge_stm32) mis a jour. A VALIDER SUR LE MATERIEL: JAMAIS teste - reflash du pont necessaire pour la commande 03h, saisie clavier decimale jamais essayee physiquement, lisibilite reelle de l'ecran Information sur l'afficheur physique.
* NOTE additionnelle ajoutee par l'utilisateur DIRECTEMENT dans Manifest.md (pas via le chat), decouverte en verifiant `git status` avant de committer le chantier 3/3 ci-dessus - rapport de mesure sur le materiel reel: sous-menu Clock speed affiche "Current speed: 7.07 MHz", mais le test "2) Test CPU speed" lance juste apres estime "7.37 MHz" (54% plus vite que 4,77 MHz), ET une mesure directe a l'OSCILLOSCOPE donne 7,3-7,4 MHz - la valeur AFFICHEE (7,07) est donc fausse de ~4%, alors que l'ESTIMATION du test CPU (7,37) concorde tres bien avec l'oscilloscope. Diagnostic (lecture du code source de la bibliotheque STM32duino installee, framework-arduinoststm32/libraries/SrcWrapper/src/HardwareTimer.cpp): `clockExec` (arduino/8088_bridge_stm32/src/main.cpp) renvoyait jusqu'ici `clockHz`, la valeur DEMANDEE au minuteur - PAS ce qu'il genere REELLEMENT. `HardwareTimer::setOverflow(freq, HERTZ_FORMAT)` (appelee par setPWM) calcule le prescaler et l'ARR par 2 DIVISIONS ENTIERES SUCCESSIVES (`period_cyc = horloge_minuteur / freq`, puis `PeriodTicks = period_cyc / Prescalerfactor`) - chacune tronque, et l'erreur RELATIVE de cet arrondi grossit fortement a mesure que la frequence demandee s'eloigne de 4,77 MHz (period_cyc devient petit, la granularite du minuteur devient grossiere). Corrige: nouvelle variable `actualClockHz`, mise a jour dans `clockApply()` en relisant les registres REELS du minuteur juste apres `setPWM()` via `clockTimer.getOverflow(HERTZ_FORMAT)` (qui relit litteralement `LL_TIM_GetAutoReload`/`LL_TIM_GetPrescaler` - les MEMES registres que `setOverflow()` vient d'ecrire, donc reflete fidelement le materiel) - `clockExec` renvoie desormais `actualClockHz` au lieu de `clockHz`. AUCUN changement de protocole (toujours 4 octets, meme commande 2Ch) ni cote 8088 (le champ "resultante" de la documentation, deja ecrit ainsi, devient enfin exact - avant, il ne l'etait pas malgre ce que le commentaire affirmait).
  - Verifie: compilation des 2 environnements PlatformIO reussie (blackpill_f411ce, blackpill_f411ce_usbdrive) - AUCUN changement cote 8088 (ni solution-01.asm ni lib/bridge.asm, seulement des commentaires de documentation la) donc make check/check-modules/PS2 + make test + tous les bancs Unicorn existants revalides sans surprise (comportement 8088 totalement inchange - seule la VALEUR renvoyee par le pont differe, invisible depuis les bancs simules qui inventent leurs propres reponses canned). Les 2 ROM (`solution-01-fr.bin`/`solution-01-en.bin`, via `make rom-fr`/`make rom-en`) produites pour test par l'utilisateur. READMEs (Solution-01/lib/bridge.asm en commentaire, arduino/8088_bridge_stm32/README.md) mis a jour. A VALIDER SUR LE MATERIEL: la correction elle-meme (est-ce que "Current speed" affiche desormais bien ~7,3-7,4 MHz au lieu de 7,07 apres reflash?) - impossible a verifier depuis cette session (pas d'acces au materiel), c'est PRECISEMENT ce que l'utilisateur va tester.
* NOUVELLE note ajoutee par l'utilisateur DIRECTEMENT dans Manifest.md (item "2 -", pendant que le fix precedent tournait en arriere-plan) - 3 symptomes rapportes sur l'ecran "4) Information" (solution-01.asm, chantier precedent), tous sur du materiel reel: (1) la touche Echap n'a AUCUN effet sur cet ecran (capture UART fournie: la date/heure defile seconde apres seconde sans jamais s'arreter); (2) l'heure affichee sur le LCD reste FIGEE, elle ne s'actualise qu'a la frappe d'une touche (contrairement a l'UART qui, lui, defilait bien); (3) sur l'UART, chaque seconde imprime une NOUVELLE ligne au lieu de redessiner la meme ("repositionner le curseur sur la ligne de l'heure").
  - Diagnostic (lecture de lib/isr.asm/bridge.asm/README.md): la `.loop` de `information_action` rappelait `rtc_get` EN CONTINU, sans le moindre repit entre deux passages - aucune limite de frequence. Or `BRIDGE_EXPECT_OFF` (mis a 1 par `rtc_get` pendant tout l'aller-retour au pont, ~10 ms) est DEJA documente (README.md, etiquette PC1) comme un risque connu: une touche tapee PENDANT ce court intervalle "risque d'etre prise pour une reponse" et donc perdue - un risque juge ACCEPTABLE pour un rtc_get isole (rare, ~10 ms). Mais en rappelant rtc_get en boucle SANS AUCUN repit, cet ecran maintenait ce drapeau actif une fraction du temps proche de 100% (au lieu d'un cas rare), transformant un risque mineur en quasi-certitude: Echap (et toute autre frappe UART) etait presque toujours avale. Meme cause plausible pour le LCD fige: le martelement ininterrompu de commandes GET_TIME (sans le delai reel que le lien materiel exige entre deux commandes) desynchronisait/faisait echouer la plupart des reponses, traitees comme "pont muet" (CF=1, ignorees silencieusement) - une frappe de touche, en intercalant un peu de temps de traitement, laissait par hasard une commande aboutir de temps en temps, d'ou l'impression fausse que "l'heure ne bouge qu'a la frappe d'une touche".
  - Corrige (solution-01.asm, `information_action`): nouvelle constante `INFO_RTC_THROTTLE` (3000) et compteur SI decroissant - le pont n'est desormais interroge (rtc_get) qu'une fois toutes les INFO_RTC_THROTTLE passes de `.loop`, alors que le CLAVIER, lui, est toujours verifie a CHAQUE passe (aucune perte de reactivite pour Echap). Valeur choisie avec une large marge de securite meme a 1 MHz (borne basse du sous-menu Clock speed), tout en restant bien sous 1 seconde - donc toujours "rafraichie a toutes les secondes" comme demande a l'origine; A AJUSTER si le materiel reel montre que ce n'est pas encore suffisant. Pour le defilement UART: un CR (13, PAS CRLF) est desormais envoye juste avant de reecrire l'heure, repositionnant le curseur en debut de la MEME ligne (symetrique du `i2c_lcd_goto_col` deja utilise pour le LCD) - la ligne se redessine donc en place au lieu de defiler.
  - Bug trouve PENDANT le developpement de ce correctif (pas par l'utilisateur): le compteur SI etait initialise (`xor si,si`) trop tot - AVANT tout le bloc d'affichage statique BIOS/RAM/Disque, qui ecrase SI a repetition pour ses propres besoins (`mov si, <chaine>`) - si bien qu'en entrant reellement dans `.loop` pour la premiere fois, SI ne valait plus 0 mais l'adresse d'une chaine quelconque (tres grande), retardant le tout premier rafraichissement de dizaines de milliers de passes. Trouve par le banc Unicorn existant (datetime_info_smoke.py, verification "redessinee au moins 1 fois" devenue FAIL) AVANT tout essai materiel. Corrige en deplacant `xor si,si` juste avant l'etiquette `.loop`, apres tout l'affichage statique.
  - Verifie: make all/check/check-modules + build TEST_PS2 + make test (aucune regression, 13/110/323 verification(s), 0 echec(s)). Les 2 bancs Unicorn existants (datetime_info_smoke.py francais, datetime_info_en_smoke.py anglais) repassent integralement (le bug SI ci-dessus a d'abord fait echouer 1 verification sur 15, corrige puis reverifie a 15/15). Nouveau scenario ad hoc (hors bancs, verifie manuellement dans cette session): Echap injecte apres 50 passages rapides de `.loop` (grace au throttle, bien avant que le compteur de 3000 ne s'epuise) - confirme qu'un SEUL redessin a eu lieu (rtc_get non rappele entre-temps, throttle actif) et qu'Echap fonctionne quand meme immediatement. Les 2 ROM (`solution-01-fr.bin`/`solution-01-en.bin`) reconstruites et revalidees (check_rom.py) pour test par l'utilisateur. A VALIDER SUR LE MATERIEL: les 3 symptomes eux-memes (Echap reactif, heure LCD vivante, ligne UART fixe) - le diagnostic (martelement du pont/BRIDGE_EXPECT) est une deduction a partir du code et de la documentation existante, PAS confirme par une mesure directe (aucun acces au materiel depuis cette session); la valeur INFO_RTC_THROTTLE=3000 est un choix prudent, pas calibre sur le materiel reel - si le rafraichissement semble trop lent ou encore insuffisant pour Echap, ajuster cette constante.

* Rapporte sur le materiel reel: DOS instable, surtout pendant les acces disque (editer un fichier, `del`, `copy con fichier.txt` + texte + Ctrl-Z) - plantage de DOS ou redemarrage du systeme; d'abord attribue aux changements depuis v1.1, puis constate AUSSI avec la ROM et le pont v1.1 (pas une regression). Autre symptome reproductible: apres DOS 2.1 quitte par Ctrl-\, un nouvel "Boot disk image" figeait juste apres "Amorce: image disquette (A:)..." (remise sous tension necessaire). Au gel: plus aucune activite sur les broches d'adresse du 8088.
  - Diagnostic. `git diff v1.1..HEAD`: aucun changement fonctionnel sur le chemin DOS (INT 13h/16h/1Ah/19h, ISR, pont: seulement des textes et des adresses decalees). ROM de trace (BIOS_TRACE) fournie a l'utilisateur: sous DOS 3.3 ET sous DOS 2.1 (apres CLS), la DERNIERE ligne de trace est un INT 13h de LECTURE inacheve (`<13 0209 2500 0101 0100 0000` sans `-AH CF>`) - le 8088 s'arrete AU MILIEU d'une lecture de secteur, pendant laquelle le pont envoie ~530 octets (16 blocs de 32 + etat + somme), chacun livre par une IRQ1 (donc un cycle INTA du 8259). Toutes les attentes du pont ont un delai (on aurait vu "le pont ne repond pas"): ce n'est pas une boucle logicielle. Mesures de l'utilisateur au gel: CLK (broche 19) PRESENTE, DEL PC13 du pont clignote (pont vivant), READY = 5 V, HOLD = masse, NMI = masse; Ctrl-\ SANS effet (IRQ1 plus servie); RESET du 8088 SEUL (pont non touche) suffit - l'etat fautif est cote 8088/8259/8255, pas dans le pont.
  - Emulation (hors depot, dossier de travail): bancs Unicorn avec IRQ1 ASYNCHRONES (octets du pont et frappes livres par la vraie ISR via l'IVT, le 8255 modelise independamment de l'IRQ: IBF, octet suivant depose des que IBF = 0), DOS 3.3 et PC-DOS 2.1 (`copy con`, `type`, `del`, `dir`, `cls`), et ROM COMPLETE (menu -> USB Disk -> Boot disk image -> DOS 2.1 -> Ctrl-\ -> reamorcage -> DOS 2.1): AUCUN gel, ~145 000 IRQ1 par session. IF mesure a chaque `pop ss` de BIOS_ENTER sous DOS 3.3 et 2.1 (~1000 cas): toujours 0 (hypothese d'une interruption entre `pop ss` et `mov sp` ecartee). Conclusion: logique correcte; le gel vient du chemin d'interruption MATERIEL (cycles INTA, 8259/8255, integrite du bus pendant les rafales - le 8259 n'apparait pas dans les schemas KiCad, cablage d'INTA non verifiable d'ici), que l'emulateur ne reproduit pas.
  - Correctif (contournement logiciel, a confirmer sur le materiel): pendant CHAQUE commande au pont (`bridge_expect` AL=1, lib/bridge.asm - rtc_get, fs_*, secteurs, image de disquette, horloge, version), IR1 est MASQUEE au 8259 (`PIC_IMR_BRIDGE` = 11111110b, include/hardware.inc; `PIC_IMR_NORMAL` = 11111100b au retour, AL=0; valeurs ecrites telles quelles, IN 21h jamais utilise) et `bridge_rx_get_t` lit le 8255 elle-meme par SCRUTATION (IBF sur le Port C) quand le tampon est vide. Le classement de l'octet (reponse / frappe UART / scan code / Ctrl-\) est sorti de l'ISR dans `irq1_dispatch` (lib/isr.asm), appele par l'ISR ET par la scrutation - meme logique dans les deux cas. Un octet arrive pendant le masque et non lu (IBF = 1) est servi par l'ISR des le demasquage (front deja memorise dans l'IRR); lu par scrutation, IR1 redescend et aucune requete ne reste (pas d'IR7 parasite - verifie: aucune "interruption non implementee"). Resultat en emulation: 3 a 32 IRQ1 par session DOS au lieu de ~145 000 (27 au lieu de ~135 000 pour le scenario Ctrl-\ complet), tous les scenarios reussis. BR_TIMEOUT 0C000h -> 8400h (tour de scrutation ~45 % plus long: delais inchanges, ~0,5 s par unite a 4,77 MHz). DOS ne programme jamais le 8259 lui-meme (seuls 0FEh/0FCh ecrits sur 21h en emulation).
  - `BRIDGE_NO_ISR`: lib/bridge.asm assemble SANS lib/isr.asm (module BASIC autonome - lib/basic.asm le definit si ISR_ASM est absent -, `make check-modules` pour bridge.asm, tests/basic_test.asm, tests/bridge_test.asm): pas de scrutation (irq1_dispatch absent). Sans effet dans la ROM.
  - Correctif connexe (start:, solution-01.asm): le `sti` place juste apres l'initialisation de SS:SP, AVANT l'effacement de la RAM, est retire. Apres un redemarrage a chaud (Ctrl-\), le 8259 est encore programme, IR1 demasquee: une frappe pendant l'effacement (qui met l'IVT a 0) aurait fait sauter le 8088 en 0000:0000. Les interruptions ne sont plus activees qu'au `sti` existant, apres init_8259 (rien entre les deux n'en depend).
  - Verifie: make clean/all/check/check-modules + build TEST_PS2 + make test (13/110/323 verification(s), 0 echec(s)) + ROM FR/EN (check_rom.py) + ROM de trace. A VALIDER SUR LE MATERIEL: stabilite de DOS 3.3/2.1 pendant les acces disque (copy con, del, edition) et reamorcage apres Ctrl-\. Si le gel persiste malgre la scrutation, la cause n'est pas (seulement) l'INTA: refaire une trace BIOS_TRACE et observer INTR du 8255 / INT du 8259 / INTA# du 8088 a l'oscilloscope pendant une lecture de secteur.
* Confirme sur le materiel reel (DOS 3.30, solution-01-fr.bin, pont v1.1): stable avec la reception par scrutation - plusieurs essais: assemblage d'un programme avec MASM, creation de fichiers par copy con, suppressions. Le chemin d'interruption materiel (IRQ1/INTA du 8259 sous rafale) reste le suspect: le contournement evite le probleme sans l'expliquer. Reste a confirmer: reamorcage de DOS 2.1 apres Ctrl-\.
* Rapporte sur le materiel reel: DOS 2.1 a fige pendant un `copy con`, puis l'image (PCDOS2_1.IMG) ne s'amorcait plus (gel apres "Amorce: image disquette (A:)..."); de plus, les fichiers ajoutes au disque USB (par Windows, USB ON) n'apparaissaient plus dans la liste du pont (List files) alors que Windows les voyait.
  - Image abimee (copiee par l'utilisateur sous le nom pcdos2_1_bug.img, comparee a l'original): 4 secteurs differents seulement - FAT n°2 (secteur 3), repertoire (secteur 6: AUTOEXEC.BAT et YO.TXT, 0 octet, ajoutes) et donnees d'AUTOEXEC.BAT (secteur 304) coherents; mais la FAT n°1 (secteur 1) est ECRASEE par un contenu etranger (zeros, fragments ressemblant a un BPB, remplissage F6h du formatage; octet de media 0Fh au lieu de FCh) - DOS a ecrit dans la FAT un tampon au mauvais contenu (memoire deja corrompue, ou donnees prises au mauvais endroit). C'est cette FAT qui bloque l'amorcage suivant. Le gel de DOS 2.1 n'est donc PAS regle par la scrutation (qui a regle DOS 3.30): enquete a poursuivre (trace BIOS_TRACE du prochain gel sous DOS 2.1).
  - Liste du pont incomplete: DEFAUT du pont (arduino/8088_bridge_stm32/src/main.cpp, commande 17h "entree suivante"): le nom etait lu par getName() dans un tampon de 16 octets; pour un nom LONG de 16 caracteres ou plus ("pcdos2_1_bug.img", renomme sous Windows) getName() echoue, la longueur envoyee vaut 0, ce que le 8088 prend pour "plus d'entree": la liste s'arretait sur ce fichier et TOUS les suivants du repertoire disparaissaient (List files, FILES du BASIC, Boot disk image). Corrige: nom long s'il tient en 12 caracteres (casse conservee, ex. hello.asm), sinon le nom COURT 8.3 (getSFN, ex. PCDOS2~1.IMG, ouvrable tel quel par le 8088); une entree sans nom utilisable est sautee au lieu de terminer la liste. FW_VERSION 1.0 -> 1.1. Compile sur les 2 environnements PlatformIO. A VALIDER SUR LE MATERIEL apres reflash du pont (contournement sans reflash: renommer le fichier en un nom 8.3 sous Windows).
* Demande (version finale): (1) des '.' pour montrer la progression du chargement d'une image disque; (2) la trace du BIOS integree a la ROM officielle, activee/desactivee par Ctrl-Echap, pour tester sans changer de ROM. Ctrl-Echap n'arrive pas par l'UART (Windows l'intercepte; un terminal envoie 1Bh comme pour Echap): choix de l'utilisateur = Ctrl-] (1Dh) cote terminal + Ctrl-Echap cote clavier PS/2.
  - Trace (lib/bios.asm, lib/isr.asm): bios_trace_in/bios_trace_out sont desormais TOUJOURS assemblees; int13h_handler et int1ah_handler tracent si BIOS_TRC_ON (VAR_SEG 0FC54h) != 0; bios_return termine toute ligne commencee (BIOS_TRC) meme si la trace a ete coupee entre-temps. Bascule dans irq1_dispatch (donc aussi pendant la scrutation d'une commande au pont): octet UART TRACE_KEY (1Dh) -> trace_toggle, non range (comme Ctrl-\); clavier PS/2: ps2_hotkey suit Ctrl (14h, relachement F0 14, E0 ignore) dans les scan codes bruts et consomme le 76h (Echap) si Ctrl est enfonce -> trace_toggle. trace_toggle annonce "[Trace BIOS ACTIVE ...]" / "[Trace BIOS ARRETEE]" (FR/EN). Arretee au demarrage (RAM effacee). BIOS_TRACE=1 (`make trace`, solution-01-trace.bin) = trace active des bios_init + carte memoire bios_memmap (seule partie encore conditionnelle).
  - Points (lib/bios.asm): int19h_handler pose BIOS_DOTS (0FC55h) apres "Amorce: ..." (image ou disque); bios_dot ('.' par INT 13h AH=02h/42h, sauf trace active) ; bios_dots_end (CRLF, BIOS_DOTS = 0) au premier INT 10h (bios_int10_std: premier affichage du DOS) ou sur un echec de l'amorcage. PS2_HOTKEY_OFF = 0FC56h. (Variables prises dans le trou libre 0FC54h-0FC63h de VAR_SEG, PAS en fin du tampon d'edition 0FBFxh que l'editeur RAM ecrase.)
  - Verifie: make all/check/check-modules + TEST_PS2 + make test (13/110/323 verification(s), 0 echec(s)); ROM FR/EN/trace (check_rom.py), copiees dans Z:\Partage\Alain par make rom-fr/rom-en/trace. Emulation (IRQ1 asynchrones, ROM complete): PC-DOS 2.1 s'amorce avec 34 points puis passage a la ligne avant "Current date"; Ctrl-] a l'invite A> -> annonce + lignes <13 ...>/<1A ...> completes pendant DIR; Ctrl-] -> "[Trace BIOS ARRETEE]", VER/ECHO normaux; Ctrl-] pendant l'amorcage: trace puis reprise des points. README.md mis a jour. A VALIDER SUR LE MATERIEL: Ctrl-] depuis le terminal, Ctrl-Echap au clavier PS/2.
* Ctrl-] intapable dans PuTTY (clavier francais: ] = AltGr): touche UART de la trace remplacee par Ctrl-T (14h, TRACE_KEY, lib/isr.asm; inutilisee par le moniteur, le BASIC, PC-DOS 2.1 et MS-DOS 3.30). Ctrl-Echap confirme fonctionnel au clavier PS/2 sur le materiel. make test 0 echec, ROM FR/EN/trace copiees dans Z:\Partage\Alain.
* Rapporte: sous DOS 2.1, copy con SANS trace a provoque un redemarrage du CPU (retour au menu); AVEC trace active, nombreux copy/copy con/del sans aucun plantage. Le probleme depend donc du rythme (la trace ralentit et espace les echanges avec le pont).
* Trace: INT 1Ah AH=00h (lecture des ticks) n'est plus tracee - DOS 3.30 l'appelle en boucle (~ toutes les 0,6 s) a l'invite, la trace defilait sans intervention. INT 13h et les autres fonctions INT 1Ah restent tracees. Verifie: make test 0 echec; emulation DOS 3.30 avec Ctrl-T: 88 lignes INT 13h, 0 INT 1Ah AH=00h, 5 autres INT 1Ah (heure/date). Note: chaque INT 1Ah AH=00h est un echange complet avec le pont (commande + 8 octets, IR1 masquee/demasquee) - DOS parle au pont en continu meme au repos. Le filtre retire une partie du ralentissement du a la trace: si la stabilite 'avec trace' en dependait, les plantages pourraient revenir trace active (indice supplementaire).
* Trace DOS 2.1 du gel pendant 'copy test?.* test?.abc' (trace active, Ctrl-\ sans effet, RESET du 8088 necessaire): derniere ligne complete = INT 13h AH=03 ecriture de la FAT n°1 (CX=0002, tampon 00EB:3F9A) reussie; ligne suivante = ecriture de la FAT n°2 (CX=0004, meme tampon) INACHEVEE, suivie de 2 octets inattendus sur l'UART ('▒,') - le 8088 s'arrete au DEBUT de l'ecriture qui suit immediatement une ecriture reussie sur la flash du pont. Emulation du meme scenario (3 fichiers TEST*.TXT, copie a jokers): aucun gel, avec ou sans trace. Piste privilegiee: electrique (courant de programmation de la flash SPI du pont - le pont et sa flash sont alimentes par l'USB du PC, le montage par une alimentation 5 V 2 A separee: verifier la masse commune et l'absence de 5 V relies). Journal brut PuTTY demande pour identifier les octets '▒,'.
  - ESSAI (ROM distincte, `make rom-pause` -> solution-01-pause.bin, copiee dans Z:\Partage\Alain): BRIDGE_WRITE_PAUSE (lib/bridge.asm, 0 par defaut = ROM officielle identique a l'octet pres) = 1400 tours de LOOP (~5 ms a 4,77 MHz) a la fin de chaque ecriture de secteur (fs_blk_write, apres la reponse du pont, CF conserve). Verifie: ROM officielle inchangee (cmp), make check/check-modules/test (0 echec), emulation DOS 2.1 avec la pause (copy con x2, copie a jokers, del, dir) correcte. A VALIDER SUR LE MATERIEL: si DOS 2.1 ne plante plus pendant les ecritures avec cette ROM, le probleme suit la programmation de la flash du pont.
* Rapporte sur le materiel reel: solution-01-fr.bin (scrutation + trace Ctrl-T/Ctrl-Echap + filtre INT 1Ah AH=00h + points d'amorcage) semble solide sous DOS 2.1 et DOS 3.30, avec ou sans trace. Un gel isole reste a expliquer (copie a jokers sous DOS 2.1, trace active, au debut d'une ecriture qui suit une ecriture reussie - voir plus haut); mesures electriques et essai de solution-01-pause.bin en cours cote utilisateur.
* Publication de la version 1.2: BIOS_VERSION_MINOR 0 -> 2 et splash LCD 'Version 1.2' (solution-01.asm, affiches par '4) Information'); firmware du pont: 1.1. make all/check/check-modules/TEST_PS2/test (13/110/323, 0 echec); ROM FR/EN/trace/pause regenerees et copiees dans Z:\Partage\Alain. Tag v1.2 et release GitHub (wsl gh).
* Demande (Manifest.md): relier le RESET du 8088 a une broche du STM32 - redemarrer le 8088 par une sequence clavier (le clavier est branche sur le pont), tenir RESET haut au demarrage du pont jusqu'a ce qu'il soit pret, puis remettre la broche en ENTREE (ne pas gener le bouton RESET du montage; 10 kohm tirent RESET a la masse). Choix de l'utilisateur: PB2 (tolerante 5 V; BOOT1, compatible avec le DFU puisque la ligne est BASSE au repos) et Ctrl-\ au terminal = reset MATERIEL (en plus de Ctrl-Alt-Suppr au PS/2).
  - Fait (arduino/8088_bridge_stm32/src/main.cpp, firmware 1.2): reset8088Hold (PB2 sortie HAUTE: ODR puis MODER, jamais d'impulsion basse) / reset8088Release (entree sans pull); setup() commence par reset8088Hold, puis clockSetup (le 8088 a une horloge pendant son reset), et relache RESET a la toute fin (+10 ms). reset8088Pulse: RESET haut, oubli de l'ancienne session (tampon PS/2, file 8088->peripheriques, reponses en attente, commande partielle, uartHoldUntil), 10 ms, relache. Ctrl-Alt-Suppr: kbdTrack(), appelee par ps2Isr pour chaque octet (Ctrl 14h/E0 14h, Alt 11h/E0 11h, Suppr 71h/E0 71h, relachements F0) - detecte meme si le 8088 ne lit plus rien. Ctrl-\ (1Ch) au terminal: n'est plus transmis au 8088 (son ISR faisait un redemarrage LOGICIEL, sans effet quand il est fige) - reset materiel; si IBF reste a 1 plus de 500 ms (8088 fige: le terminal n'est plus lu), le pont vide le tampon du terminal a la recherche de Ctrl-\ (les autres octets sont perdus). Logique de kbdTrack verifiee par simulation (Ctrl G/D + Alt/AltGr + Suppr/Suppr du pave: reset; Suppr seul, Ctrl+Suppr, modificateurs relaches, relachement de Suppr: rien). Compile sur les 2 environnements PlatformIO. READMEs (pont: tableau de cablage, broches, point BOOT1; Solution-01: reset materiel) mis a jour. ROM du 8088 inchangee (le chemin logiciel de Ctrl-\ reste pour un pont plus ancien). A VALIDER SUR LE MATERIEL: cabler PB2 -> RESET (21) du 8088, flasher le pont; demarrage du pont, Ctrl-Alt-Suppr, Ctrl-\ (aussi avec le 8088 fige), bouton RESET toujours fonctionnel, entree en DFU.
* Confirme sur le materiel reel (pont 1.2, PB2 -> RESET du 8088): televersement DFU toujours fonctionnel; Ctrl-Alt-Suppr au clavier PS/2 et Ctrl-\ au terminal UART font le reset materiel du 8088.
* Rapporte: le copier-coller est brise (BASIC et DOS): '60 PI = 3.14159265' -> seul '60' arrive; un programme entier -> fragments. Emulation de la ROM complete (collage du programme au BASIC, rythme ~ pont): AUCUNE perte - la ROM n'est pas en cause. Suspect: pont 1.2 (seul endroit qui lit le terminal sans transmettre = la vidange du 'Ctrl-\ quand le 8088 est fige'). Detection 'fige' corrigee: IBF = 1 ET plus rien envoye au 8088 depuis STUCK_MS (lastTx), au lieu de IBF = 1 vu a chaque debut de boucle (un tour plus long que GAP_US - echo USB + LCD I2C - revoyait toujours IBF = 1 juste apres l'envoi suivant). Compile sur les 2 environnements. Firmwares a flasher pour trancher: Z:\Partage\Alain\pont-1.2b.bin (corrige) et pont-1.1.bin (reference, avant le reset materiel). A VALIDER SUR LE MATERIEL.
* Confirme sur le materiel reel (pont 1.2 corrige, flashe par PlatformIO; ROM 1.2): copier-coller de nouveau fonctionnel. (Incident: les firmwares du pont deposes dans Z:\Partage\Alain ont ete graves par erreur dans l'EEPROM du 8088 - retires; le pont se flashe desormais uniquement par PlatformIO en DFU.)
* Demande: conserver dans le depot les bancs d'emulation ecrits pendant la session (ils ne vivaient que dans le dossier temporaire de la session).
  - Fait: tests/rom_sim.py - simulateur Unicorn du 8088 AVEC son materiel: la ROM COMPLETE (run_rom: le binaire que l'on grave, depuis le vecteur de reset) ou tests/bios_test.asm (run_bios: BIOS + ISR + pont), chaque octet du pont et chaque frappe passant par le 8255 modelise (IBF, etiquettes PC0/PC1, octet suivant depose des que le precedent est lu), le 8259 (masque IMR sur 21h, une IRQ1 a la fois jusqu'a l'EOI, livree seulement si IF = 1) et l'ISR via l'IVT - contrairement a basic_harness/bios_test, qui deposent les octets dans les tampons. Pont = BridgeModel. Pilotage par scenario (texte attendu sur l'UART -> touches), aussi en ligne de commande (`python tests/rom_sim.py --image ... scenario.txt`, exemple tests/scenario_dos21.txt). Recherche du texte attendu seulement quand l'UART a recu un octet (et non a chaque bloc d'instructions).
  - tests/rom_test.py (`make test-rom`, ~2 min; `make test-rom-complet` en plus): MS-DOS 3.30 (copy con/type/del/dir), PC-DOS 2.1 (copy con x2, copie a jokers, del, points d'amorcage), trace Ctrl-T (lignes INT 13h completes, INT 1Ah AH=00h filtre), et pour chaque DOS: aucune interruption non implementee + reponses du pont lues par SCRUTATION (IR1 masquee/demasquee, < 2000 IRQ1); --complet: ROM complete - DOS 2.1, Ctrl-\, reamorcage, VER; collage au BASIC du programme tests/sine.bas (LIST identique). Resultat: 13 verification(s), 0 echec(s); exemple en ligne de commande termine (15 IRQ1). Hors de `make test` (duree). README (arborescence, commandes, paragraphe sur le simulateur) mis a jour.
* Rapporte sur le materiel reel: la progression du test de vitesse (Configuration -> 2) et l'heure de l'ecran Information (Configuration -> 4) n'avancent plus seules - il faut appuyer sur une touche du clavier PS/2 a chaque pas.
  - Cause (lib/ps2.asm, solution-01.asm): la verification "Echap" non bloquante faisait `ps2_key_available` puis `ps2_get_char`. Le RELACHEMENT de la touche qui lance l'action (F0 1E pour '2', F0 25 pour '4') reste dans le tampon PS/2: ps2_key_available le signale, ps2_get_char l'avale puis ATTEND une touche reconnue - chaque frappe ne faisait avancer que d'un pas (et son propre relachement bloquait le pas suivant). Invisible au terminal UART (pas de relachement), d'ou le passage inapercu dans les bancs d'essai.
  - Reproduit AVANT correction: tests/rom_sim.py accepte desormais des frappes PS/2 (`ps2(scan codes)`: appui + F0 + relachement, etiquette PC0=PC1=0); test de vitesse fige des le 1er checkpoint, heure jamais rafraichie.
  - Correctif: nouvelle routine `ps2_poll_char` (lib/ps2.asm): memes sorties que ps2_get_char (AL, BH), CF=1 si rien de RECONNU n'attend - consomme relachements/touches ignorees (PS/2 et UART) puis rend la main. ps2_get_char devient une attente sur ps2_poll_char (comportement inchange). Les 3 verifications d'Echap (dump_memory_action, cpu_speed_test_action, information_action) l'utilisent. INT 16h (bios_trykey) non concerne.
  - tests/rom_test.py (`make test-rom`): 2 nouvelles verifications au clavier PS/2 - test de vitesse termine seul (30 points) et Information rafraichie sans frappe (pont simule dont l'horloge avance) puis Echap. Toutes deux ECHOUENT sur l'ancien code.
* Demande: les commentaires du code et la documentation designaient encore le pont comme un "Arduino (UNO)" - le pont est la plaquette Black Pill STM32F411 (arduino/8088_bridge_stm32). Fait:
  - Commentaires (solution-01.asm, include/hardware.inc, lib/bridge.asm, common.asm, isr.asm, lcd_i2c.asm, ps2.asm, uart.asm): "l'Arduino" -> "le pont" (plaquette Black Pill STM32F411 nommee dans les en-tetes), "UART materiel" -> port serie USB natif. Garde tel quel: "l'Arduino UNO R4 separe" (ancienne carte d'horloge, historique exact). Identifiants NON renommes (arduino_send, irq1_arduino_handler, ARD_*): leur origine est expliquee dans le README.
  - Texte affiche par la liste des vecteurs (IVT, IR1): "(Arduino, 8255 mode 2, IR1)" -> "(pont STM32, ...)" / "(STM32 bridge, ...)". Verifie: hors ce texte, la ROM FR ET EN est identique a l'octet pres a la precedente (seuls des commentaires ont change).
  - Solution-01/README.md et README.md (racine, copie plus ancienne): intro "Architecture pont", materiel et table de cablage du Black Pill (broches de arduino/8088_bridge_stm32/README.md: PB12-15/PB6-9, PB0 ACK#, PB1 STB#, PA8 OBF#, PA15 IBF, PB4 TAG, PB5 TAG1, PA9/PA10 canal, PA3 CLK, PB2 RESET, PA1/PA2 PS/2, PB10/PB3 I2C), schema bloc, section "Pont STM32 (8255 en mode 2)" (cote pont: main.cpp, reglages, compilation PlatformIO au lieu d'arduino-cli), terminal = port serie USB (plus de 57600 8N1), outils (PlatformIO). L'ancien pont UNO (arduino/ve2cuy_bridge) est mentionne comme historique. README racine: chemins ../arduino/ -> arduino/.
  - Non modifies (exacts ou hors documentation): Directives.md (journal historique), arduino/8088_bridge_stm32 (l'UNO y est cite comme origine du portage; framework = arduino est le nom du framework PlatformIO), arduino/ve2cuy_bridge et irq_test (anciens croquis UNO), schemas KiCad.
  - Verifie: make all/check/check-modules + TEST_PS2 + make test (13/110/323, 0 echec) + make test-rom (13, 0 echec); ROM FR/EN copiees dans Z:\Partage\Alain.
* Confirme par l'utilisateur (2026-09-24): le fil PC5 (IBF du 8255) -> PA15 du pont est branche - conforme au reglage par defaut USE_IBF 1 du pont. Le schema KiCad (kicad/Partie03.kicad_sch) ne montre pas encore cette liaison.
* Demande: rediger README_fr.md, page d'accueil concise du depot GitHub (resume, montage, circuit, pont, menu, tableau des commandes du BASIC, DOS 2.1/3.3, captures), destinee a remplacer README.md (trop detaille pour un premier contact) - README.md NON supprime. Fait:
  - README_fr.md (racine): en bref, montage (schema KiCad du coeur medias/breadboard-step-02.png, legende: horloge desormais fournie par le pont), schema bloc Mermaid a jour (8088, ROM, RAM, 8255, 8259, pont Black Pill, PS/2, USB, LCD, flash), fonctions du pont, menu, BASIC (tableau par categorie), DOS 2.1/3.3 et limites, construction, organisation du depot; renvoie a Solution-01/README.md pour le detail.
  - Captures du terminal: medias/captures/{menu,basic,dos21,dos33}.svg, produites par medias/captures/generer.py - la ROM reelle executee par tests/rom_sim.py, sortie UART rejouee par un petit emulateur ANSI (80 colonnes, couleurs) puis ecrite en SVG (espaces insecables pour conserver les colonnes). Regenerer: python medias/captures/generer.py [menu basic dos21 dos33].
  - kicad/Partie03 (8255 ajoute) ecarte: chantier en cours (8255 non relie, ni 8259 ni pont). Aucune photo du montage dans le depot.
* Photo du montage deposee par l'utilisateur sur GitHub (medias/breadboard-pc.png, commit e311b3e): c'est en realite une photo HEIC (iPhone, 2819x3648) avec l'extension .png, illisible par les navigateurs. Convertie en medias/breadboard-pc.jpg (1600 px de large, JPEG qualite 85, 0,8 Mo; Pillow + pillow-heif), placee en tete de README_fr.md (le LCD y affiche l'ecran Information); la capture du menu passe dans la section Le menu. Le fichier .png d'origine est laisse tel quel.
* Sur demande: medias/breadboard-pc.png (HEIC) supprime - remplace par medias/breadboard-pc.jpg; tous les commits pousses sur origin/master.
* Nouveau dossier code-examples/ ajoute au depot: hello.asm (programme .COM MASM pour DOS, affichage par INT 10h AH=0Eh) et sin.bas (courbe de SIN en ASCII, chronometree par TIMER, puis dessin d'un requin - miroir horizontal fait sur demande: le requin pointe vers la droite).
* README_fr.md: precise que le code source de la ROM est entierement ecrit en assembleur 8086 (NASM), BASIC compris.
* README_en.md: version anglaise de README_fr.md (liens croises entre les deux). Captures anglaises medias/captures/{menu,basic,dos21,dos33}_en.svg produites par la ROM anglaise (LANG_EN): nouvelle option --en de medias/captures/generer.py (titres de fenetre bilingues).
* La version anglaise devient la page d'accueil du depot: README_en.md renomme README.md; l'ancien README.md (copie anterieure de Solution-01/README.md, documentation technique detaillee) renomme DOCUMENTATION_TECHNIQUE.md, avec une note de tete qui renvoie a Solution-01/README.md (a jour), README.md et README_fr.md. Liens mis a jour (README_fr.md, generer.py).
* DOCUMENTATION_TECHNIQUE.md supprime: copie plus ancienne et incomplete de Solution-01/README.md (197 lignes de moins, 7 lignes perimees), qui reste la documentation technique de reference.
* Solution-01/README.md: references aux ajouts du 2026-09-24 - ps2_poll_char (table de lib/ps2.asm, avertissement sur ps2_key_available+ps2_get_char, Echap pendant un dump/test de vitesse/Information), frappes PS/2 du simulateur (ps2()) et verifications PS/2 de make test-rom, generateur de captures, arborescence du depot mise a jour (breadboard-PC: README.md/README_fr.md, medias/captures, code-examples, kicad, PC-DOS).
* Demande: modele 3D d'un support ZIF 32 broches pour KiCad. KiCad fournit l'empreinte Socket:DIP_Socket-32_W11.9mm_W12.7mm_W15.24mm_W17.78mm_W18.5mm_3M_232-1285-00-0602J (3M Textool, ZIF universel 0,3" a 0,6"), mais le modele 3D qu'elle reference (Socket.3dshapes/...step) n'est pas installe (ni KiCad 8 ni 10). Fait: kicad/3dmodels/zif32_3m_232-1285.py (CadQuery, parametrique) -> <nom de l'empreinte>.step et .wrl. Vue de dessus reprise du contour F.Fab de l'empreinte (boitier 22,9 x 55,5 mm, chanfrein, levier et poignee), origine = pastille 1; hauteurs supposees (boitier 10,2 mm, broches 3,5 mm sous la carte), ajustables en tete du script. Verifie par un rendu kicad-cli pcb render d'une carte d'essai: boitier sur la serigraphie, fentes sur les pastilles, levier sur le dessin de l'empreinte. CadQuery 2.8 installe dans un venv temporaire (Python 3.11 de KiCad; venv absent sous WSL).
* CadQuery installe par l'utilisateur sous PowerShell (CadQuery 2.8.0, Python 3.14.6 - la 3.14 convient, contrairement a ce qui avait ete suppose): kicad/3dmodels/zif32_3m_232-1285.py y tourne tel quel; geometrie identique au modele commite (VRML identique a l'octet pres; STEP: seuls l'horodatage et l'ordre des styles de couleur different). Regenerer: python kicad\3dmodels\zif32_3m_232-1285.py
* Modele 3D du ZIF 32 installe pour tous les projets: copie (avec elevation UAC) dans C:\Program Files\KiCad\10.0\share\kicad\3dmodels\Socket.3dshapes\ - chemin que reference l'empreinte standard. Dans kicad/Breadboard-pc/Breadboard-pc.kicad_pcb, le modele de U4 pointait vers ${KIPRJMOD}/../3dmodels/...step suivi d'une ESPACE (fichier introuvable): remis au chemin standard ${KICAD10_3DMODEL_DIR}/Socket.3dshapes/...step. Verifie par kicad-cli pcb render: le support apparait sur la carte. (Une mise a jour de KiCad peut effacer ce dossier: recopier le .step de kicad/3dmodels/.)
* Schema kicad/Breadboard-pc: ajout du connecteur du clavier - le symbole cherche est Connector:USB_A de KiCad (prise USB 2.0 type A). J1 place a gauche du Black Pill: D+ -> PA1 (etiquette PS2_CLK), D- -> PA2 (PS2_DATA), VBUS -> +5V, GND et blindage -> GND (clavier USB en mode PS/2, cablage du README). Empreinte proposee: Connector_USB:USB_A_Molex_67643_Horizontal. Retire les marqueurs 'non connecte' de PA1/PA2. ERC: aucune nouvelle erreur due a l'ajout. Resistances de tirage PS/2 (4,7-10 kOhm vers +5V) pas encore au schema.
* Schema kicad/Breadboard-pc (a la demande): barrette male 1x4 du LCD I2C et cablage des broches restantes selon les notes du projet (README du pont, Solution-01/README.md). Choix de l'utilisateur: quartet haut du bus INVERSE comme sur la plaquette (PB6->PA7, PB7->PA6, PB8->PA5, PB9->PA4: le pont 1.2 et BUS_HIGH_NIBBLE_REVERSED 1 fonctionnent tels quels) et ajout du 8259.
  - J2 (Connector:Conn_01x04_Pin, PinHeader_1x04): 1 GND, 2 +5V, 3 LCD_SDA (PB3), 4 LCD_SCL (PB10).
  - Pont U5 <-> 8255 U11 par etiquettes: BUS_PA0-PA3 (PB12-PB15), BUS_PA4-PA7 (PB9-PB6), ACK_ (PB0-PC6), STB_ (PB1-PC4), OBF_ (PA8-PC7), IBF (PA15-PC5), TAG (PB4-PC0), TAG1 (PB5-PC1), CANAL0/1 (PA9/PA10-PB0/PB1). PB2-PB7 et PC2 du 8255 marques non connectes.
  - Tirages: R2/R3 10k vers +5V (ACK_, STB_), R4 10k vers la masse (TAG1/PC1), R5/R6 4,7k vers +5V (PS2_CLK, PS2_DATA).
  - 8259 U7 (Interface:8259A, DIP-28): D0-D7, A0, RD_, WR_, CS8259_ = NAND(IO, A6, /A7) par U10A (74LS10, nouvelle) avec /A7 = U9B (74LS00 en inverseur); INT -> INTR du 8088 (INTR retiree de la masse), INTA_ <- 8088; IR1 <- IRQ1 (PC3 du 8255); IR0 <- bouton SW2 vers +5V avec rappel R7 10k; IR2-IR7 a la masse; SP/EN a +5V (maitre unique); CAS0-2 non connectes. Unites d'alimentation de U9 (manquait deja) et U10 placees.
  - Verifie par kicad-cli: netliste (34 liaisons + 19 alimentations attendues, 0 ecart); ERC: aucune nouvelle erreur (deux erreurs existantes disparues: INTA du 8088 non connectee, alimentation de U9). Restent: lib_symbol_mismatch des +5V (comme les existants), portes libres U9C/D et U10B/C, HLDA/SSO du 8088, etiquette RESET de la feuille "STM32 Bridge" (untitled.kicad_sch).
  - Piege rencontre: une propriete Description contenant des guillemets non echappes ("GND") rend le schema illisible pour KiCad - echapper en \".
* Correction de l'utilisateur: le CS# du 8259 est NAND(IO, A5) sur une porte d'une 74LS00 (confirme sur la plaquette: A5, coherent avec les ports 20h/21h de la ROM - dans 20h c'est A5 qui vaut 1, pas A6). Les notes disaient a tort NAND(IO, A6, /A7).
  - Schema kicad/Breadboard-pc: U9B (porte libre de la 74LS00 existante) = NAND(IO, A5) -> CS8259_; retrait de la 74LS10 (U10), de son unite d'alimentation et de l'inverseur /A7.
  - Documentation corrigee: Solution-01/README.md (materiel, decodage, schema bloc Mermaid), commentaires de include/hardware.inc et de init_8259 (solution-01.asm) - ROM identique a l'octet pres. README.md / README_fr.md: correction a faire approuver.
* Schema kicad/Breadboard-pc (a la demande): alimentation, LED et source d'horloge.
  - J3 jack 5 V (Connector:Barrel_Jack, BarrelJack_Horizontal, centre +) avec PWR_FLAG sur +5V et GND (les 2 erreurs ERC "power pin not driven" disparaissent). LED D1 (LED_D3.0mm) + R8 1k entre +5V et GND.
  - JP1 (Jumper_3_Open, barrette 1x3): 1 = CLK_STM (PA3 du pont; l'etiquette globale CLK du pont est renommee CLK_STM), 2 = CLK (8088), 3 = CLK_EXT; J4 (barrette 1x2): entree d'horloge externe CLK_EXT + GND.
  - Bouton RESET: il existait deja (SW1 +5V -> RESET, rappel R1 4,7k): nomme "RESET", empreintes du bouton (SW_PUSH_6mm) et de R1 ajoutees.
  - Verifie par kicad-cli: 37 liaisons + 22 alimentations, 0 ecart; ERC sans nouvelle erreur (5 avertissements pin_to_pin: broches 5V/G du symbole Black Pill et SP/EN du 8259 declarees bidirectionnelles).
* README.md / README_fr.md (approuve par l'utilisateur): decodage du 8259 corrige en NAND(IO, A5), une porte de 74LS00.
